thereprocase/peg/publication/mh01-mh04-shaft-holders-v1.md

## MH01-MH04 v1 — magnetic shaft holders from the MS01 result (form review)

User reported the physical MS01 result on 2026-09-17: letters E, I, M, O, and asked
for final holders: a narrow six-seat E bar for jeweler drivers, eight seats each of
I and M, and a four-seat O bar with extra handle spacing, all tiling on the grid.
User chose paired four-seat modules for the eight-seat rows and sealed
pause-and-cap magnets.

`magnetic_shaft_holders.py` in the holder workspace reuses the MS01 seat, 0.8 mm
skin, sealed v2 pocket/plug and canonical fit e586ab4ff6. Only width, seat count
and pitch change. Seat pitch = cells x 25.4 / seats, so spacing continues across
the 2 mm seam. MH01 E 6 seats / 4 cells / 16.93 mm; MH02 I 4 / 7 / 44.45;
MH03 M 4 / 8 / 50.8; MH04 O 4 / 8 / 50.8. MH02 and MH03 print twice. 26 magnets.

CAD single solids, STEP round trips, peg flats on the bed plane, bearing contact,
lift/forward withdrawal with neighbours seated, 0.99-1.04 mm magnet gap and pause
loading path pass. Handle envelopes are nominal. NOT sliced, no supports review,
no pause-layer verification, no physical print. No job sent to a printer.

### Print kit — same day

User approved the forms and asked for the Orca job. Native P1S / 0.4 / Generic PLA /
textured PEI five-plate job with the MS01 v2 process overrides: 26 plugs 12.54 g /
41m48s; MH01 71.72 g / 3h1m29s; MH02 108.04 g / 4h2m19s (print twice); MH03
120.94 g / 4h27m40s (print twice); MH04 120.87 g / 4h23m24s. One native pause per
holder plate before layer 38.2 with 38.0 complete; zero extrusion inside any of the
18 magnet chimneys below 38.0; every chimney first closes at 38.2. Nothing outside
the bed, no mesh repairs, path accounting and startup clearance pass, embedded
settings reslice. Orca's bed-temperature notice retained. Desktop GUI opening,
support removal and the physical print remain untested. No job sent to a printer.
Second release: mh01-mh04-shaft-holders-v1-print-kit (print kit ZIP, PRINT-ME,
EDIT-ME). The first release's 13 assets are unchanged.

Gallery: https://thereprocase.github.io/peg/gallery/shaft-holders/
Release: mh01-mh04-shaft-holders-v1 (12 STEP files and the review CAD kit ZIP).
Receipts: `mh01-mh04-shaft-holders-v1-additions.json`; `tools/check_gallery.py`
verifies their hashes. Staged by `publish_magnetic_shaft_holders.py`.
