thereprocase/peg/docs/gallery/arrays/P01-12/rear.png

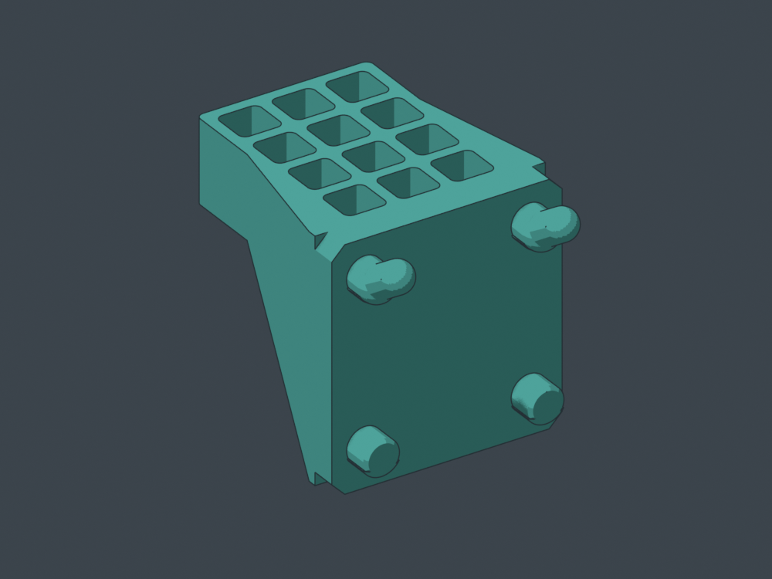
docs/gallery/arrays/P01-12/rear.png
