thereprocase/peg/docs/gallery/arrays/P01-24/front.png

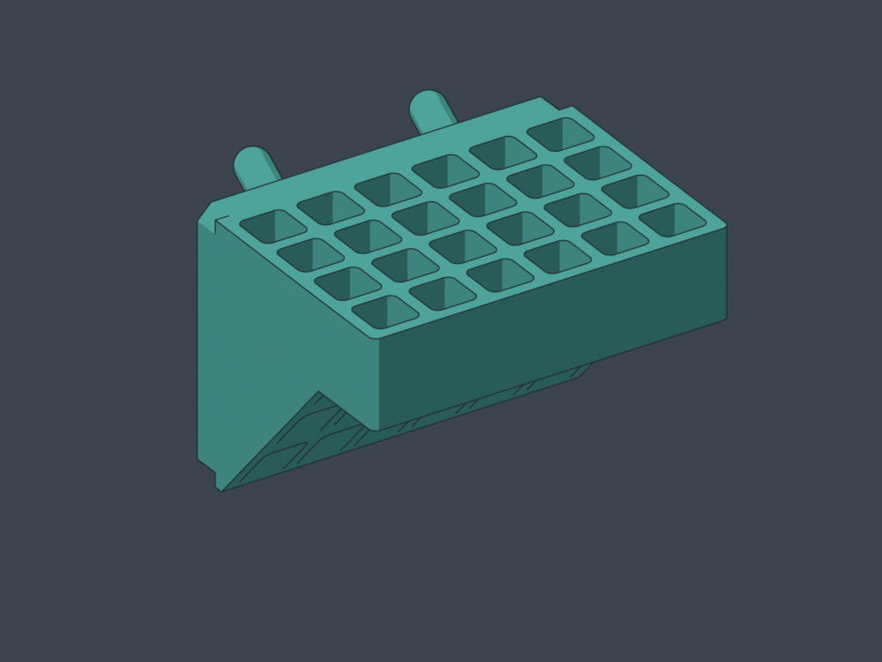
docs/gallery/arrays/P01-24/front.png
