thereprocase/peg/docs/gallery/arrays/P01-32/front.png

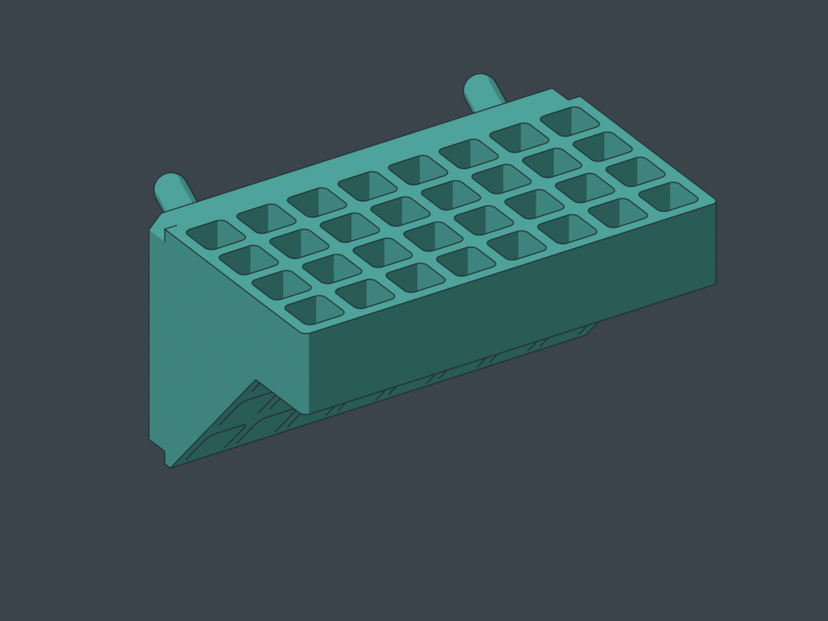
docs/gallery/arrays/P01-32/front.png
