thereprocase/peg/docs/gallery/arrays/P01-32/rear.png

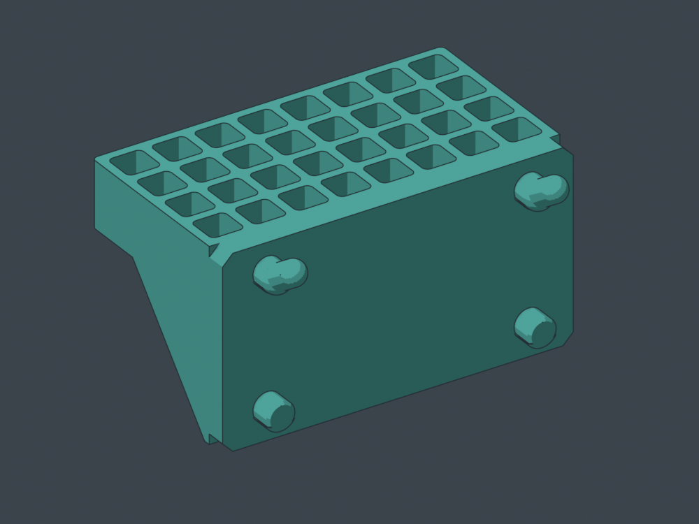
docs/gallery/arrays/P01-32/rear.png
