thereprocase/peg/docs/gallery/arrays/P01-48/rear.png

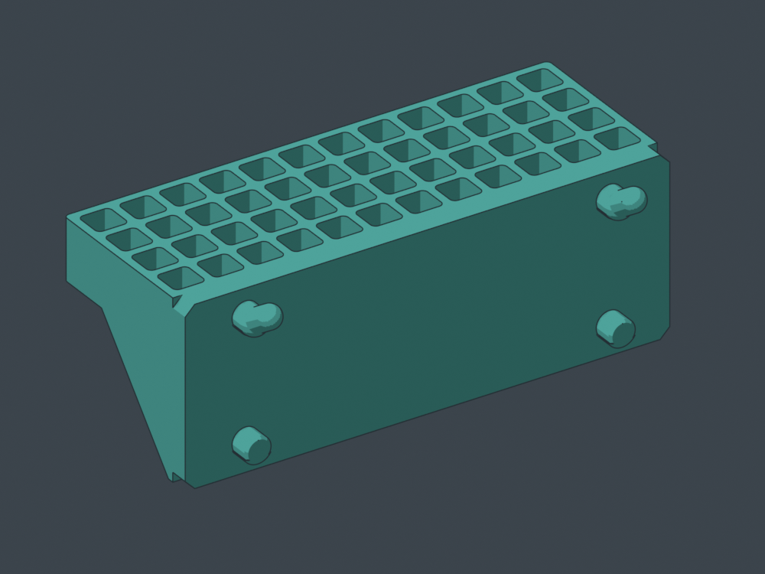
docs/gallery/arrays/P01-48/rear.png
