thereprocase/peg/docs/gallery/arrays/P01-labeled.png

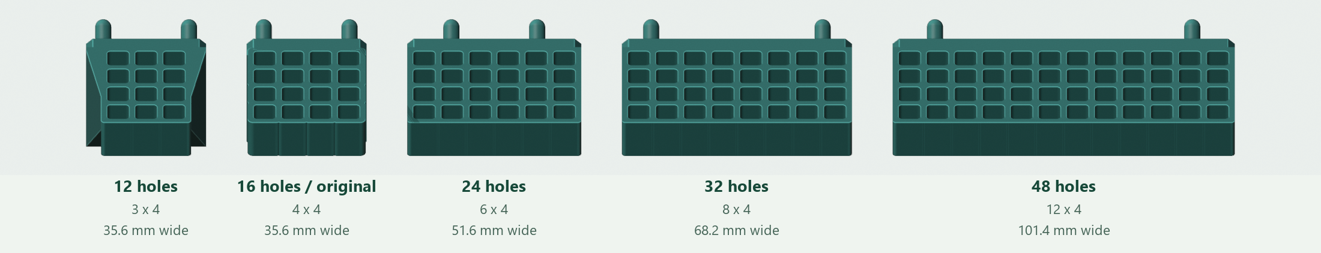
docs/gallery/arrays/P01-labeled.png
