thereprocase/peg/docs/gallery/arrays/P09-16/rear.png

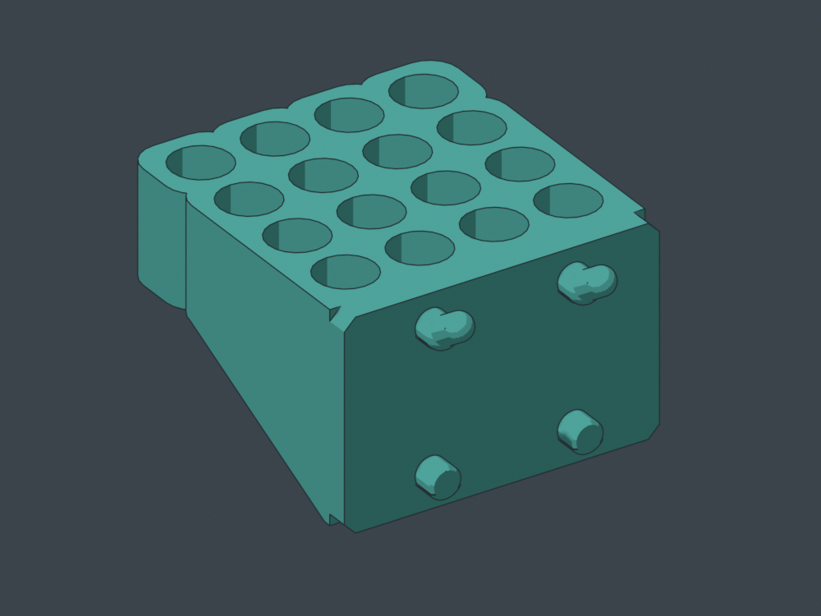
docs/gallery/arrays/P09-16/rear.png
