thereprocase/peg/docs/gallery/arrays/P09-36/front.png

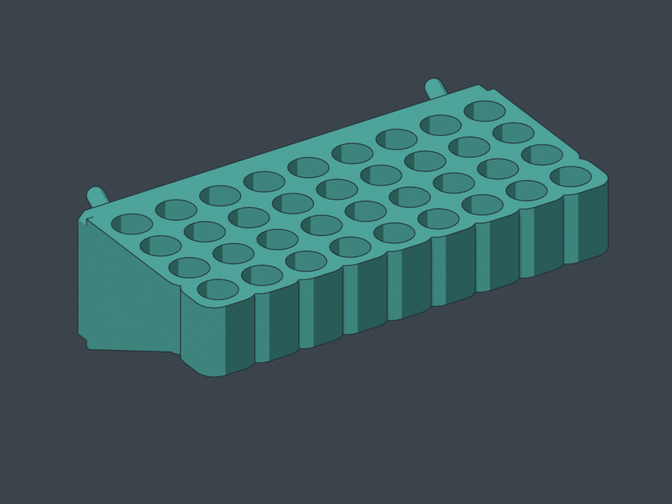
docs/gallery/arrays/P09-36/front.png
