thereprocase/peg/docs/gallery/arrays/P09-48/rear.png

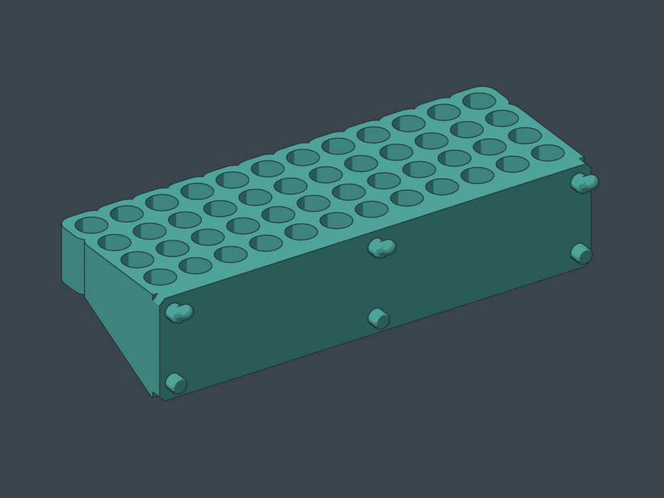
docs/gallery/arrays/P09-48/rear.png
