thereprocase/peg/docs/gallery/arrays/P09-comparison.png

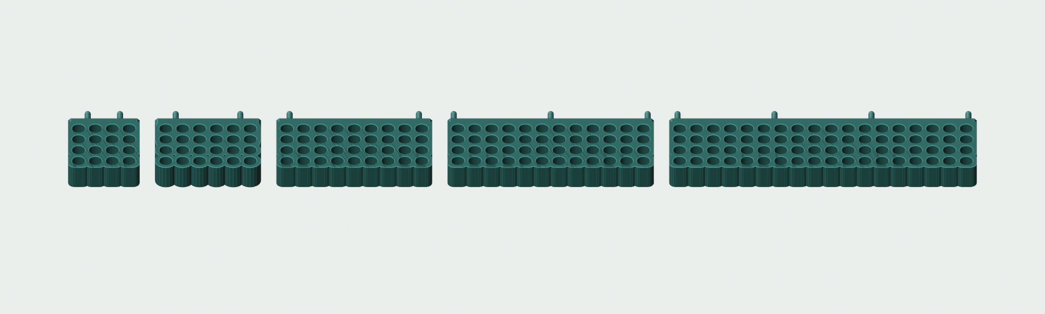
docs/gallery/arrays/P09-comparison.png
