thereprocase/peg/docs/gallery/bin-expansion/PB01/part-pb01__v1__pegstr-bin-4-cells-1-pockets-99.6x40x40mm__fit-e586ab4ff6__rear.png

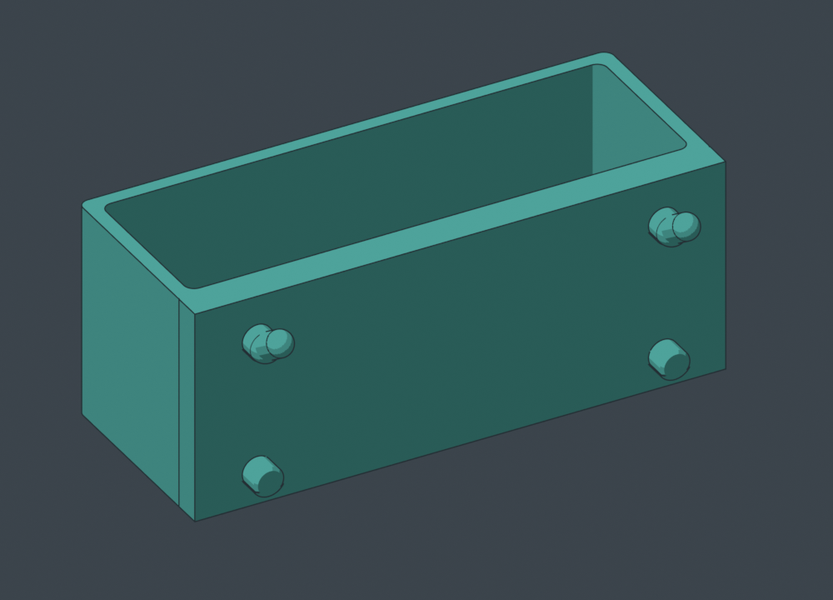
docs/gallery/bin-expansion/PB01/part-pb01__v1__pegstr-bin-4-cells-1-pockets-99.6x40x40mm__fit-e586ab4ff6__rear.png
