thereprocase/peg/docs/gallery/bit-drivers/part-bd01-slope-e__v1__rear-mounts.png

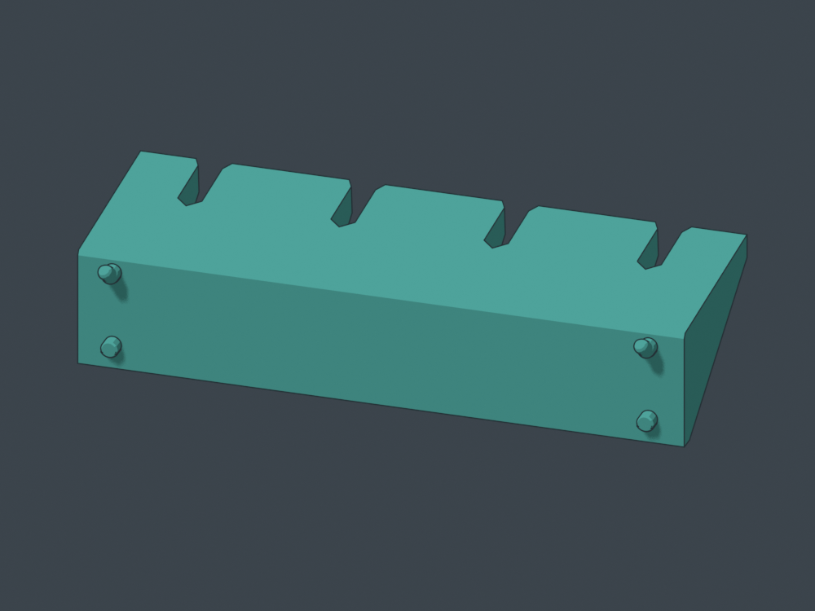
docs/gallery/bit-drivers/part-bd01-slope-e__v1__rear-mounts.png
