thereprocase/peg/docs/gallery/bit-drivers/part-bd01-slope-e__v4__bed-contact-faces.png

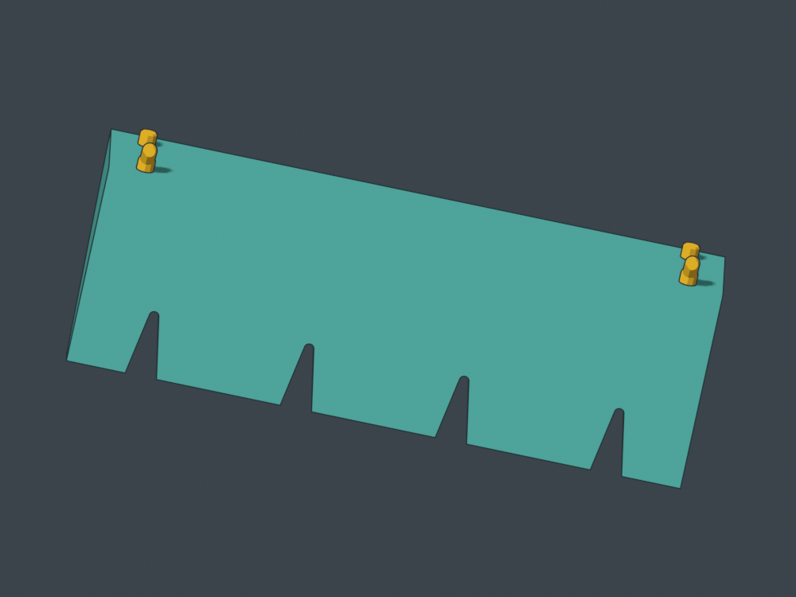
docs/gallery/bit-drivers/part-bd01-slope-e__v4__bed-contact-faces.png
