thereprocase/peg/docs/gallery/bit-drivers/part-bd01-slope-e__v4__loaded-review.png

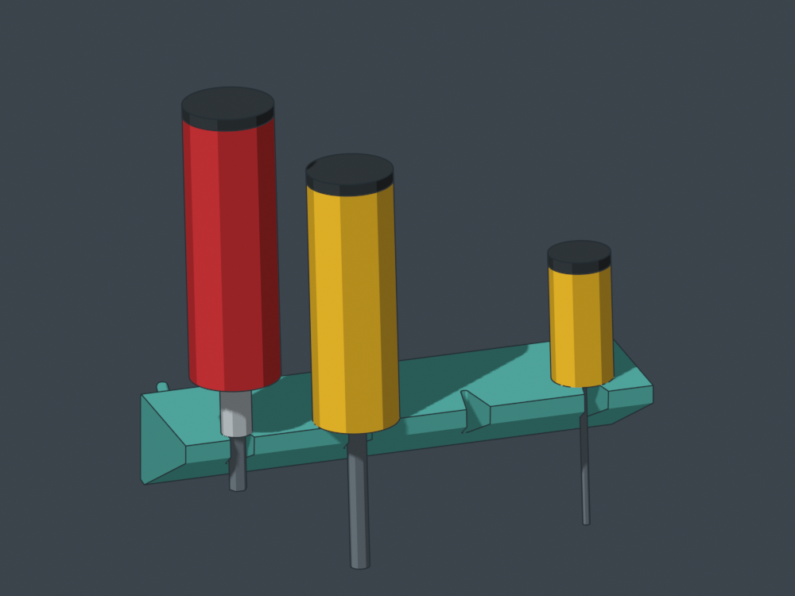
docs/gallery/bit-drivers/part-bd01-slope-e__v4__loaded-review.png
