thereprocase/peg/docs/gallery/current-pegs/part-ms01-i-p__current-mounts-v1__fit-pf02c9-hoop5__preview.png

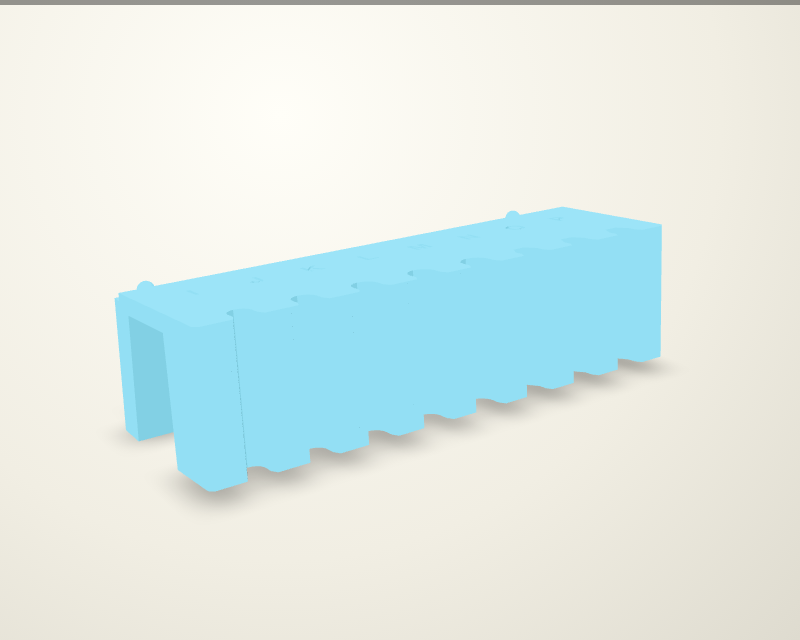
docs/gallery/current-pegs/part-ms01-i-p__current-mounts-v1__fit-pf02c9-hoop5__preview.png
