thereprocase/peg/docs/gallery/current-pegs/part-p09-48__current-mounts-flat-top-v2__fit-pf02c9-hoop5__preview.png

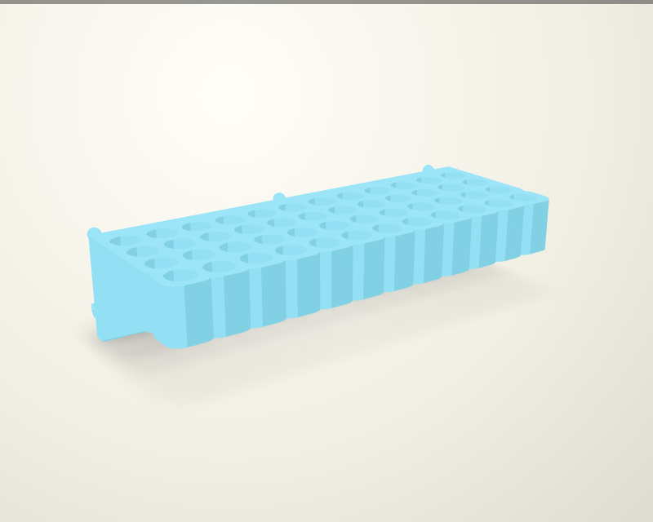
docs/gallery/current-pegs/part-p09-48__current-mounts-flat-top-v2__fit-pf02c9-hoop5__preview.png
