thereprocase/peg/docs/gallery/current-pegs/part-tweezers-v8__current-mounts-v1__fit-pf02c9-hoop5__preview.png

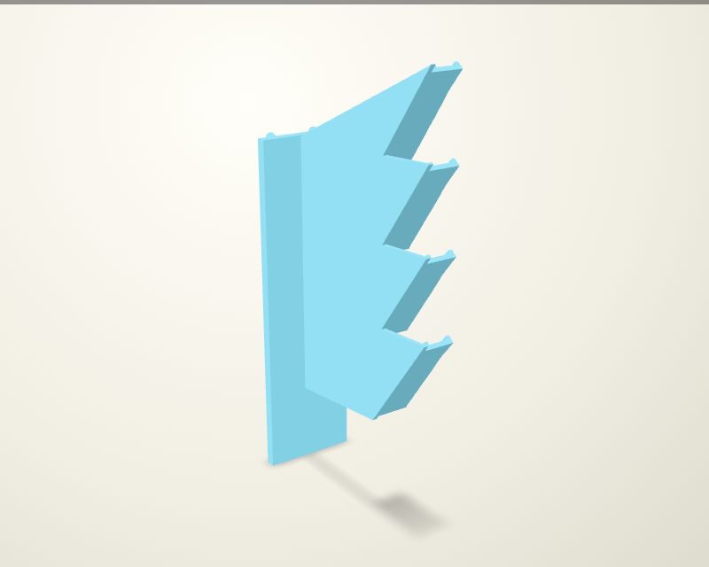
docs/gallery/current-pegs/part-tweezers-v8__current-mounts-v1__fit-pf02c9-hoop5__preview.png
