thereprocase/peg/docs/gallery/downloads/named/part-arrays-p09-48__v-src0e00429f35__pegstr-array-p09-48-round-seats__front-view.png

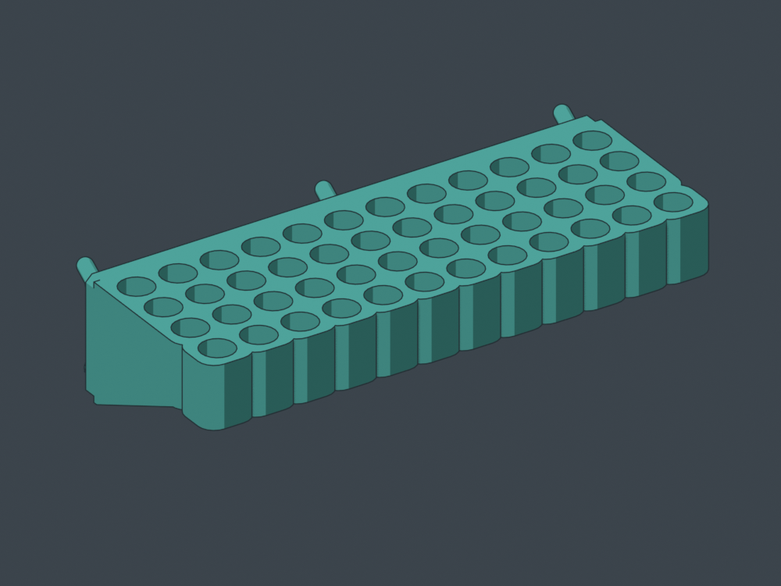
docs/gallery/downloads/named/part-arrays-p09-48__v-src0e00429f35__pegstr-array-p09-48-round-seats__front-view.png
