thereprocase/peg/docs/gallery/downloads/named/part-pegstr-p01__v2__pegstr-p01-16-small-square-seats__front-view.png

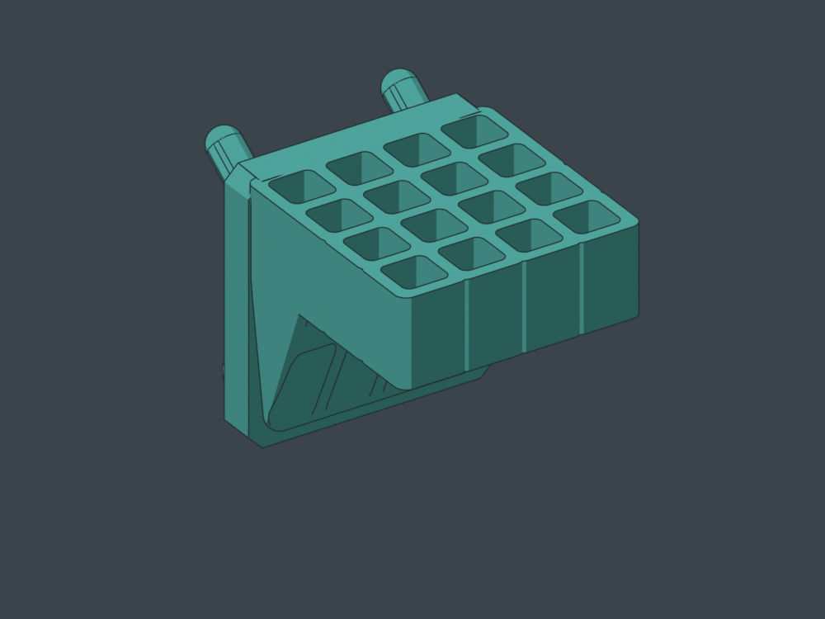
docs/gallery/downloads/named/part-pegstr-p01__v2__pegstr-p01-16-small-square-seats__front-view.png
