thereprocase/peg/docs/gallery/downloads/named/part-pegstr-p09__v2__pegstr-p09-24-round-seats__rear-view.png

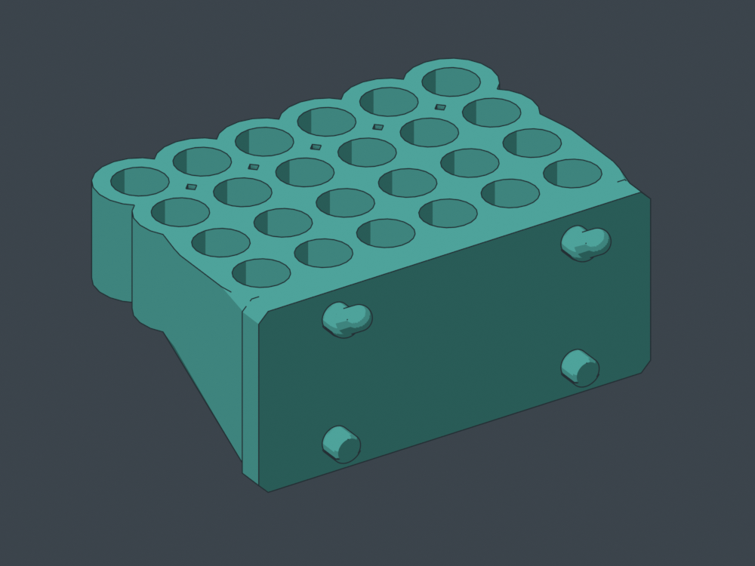
docs/gallery/downloads/named/part-pegstr-p09__v2__pegstr-p09-24-round-seats__rear-view.png
