thereprocase/peg/docs/gallery/downloads/named/part-pegstr-p10__v2__pegstr-p10-low-rectangular-slot__rear-view.png

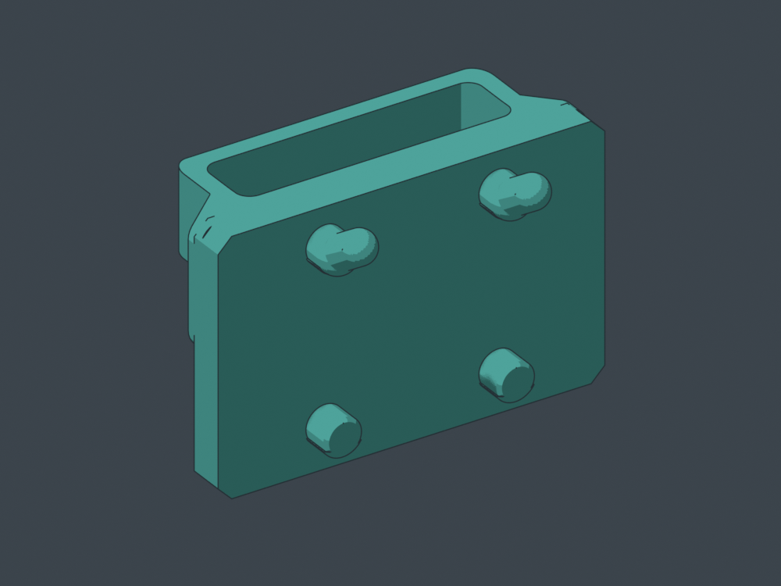
docs/gallery/downloads/named/part-pegstr-p10__v2__pegstr-p10-low-rectangular-slot__rear-view.png
