thereprocase/peg/docs/gallery/downloads/named/part-pegstr-p11__v2__pegstr-p11-caliper-slot__front-view.png

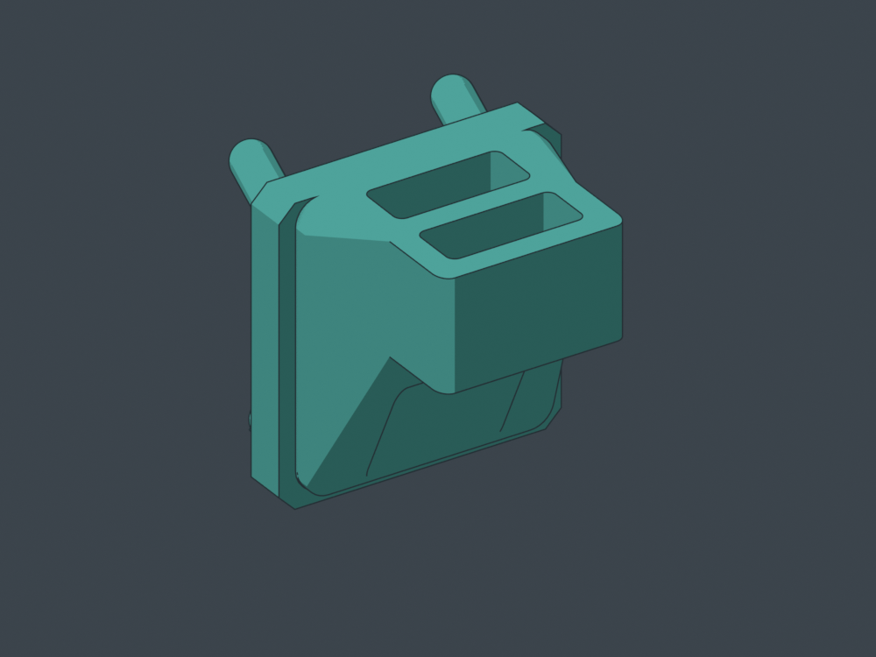
docs/gallery/downloads/named/part-pegstr-p11__v2__pegstr-p11-caliper-slot__front-view.png
