thereprocase/peg/docs/gallery/key-fan/final/HX04/empty.jpg

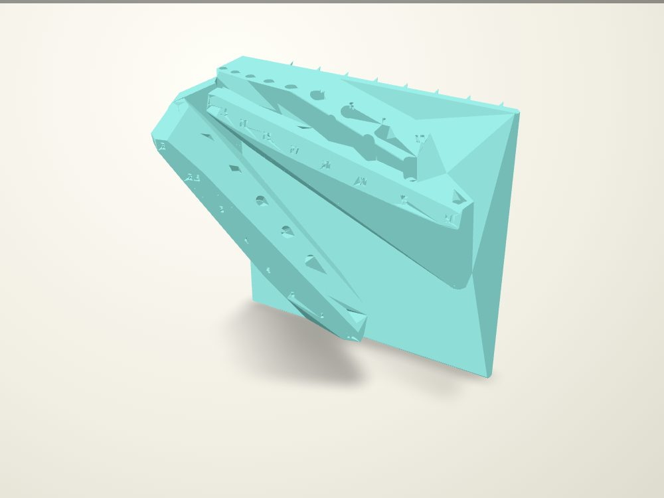
docs/gallery/key-fan/final/HX04/empty.jpg
