thereprocase/peg/docs/gallery/key-fan/final/HX05B/hero.jpg

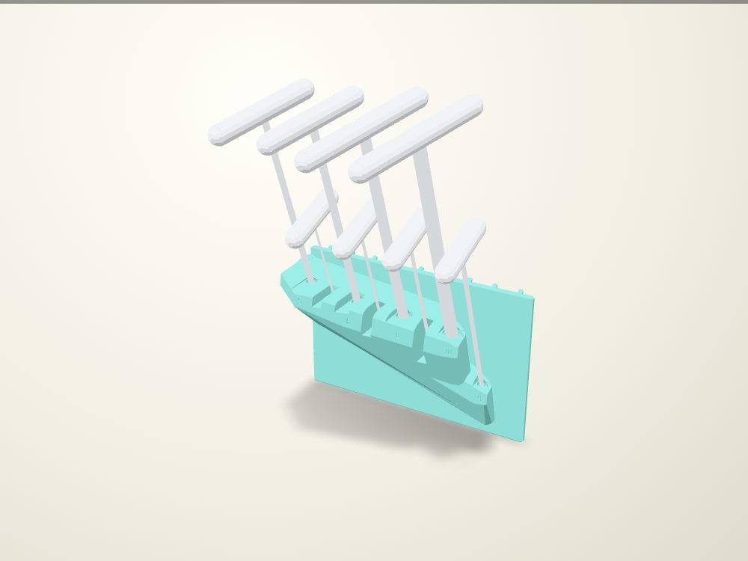
docs/gallery/key-fan/final/HX05B/hero.jpg
