thereprocase/peg/docs/gallery/key-fan/final/HX05C/empty.jpg

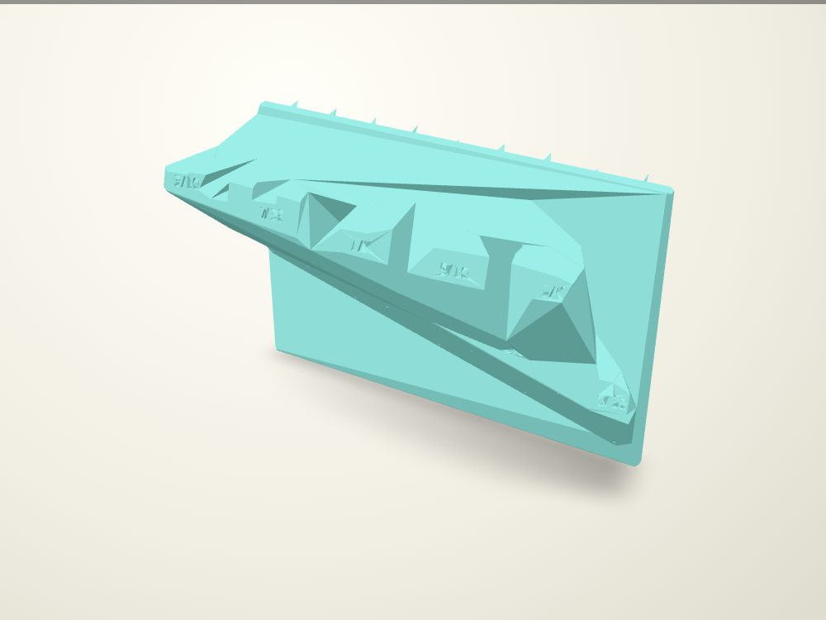
docs/gallery/key-fan/final/HX05C/empty.jpg
