thereprocase/peg/docs/gallery/key-fan/stacked/green/HX05C-front.jpg

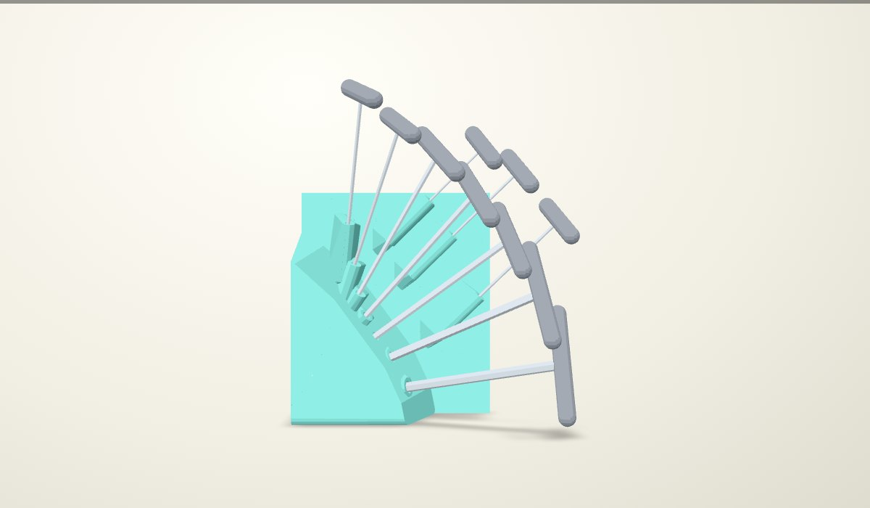
docs/gallery/key-fan/stacked/green/HX05C-front.jpg
