thereprocase/peg/docs/gallery/key-fan/stacked/HX05C-hero.jpg

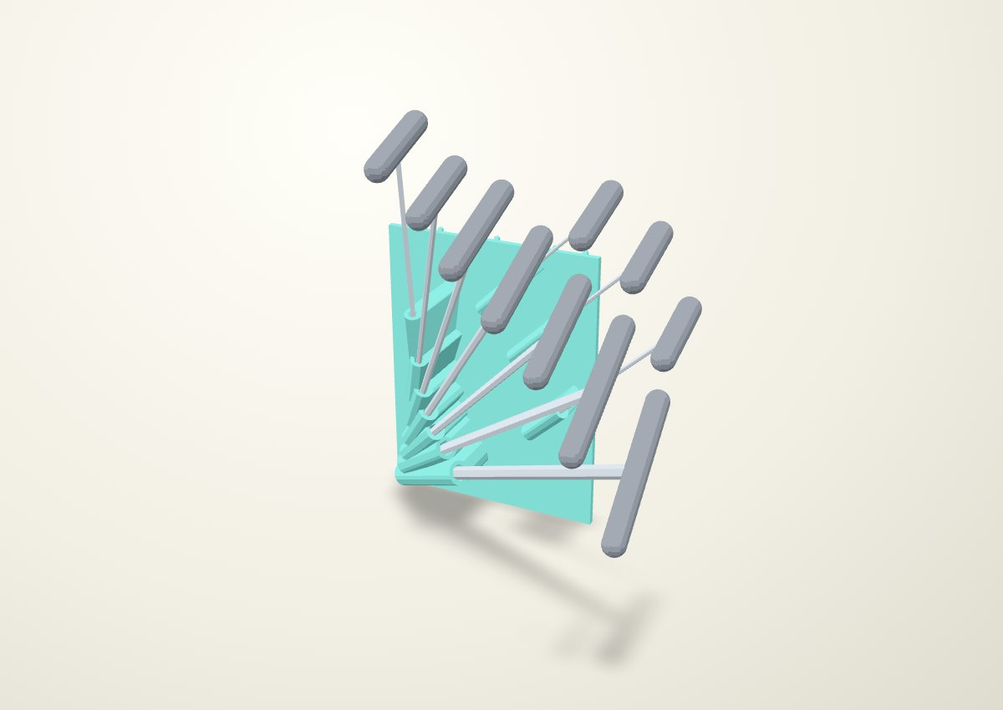
docs/gallery/key-fan/stacked/HX05C-hero.jpg
