thereprocase/peg/docs/gallery/key-fan/stacked/stack-hero.jpg

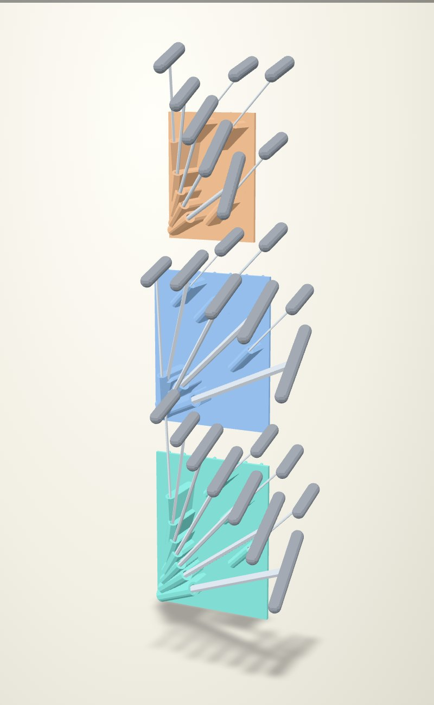
docs/gallery/key-fan/stacked/stack-hero.jpg
