thereprocase/peg/docs/gallery/key-fan/studies/media/flexure-cel-all-pegs-4.jpg

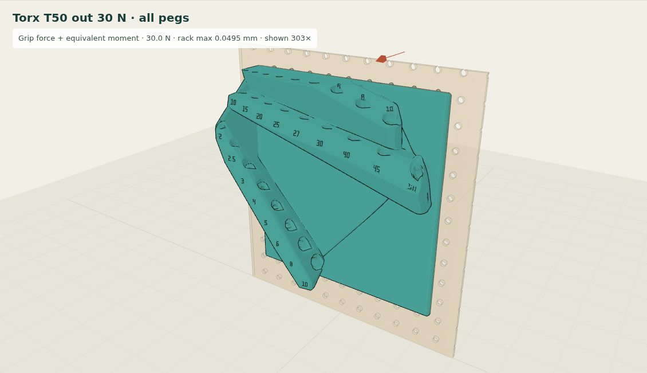
docs/gallery/key-fan/studies/media/flexure-cel-all-pegs-4.jpg
