thereprocase/peg/docs/gallery/key-fan/studies/media/motion-hex-3.jpg

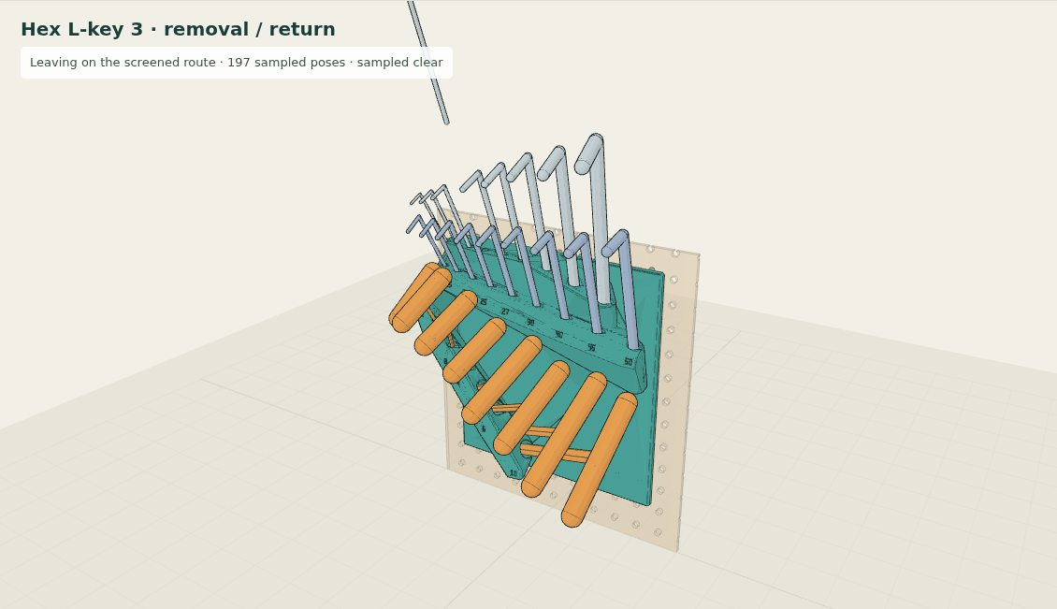
docs/gallery/key-fan/studies/media/motion-hex-3.jpg
