thereprocase/peg/docs/gallery/key-fan/studies/media/motion-hex-5.jpg

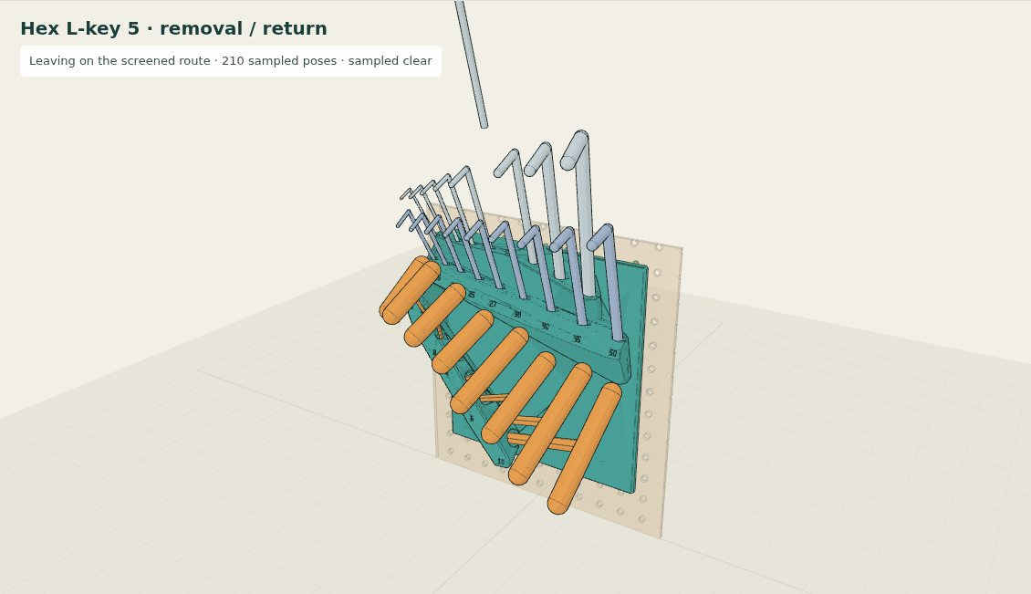
docs/gallery/key-fan/studies/media/motion-hex-5.jpg
