thereprocase/peg/docs/gallery/key-fan/studies/media/stress-all-pegs-grip-wrench-2.jpg

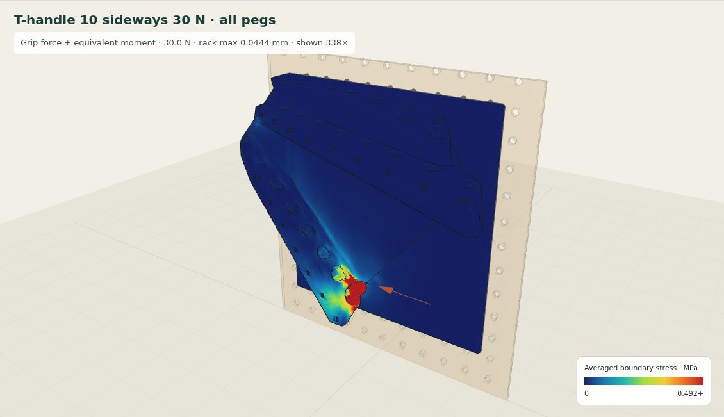
docs/gallery/key-fan/studies/media/stress-all-pegs-grip-wrench-2.jpg
