thereprocase/peg/docs/gallery/key-fan/studies/media/stress-all-pegs-mouth-4.jpg

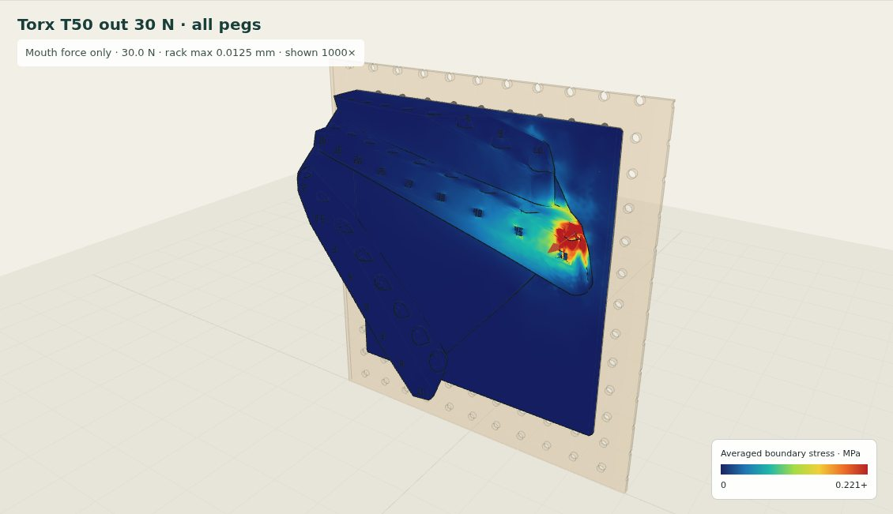
docs/gallery/key-fan/studies/media/stress-all-pegs-mouth-4.jpg
