thereprocase/peg/docs/gallery/key-fan/studies/media/stress-hooks-only-grip-wrench-3.jpg

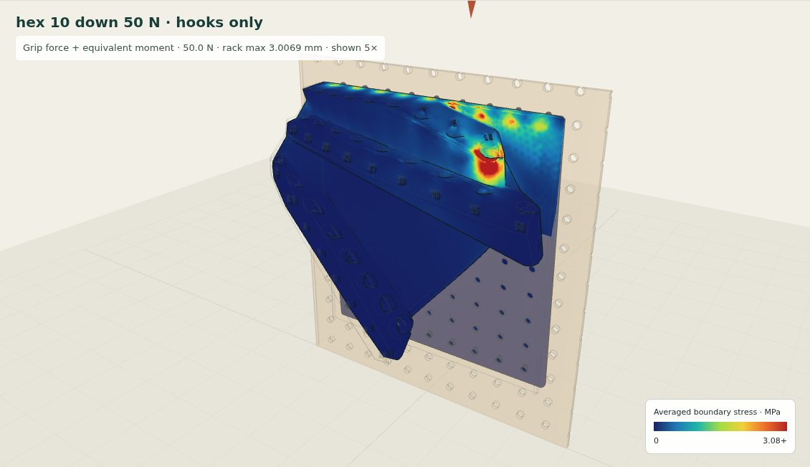
docs/gallery/key-fan/studies/media/stress-hooks-only-grip-wrench-3.jpg
