thereprocase/peg/docs/gallery/magnetic-bar/part-mb01-magnetic-shaft-bar-f__v1__magnet-cutaway.png

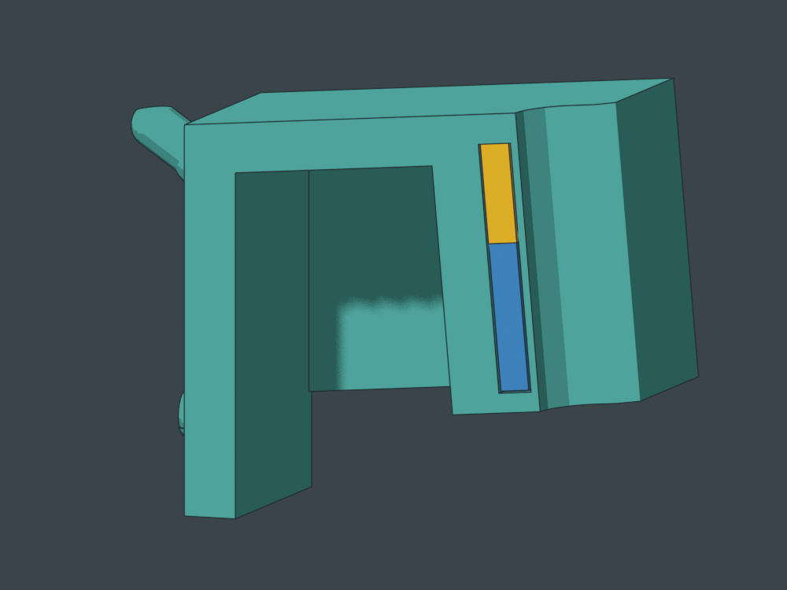
docs/gallery/magnetic-bar/part-mb01-magnetic-shaft-bar-f__v1__magnet-cutaway.png
