thereprocase/peg/docs/gallery/magnetic-bar/part-mb01-magnetic-shaft-bar-f__v1__rear-mounts.png

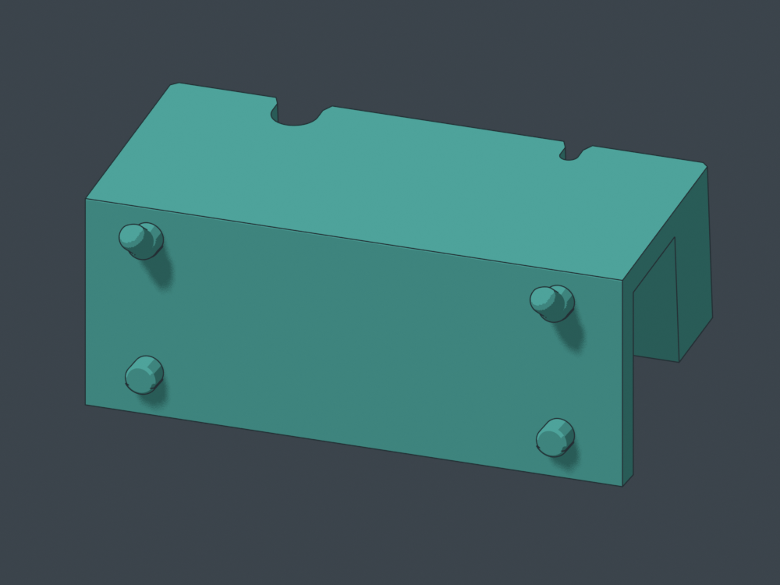
docs/gallery/magnetic-bar/part-mb01-magnetic-shaft-bar-f__v1__rear-mounts.png
