thereprocase/peg/docs/gallery/pegstr/P04/rear.png

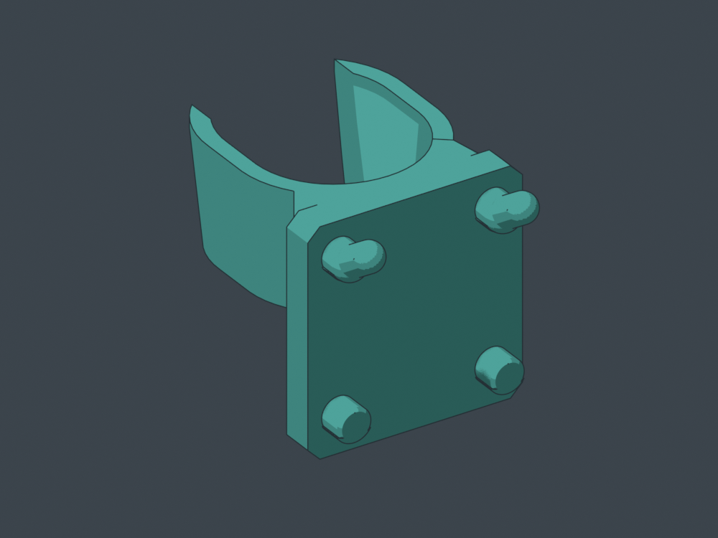
docs/gallery/pegstr/P04/rear.png
