thereprocase/peg/docs/gallery/screwdrivers-b/SD02/part-sd02__v3__flat-b-toolpaths.png

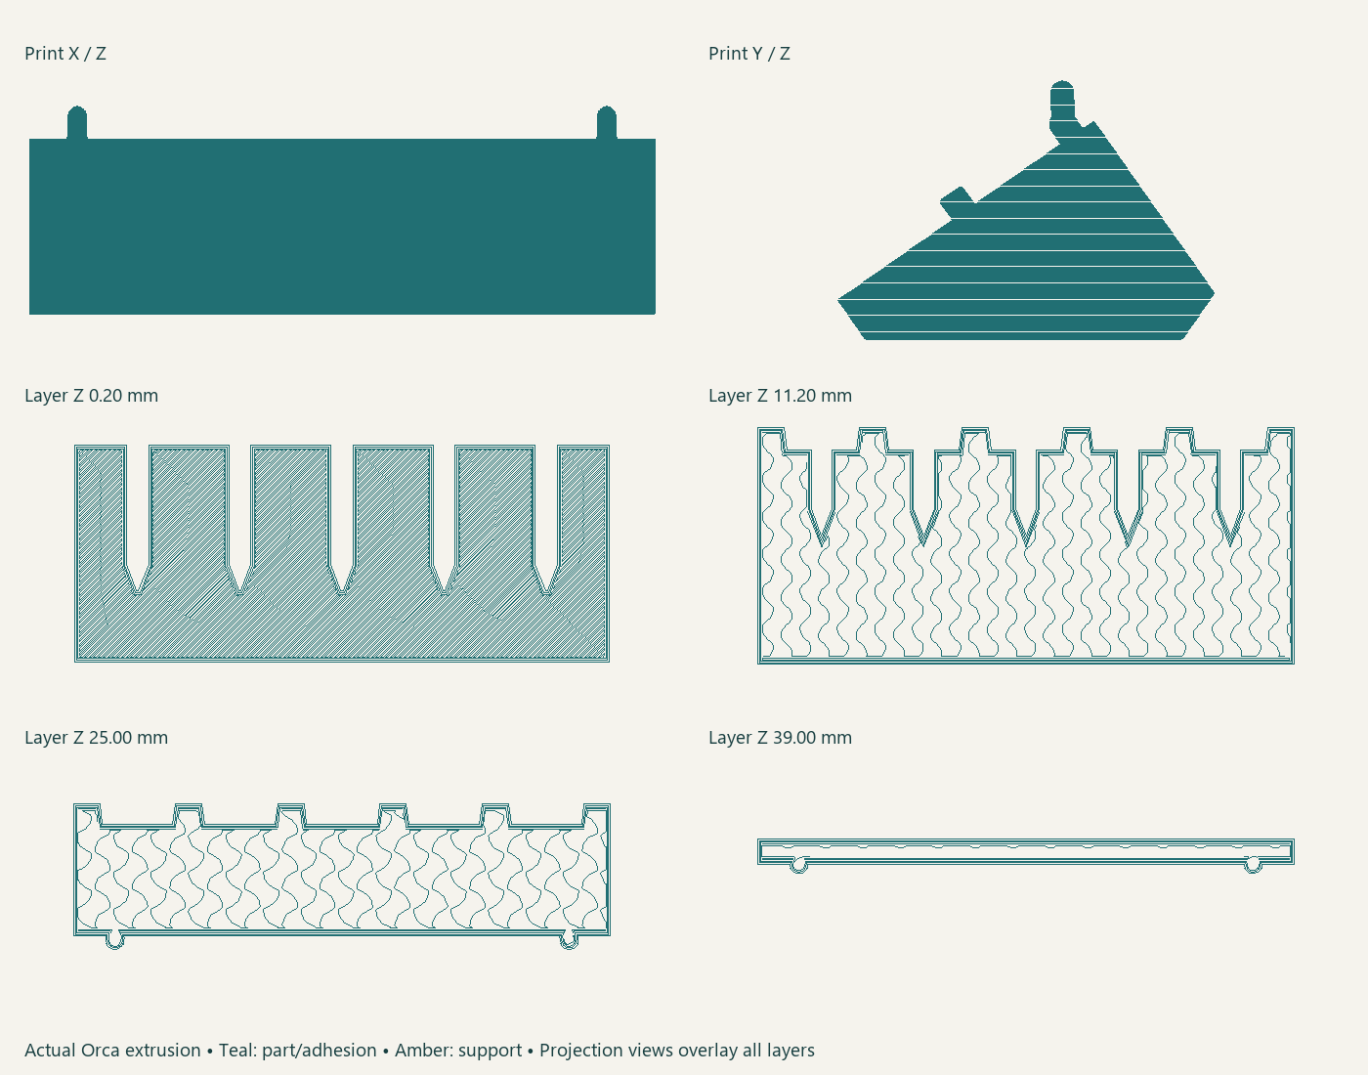
docs/gallery/screwdrivers-b/SD02/part-sd02__v3__flat-b-toolpaths.png
