thereprocase/peg/docs/gallery/screwdrivers-b/SD03/part-sd03__v3__flat-b-toolpaths.png

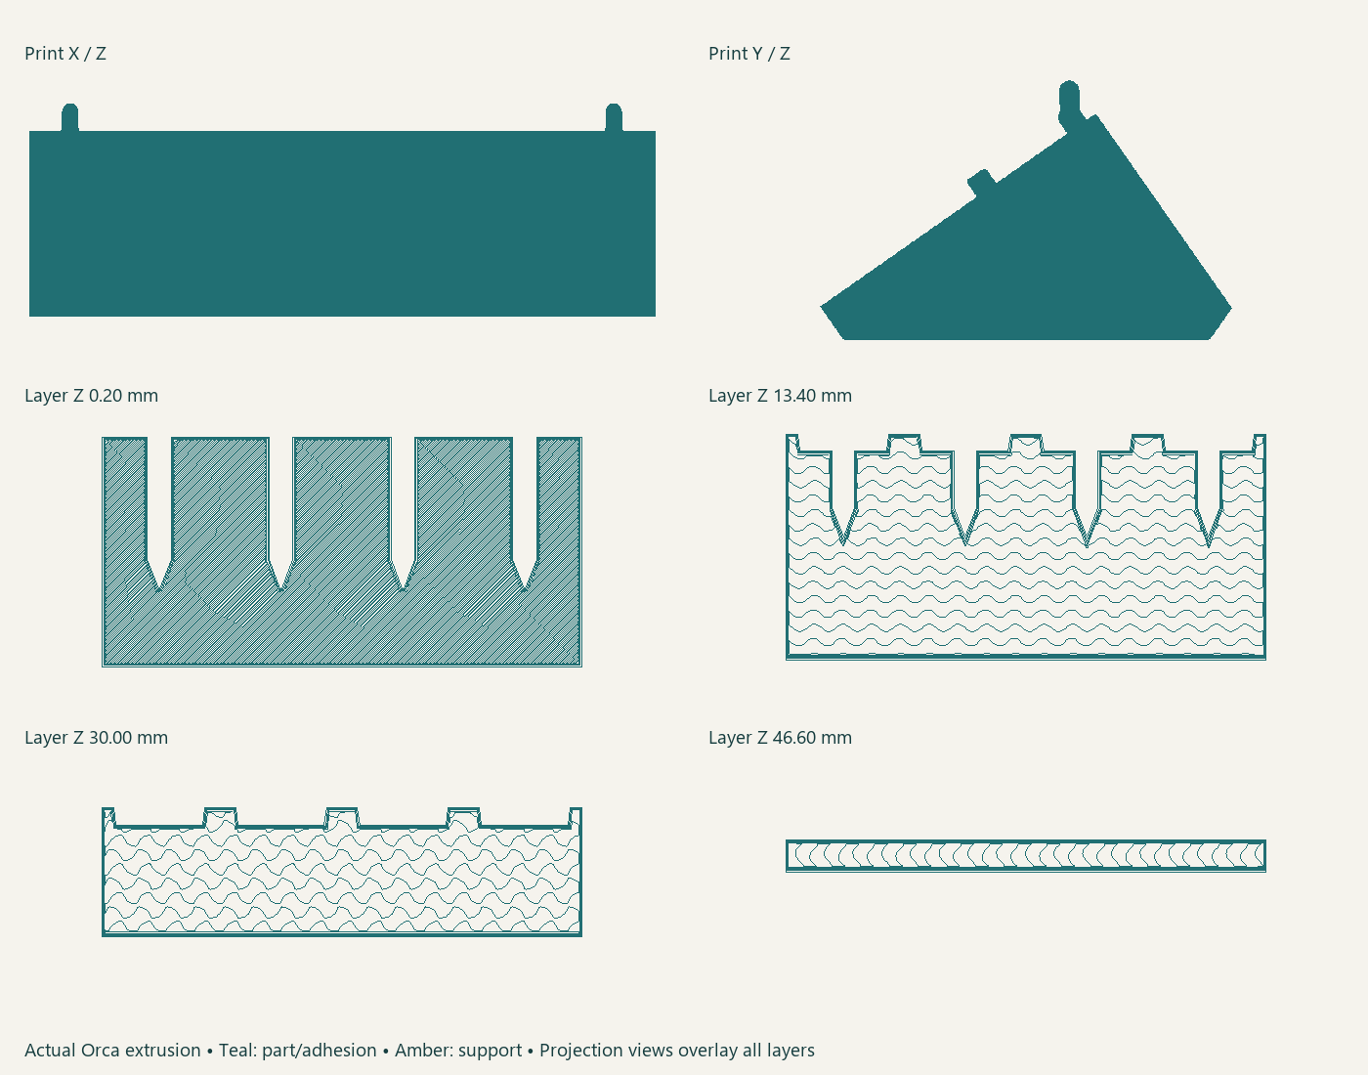
docs/gallery/screwdrivers-b/SD03/part-sd03__v3__flat-b-toolpaths.png
