thereprocase/peg/docs/gallery/screwdrivers-b/SD04/part-sd04__v3__flat-b-toolpaths.png

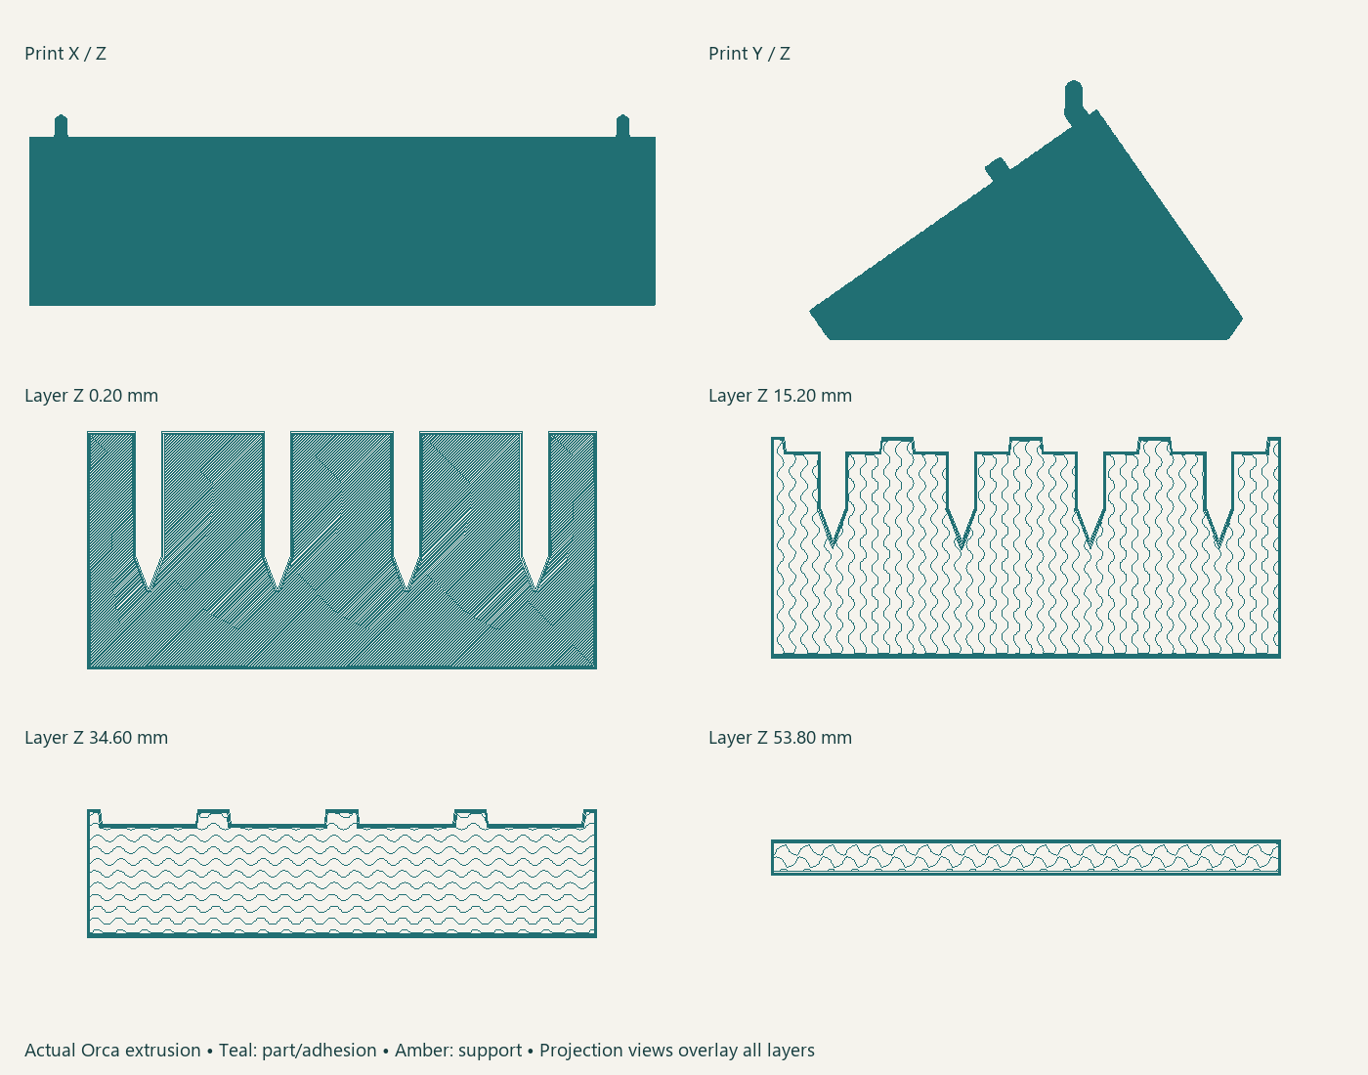
docs/gallery/screwdrivers-b/SD04/part-sd04__v3__flat-b-toolpaths.png
