thereprocase/peg/docs/gallery/screwdrivers-c/part-sd03-magnetic-c__v1__sealed-section.png

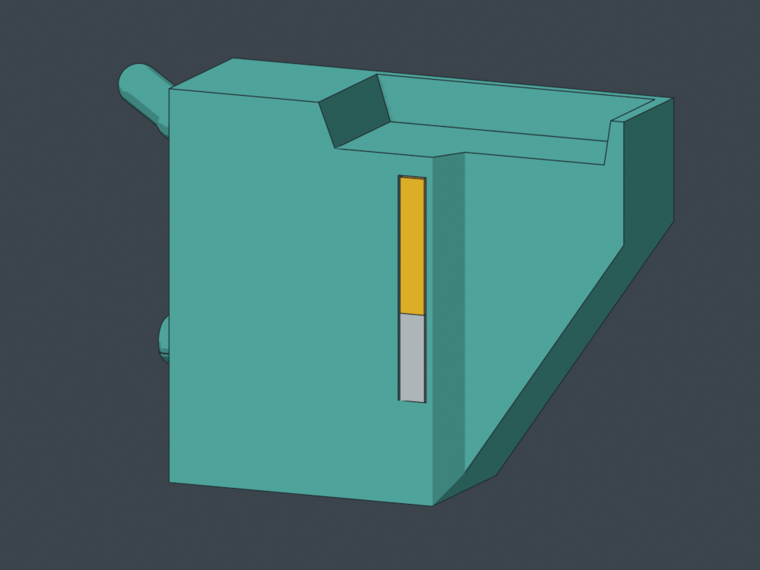
docs/gallery/screwdrivers-c/part-sd03-magnetic-c__v1__sealed-section.png
