thereprocase/peg/docs/gallery/screwdrivers/part-screwdriver-family__v2__loaded-lineup.png

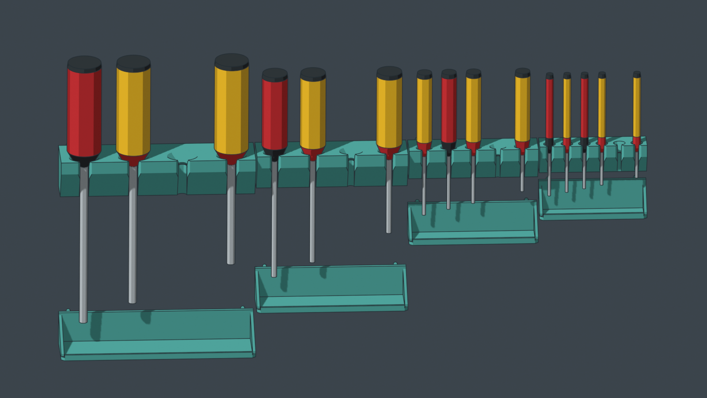
docs/gallery/screwdrivers/part-screwdriver-family__v2__loaded-lineup.png
