thereprocase/peg/docs/gallery/shaft-holders/part-mh01-magnetic-shaft-holder-jeweler-4mm-round__v1__loaded.png

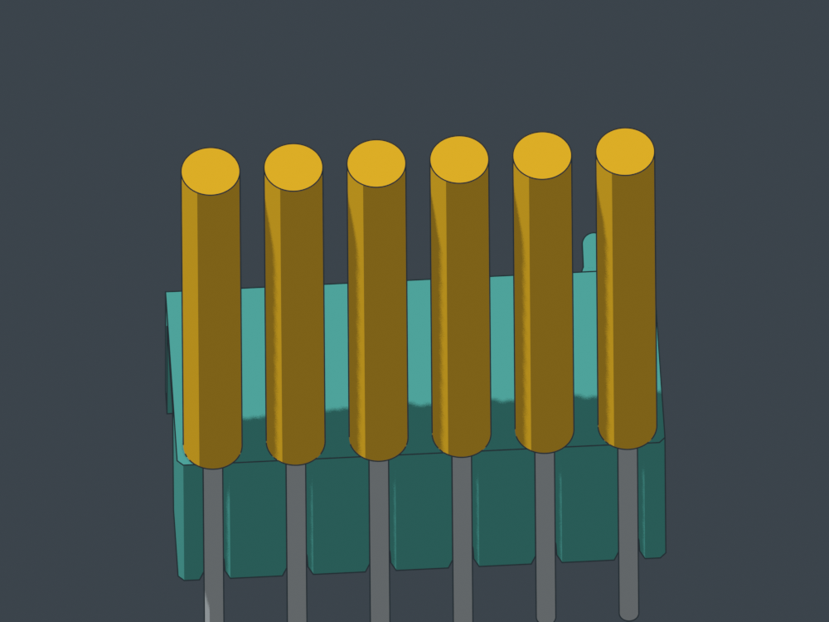
docs/gallery/shaft-holders/part-mh01-magnetic-shaft-holder-jeweler-4mm-round__v1__loaded.png
