thereprocase/peg/docs/gallery/shaft-holders/part-mh01-magnetic-shaft-holder-jeweler-4mm-round__v1__magnets-behind-shafts.png

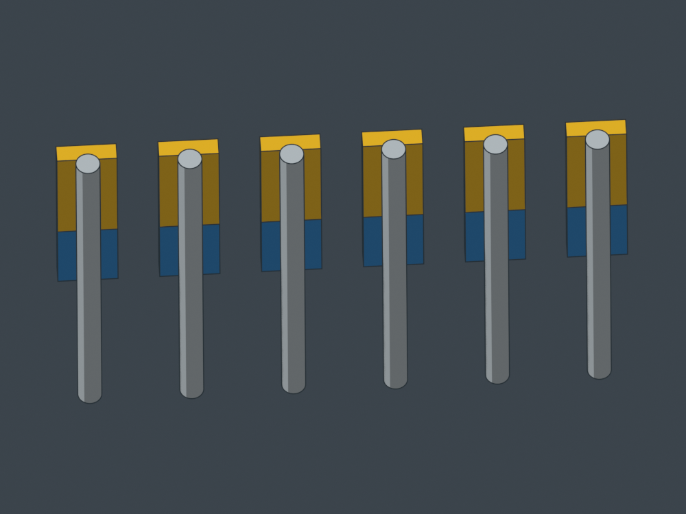
docs/gallery/shaft-holders/part-mh01-magnetic-shaft-holder-jeweler-4mm-round__v1__magnets-behind-shafts.png
