thereprocase/peg/docs/gallery/shaft-holders/part-mh02-magnetic-shaft-holder-6mm-round__v1__empty-seats.png

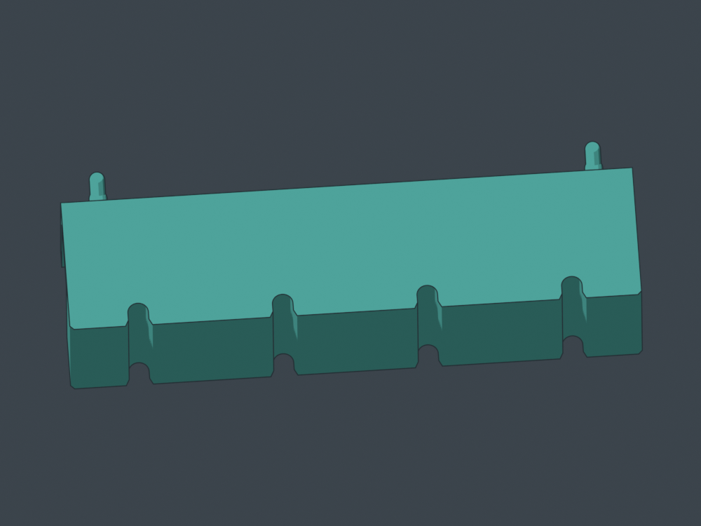
docs/gallery/shaft-holders/part-mh02-magnetic-shaft-holder-6mm-round__v1__empty-seats.png
