thereprocase/peg/docs/gallery/shaft-holders/part-mh03-magnetic-shaft-holder-8mm-round__v1__rear-pegs.png

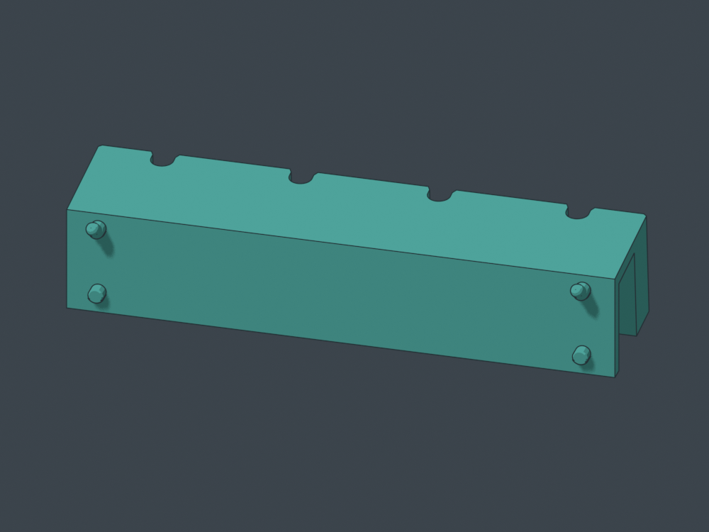
docs/gallery/shaft-holders/part-mh03-magnetic-shaft-holder-8mm-round__v1__rear-pegs.png
