thereprocase/peg/docs/gallery/shaft-holders/part-mh04-magnetic-shaft-holder-quarter-inch-hex__v1__loaded.png

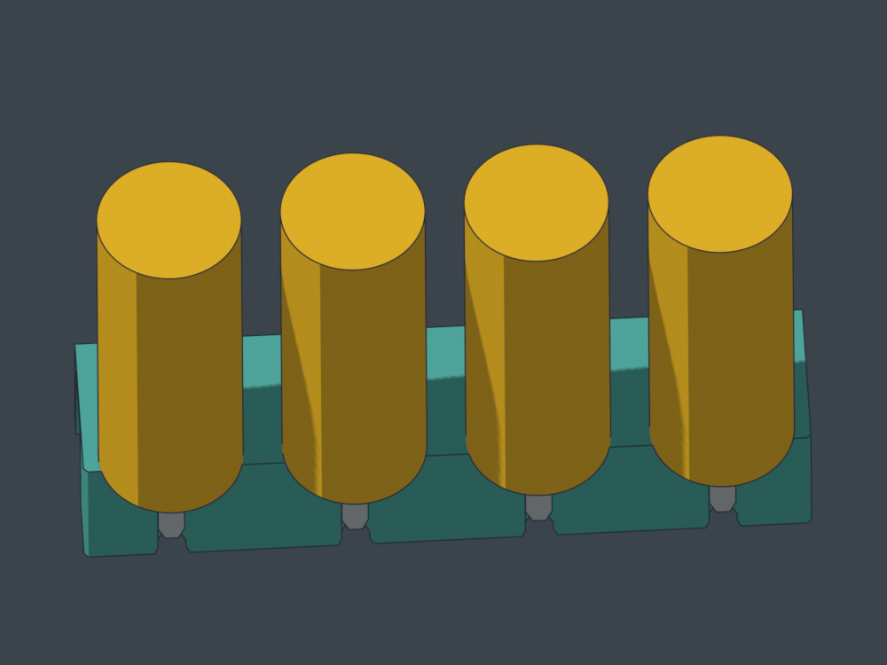
docs/gallery/shaft-holders/part-mh04-magnetic-shaft-holder-quarter-inch-hex__v1__loaded.png
