thereprocase/peg/docs/gallery/arrays/P09-48/original.stl

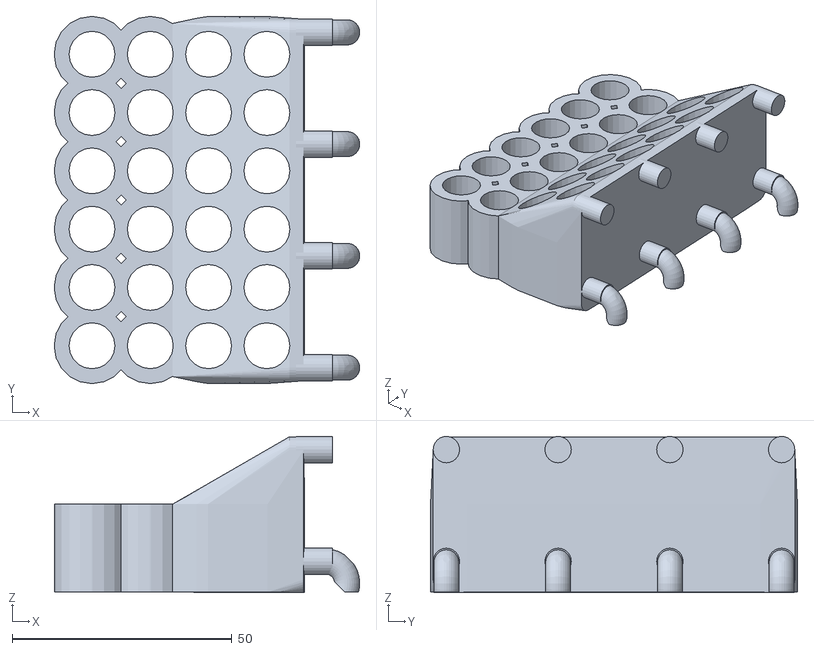
[picture p103: CAD file, 2026-09-16]
docs/gallery/arrays/P09-48/original.stl
69.4 x 83.4 x 35.5
