thereprocase/peg/docs/gallery/arrays/P09-72/print-pose.stl

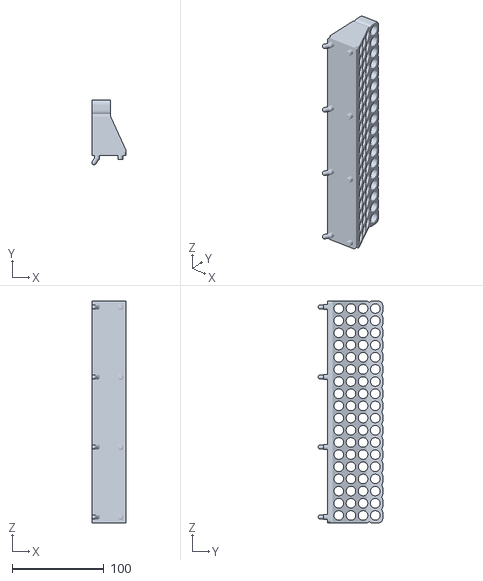
[picture p104: CAD file, 2026-09-16]
docs/gallery/arrays/P09-72/print-pose.stl
37.4 x 70.5 x 241.8
