thereprocase/peg/docs/gallery/bespoke-tools/CL01/part-cl01__v1__right-cheek__fit-pf02c9-hoop5__installed.stl

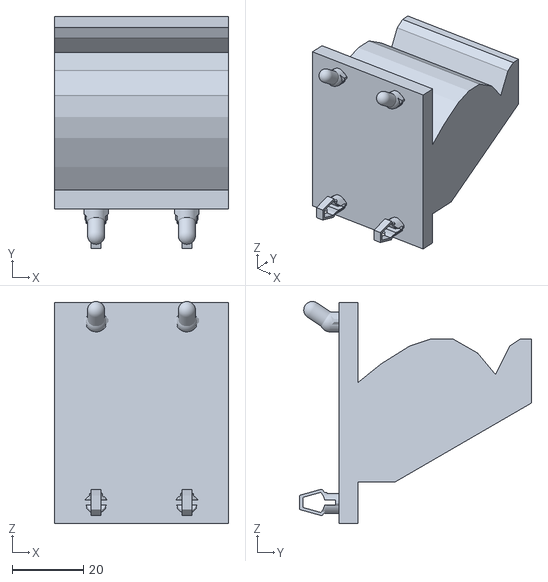
[picture p105: CAD file, 2026-10-06]
docs/gallery/bespoke-tools/CL01/part-cl01__v1__right-cheek__fit-pf02c9-hoop5__installed.stl
48.8 x 64.8 x 62.1
