thereprocase/peg/docs/gallery/bespoke-tools/HX01/part-hx01__v1__upright__fit-pf02c9-hoop5__print.stl

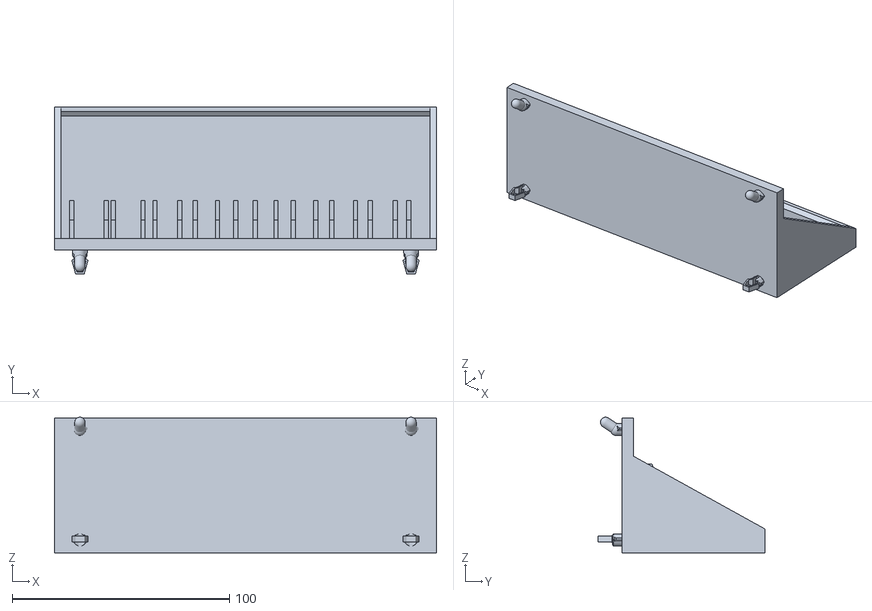
[picture p106: CAD file, 2026-10-06]
docs/gallery/bespoke-tools/HX01/part-hx01__v1__upright__fit-pf02c9-hoop5__print.stl
175.8 x 76.8 x 62.4
