thereprocase/peg/docs/gallery/bespoke-tools/TM01/part-tm01__v1__upright__fit-pf02c9-hoop5__installed.stl

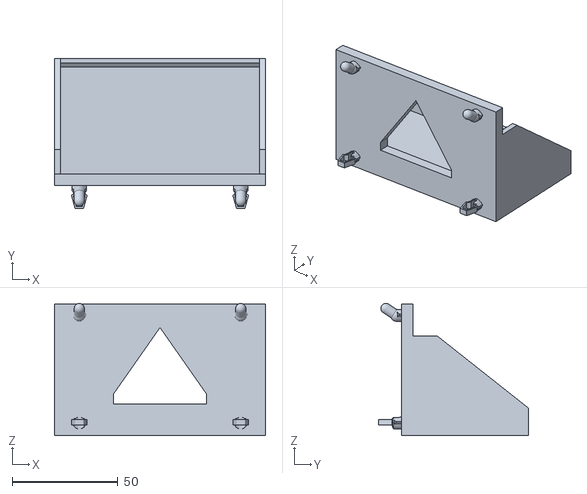
[picture p107: CAD file, 2026-10-06]
docs/gallery/bespoke-tools/TM01/part-tm01__v1__upright__fit-pf02c9-hoop5__installed.stl
99.6 x 70.8 x 62.4
