thereprocase/peg/docs/gallery/bin-expansion/PB01/part-pb01__v1__pegstr-bin-4-cells-1-pockets-99.6x40x40mm__fit-e586ab4ff6__print-flat-base.stl

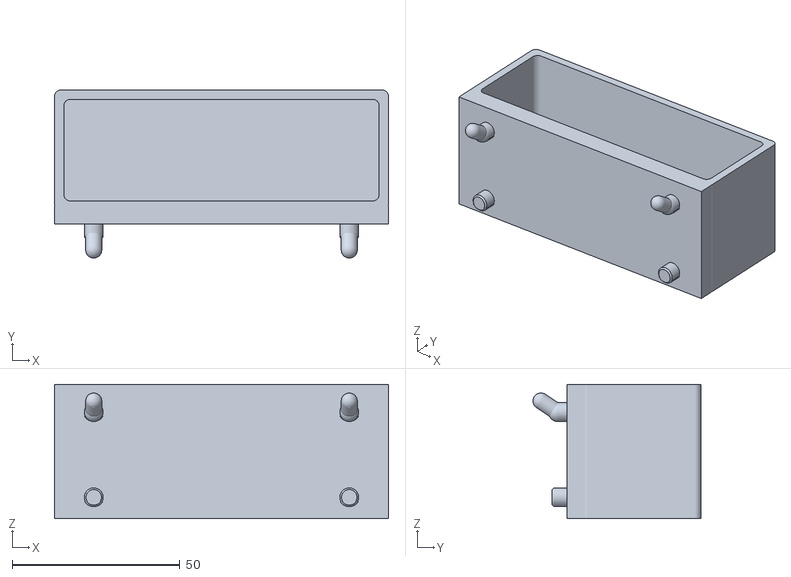
[picture p108: CAD file, 2026-09-16]
docs/gallery/bin-expansion/PB01/part-pb01__v1__pegstr-bin-4-cells-1-pockets-99.6x40x40mm__fit-e586ab4ff6__print-flat-base.stl
99.6 x 50.1 x 40.0
