thereprocase/peg/docs/gallery/bin-expansion/PB02/part-pb02__v1__pegstr-bin-6-cells-1-pockets-150.4x60x50mm__fit-e586ab4ff6__print-flat-base.stl

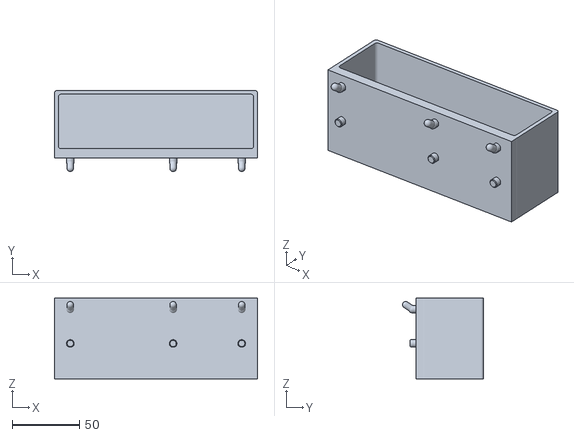
[picture p109: CAD file, 2026-09-16]
docs/gallery/bin-expansion/PB02/part-pb02__v1__pegstr-bin-6-cells-1-pockets-150.4x60x50mm__fit-e586ab4ff6__print-flat-base.stl
150.4 x 60.1 x 60.0
