thereprocase/peg/docs/gallery/bin-expansion/PB03/part-pb03__v1__pegstr-bin-8-cells-1-pockets-201.2x80x50mm__fit-e586ab4ff6__print-flat-base.stl

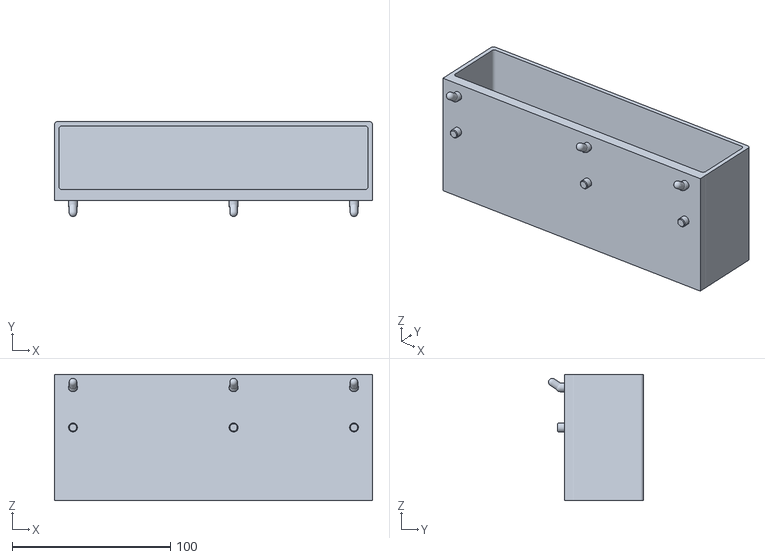
[picture p110: CAD file, 2026-09-16]
docs/gallery/bin-expansion/PB03/part-pb03__v1__pegstr-bin-8-cells-1-pockets-201.2x80x50mm__fit-e586ab4ff6__print-flat-base.stl
201.2 x 60.1 x 80.0
