thereprocase/peg/docs/gallery/bin-expansion/PB04/part-pb04__v1__pegstr-bin-6-cells-3-pockets-150.4x40x45mm__fit-e586ab4ff6__print-flat-base.stl

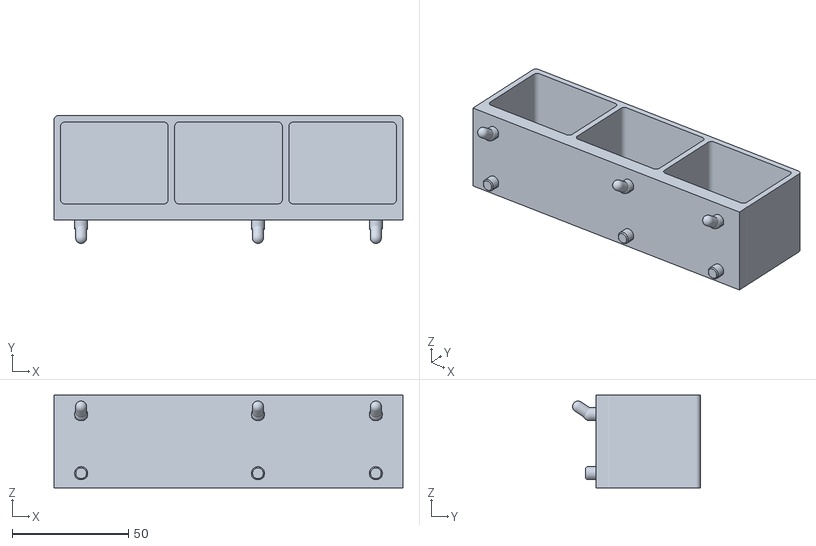
[picture p111: CAD file, 2026-09-16]
docs/gallery/bin-expansion/PB04/part-pb04__v1__pegstr-bin-6-cells-3-pockets-150.4x40x45mm__fit-e586ab4ff6__print-flat-base.stl
150.4 x 55.1 x 40.0
