thereprocase/peg/docs/gallery/canted-hex-keys/part-hx02__v2__right-cheek__fit-pf02c9-hoop5__print.stl

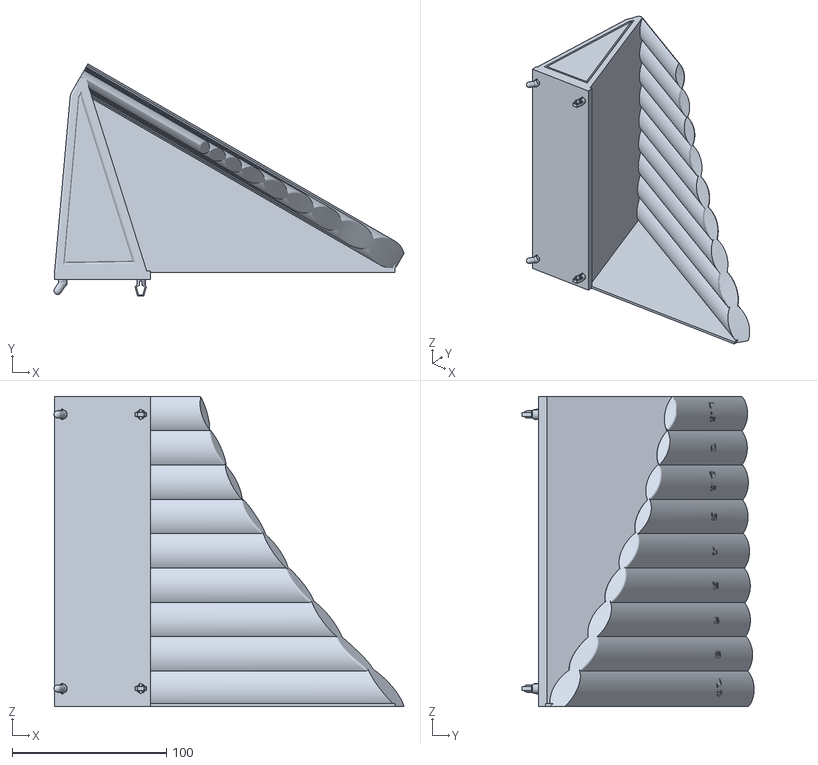
[picture p112: CAD file, 2026-10-07]
docs/gallery/canted-hex-keys/part-hx02__v2__right-cheek__fit-pf02c9-hoop5__print.stl
227.0 x 150.7 x 201.2
