thereprocase/peg/docs/gallery/cascade-funnels/part-cf01__v3__upright__fit-pf02c9-hoop5__print.stl

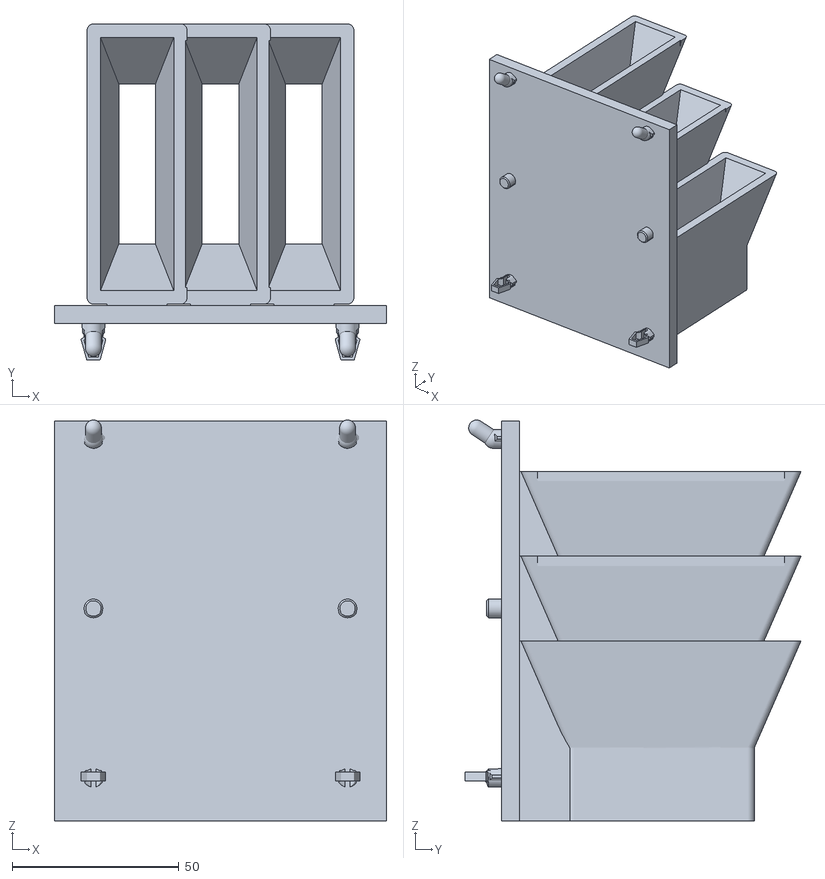
[picture p113: CAD file, 2026-10-06]
docs/gallery/cascade-funnels/part-cf01__v3__upright__fit-pf02c9-hoop5__print.stl
99.6 x 100.8 x 120.2
