thereprocase/peg/docs/gallery/current-pegs/part-hx04__v2__left-cheek__fit-pf02c9-hoop5__installed.stl

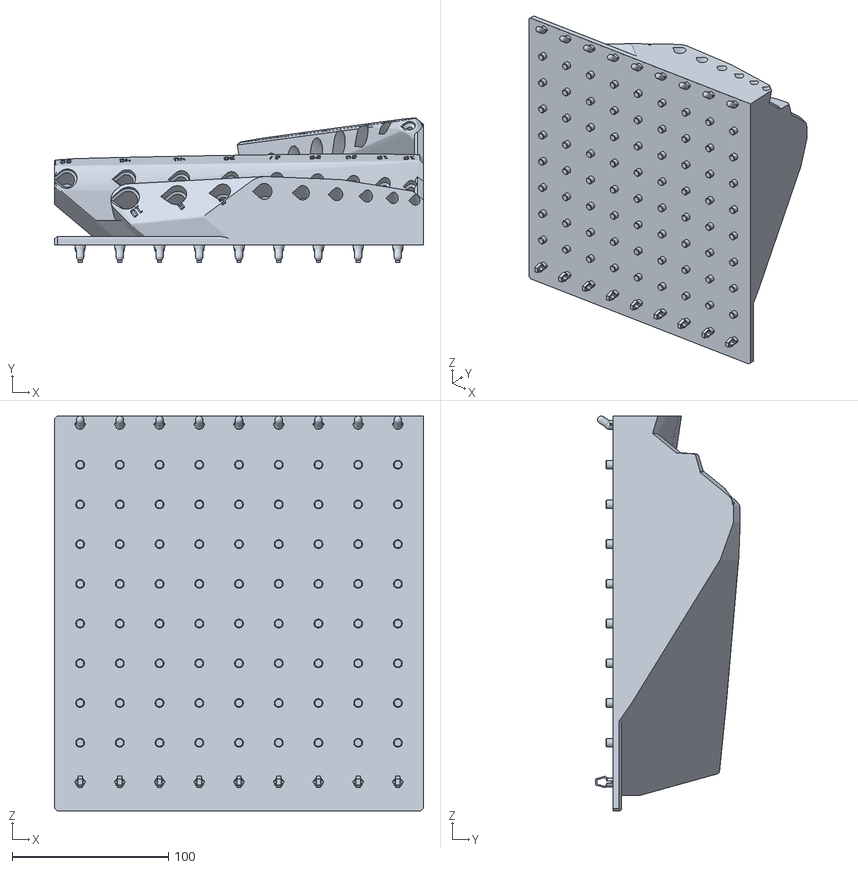
[picture p114: CAD file, 2026-10-08]
docs/gallery/current-pegs/part-hx04__v2__left-cheek__fit-pf02c9-hoop5__installed.stl
236.0 x 92.4 x 252.6
