thereprocase/peg/docs/gallery/downloads/named/part-arrays-p09-16__v-src1cc7daf292__pegstr-array-p09-16-round-seats__print-right-cheek__fit-9c7be3cc78.stl

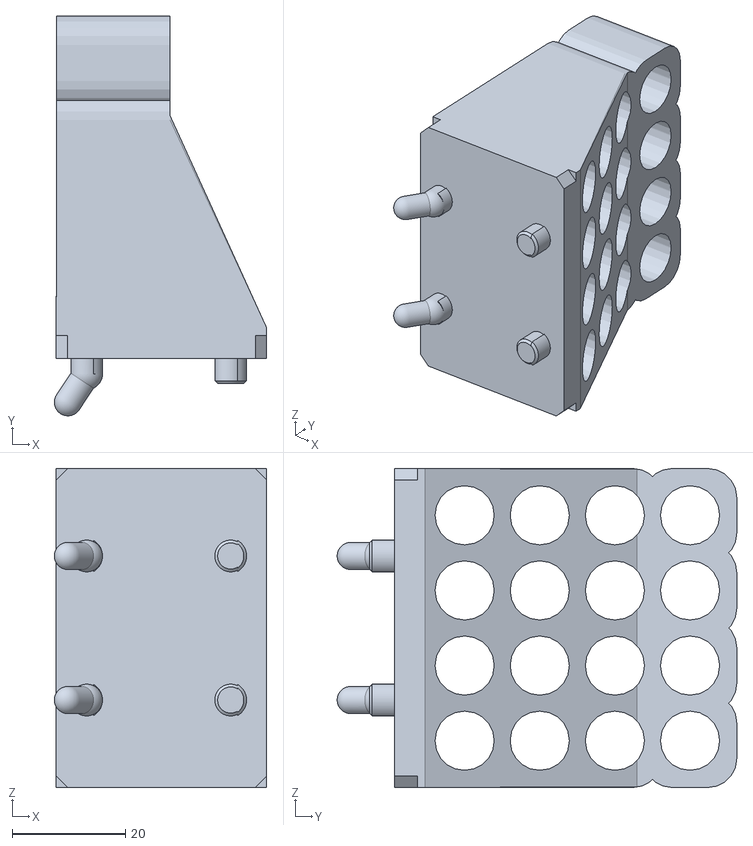
[picture p115: CAD file, 2026-09-16]
docs/gallery/downloads/named/part-arrays-p09-16__v-src1cc7daf292__pegstr-array-p09-16-round-seats__print-right-cheek__fit-9c7be3cc78.stl
37.4 x 70.5 x 56.2
