thereprocase/peg/docs/gallery/key-fan/part-hx04__v2__left-cheek__fit-pf02c9-hoop5__coupon_print.stl

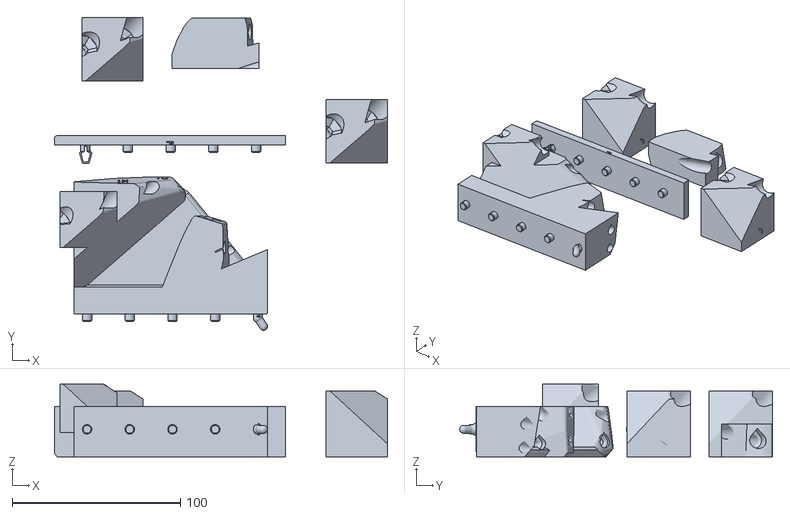
[picture p116: CAD file, 2026-10-08]
docs/gallery/key-fan/part-hx04__v2__left-cheek__fit-pf02c9-hoop5__coupon_print.stl
198.0 x 185.9 x 43.3
