thereprocase/peg/docs/gallery/magnetic-bar/part-mb01-magnetic-shaft-bar-f__v1__2-seats-4-cells__holder-installed__fit-e586ab4ff6.stl

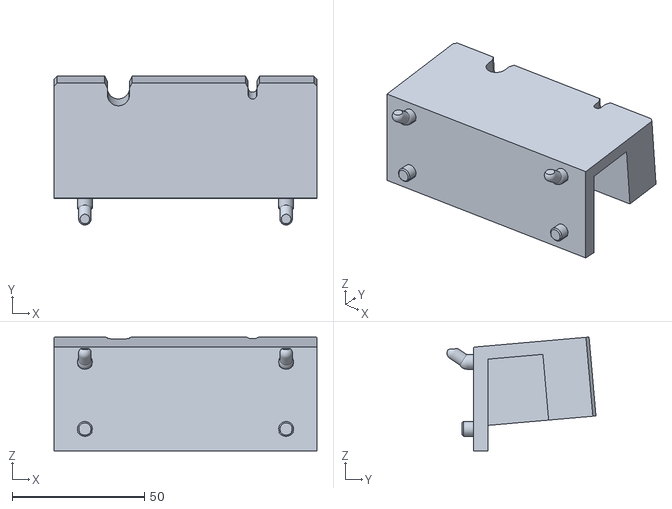
[picture p117: CAD file, 2026-09-16]
docs/gallery/magnetic-bar/part-mb01-magnetic-shaft-bar-f__v1__2-seats-4-cells__holder-installed__fit-e586ab4ff6.stl
99.6 x 56.4 x 43.1
