thereprocase/peg/docs/gallery/pegstr/P02/receiver-host.stl

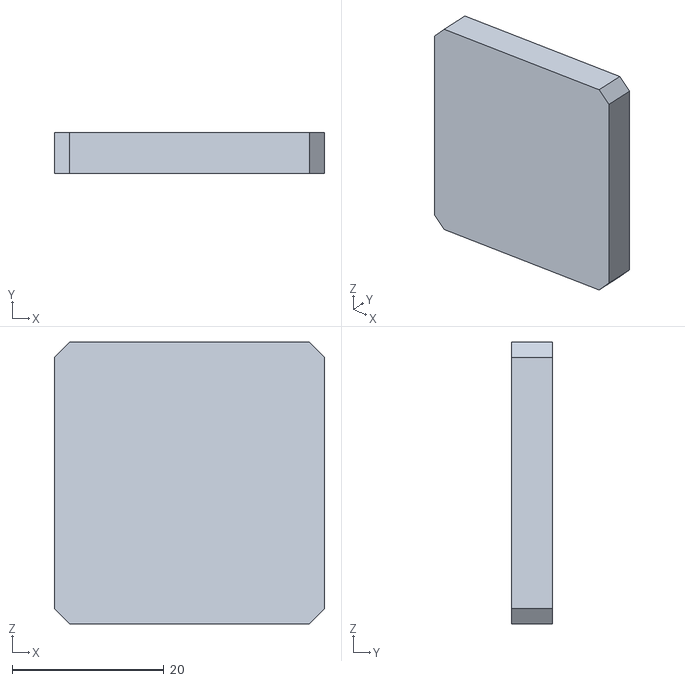
[picture p118: CAD file, 2026-09-16]
docs/gallery/pegstr/P02/receiver-host.stl
35.6 x 5.40 x 37.1
