thereprocase/peg/docs/gallery/pegstr/P05/original.stl

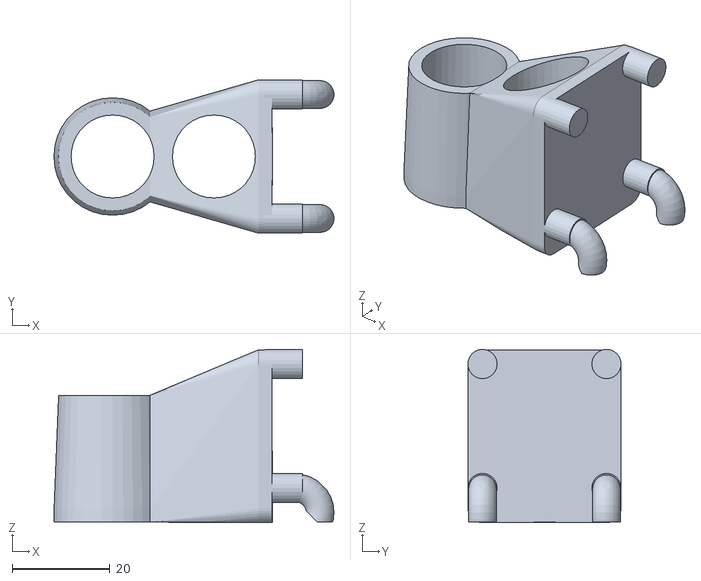
[picture p119: CAD file, 2026-09-16]
docs/gallery/pegstr/P05/original.stl
57.4 x 31.4 x 35.5
