thereprocase/peg/docs/gallery/pegstr/P06/raw-union.stl

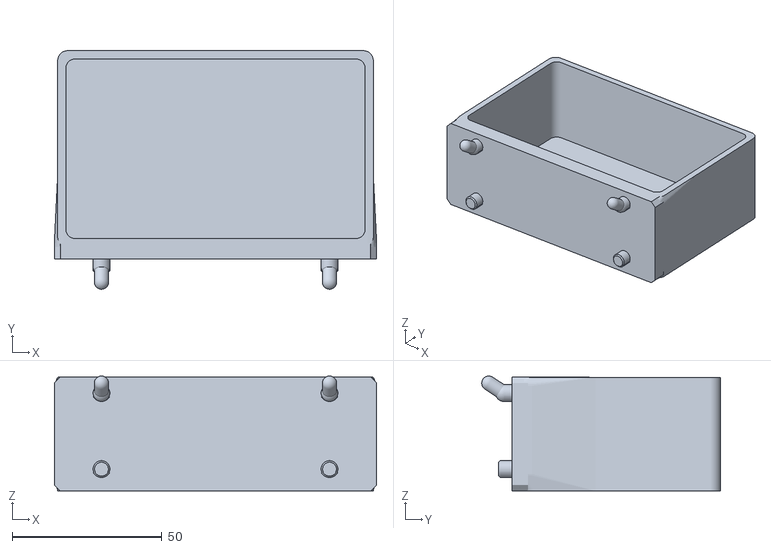
[picture p120: CAD file, 2026-09-16]
docs/gallery/pegstr/P06/raw-union.stl
107.6 x 79.7 x 38.4
