thereprocase/peg/docs/gallery/pegstr/P10/raw-union.stl

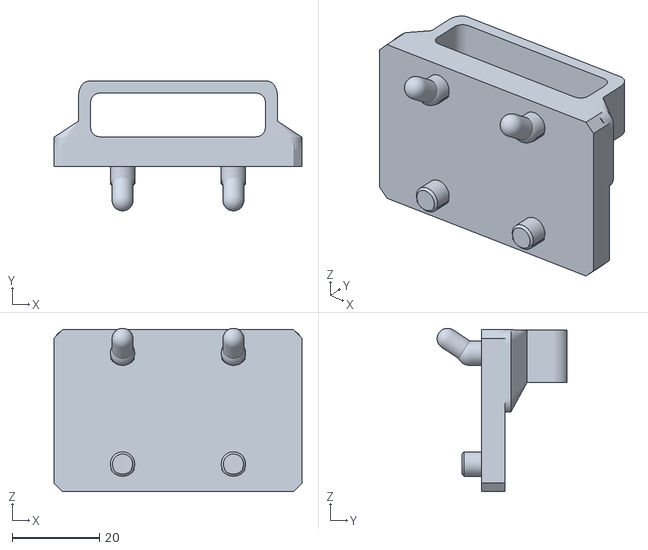
[picture p121: CAD file, 2026-09-16]
docs/gallery/pegstr/P10/raw-union.stl
56.8 x 29.7 x 37.4
