thereprocase/peg/docs/gallery/pegstr/P11/original.stl

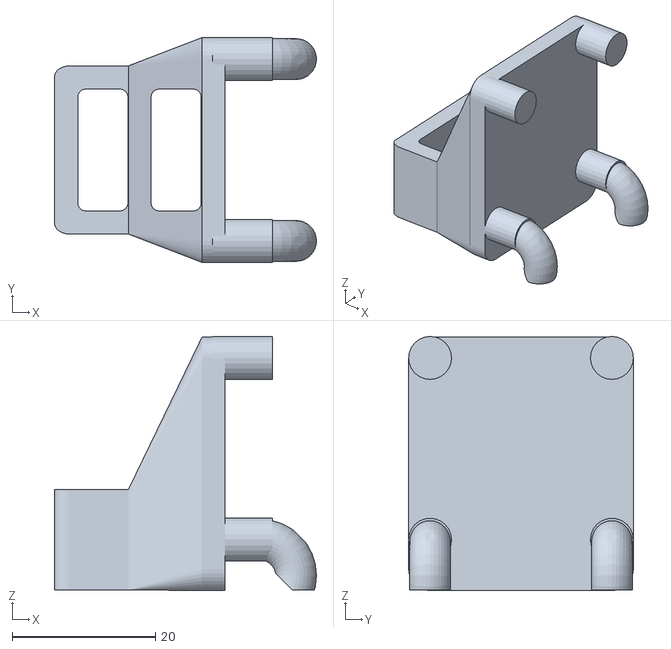
[picture p122: CAD file, 2026-09-16]
docs/gallery/pegstr/P11/original.stl
36.6 x 31.4 x 35.5
