thereprocase/peg/docs/gallery/shaft-holders/part-mh01-magnetic-shaft-holder-jeweler-4mm-round__v1__6-seats-4-cells__plug-print-broad-face-quantity-6__fit-e586ab4ff6.stl

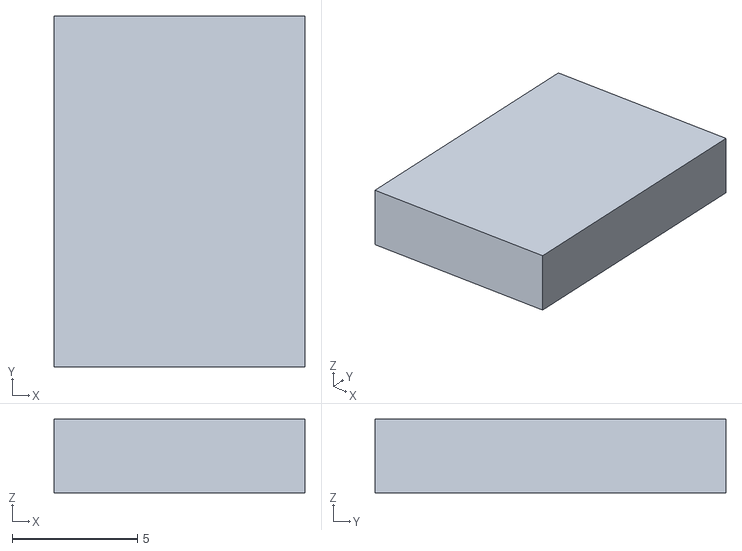
[picture p123: CAD file, 2026-09-17]
docs/gallery/shaft-holders/part-mh01-magnetic-shaft-holder-jeweler-4mm-round__v1__6-seats-4-cells__plug-print-broad-face-quantity-6__fit-e586ab4ff6.stl
10.0 x 14.0 x 2.95
