thereprocase/peg/docs/gallery/shaft-sampler/recoverable/combs/part-ms01-retaining-comb__v1__A-H__installed.stl

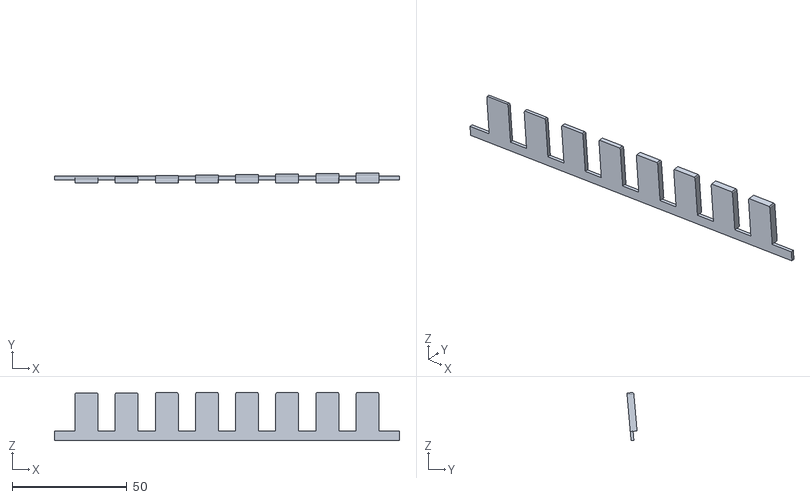
[picture p124: CAD file, 2026-09-16]
docs/gallery/shaft-sampler/recoverable/combs/part-ms01-retaining-comb__v1__A-H__installed.stl
150.4 x 4.46 x 21.0
