thereprocase/peg/docs/gallery/shaft-sampler/recoverable/part-ms01-shaft-fit-sampler-20x10x3-recoverable__v3__I-P__installed__fit-e586ab4ff6.stl

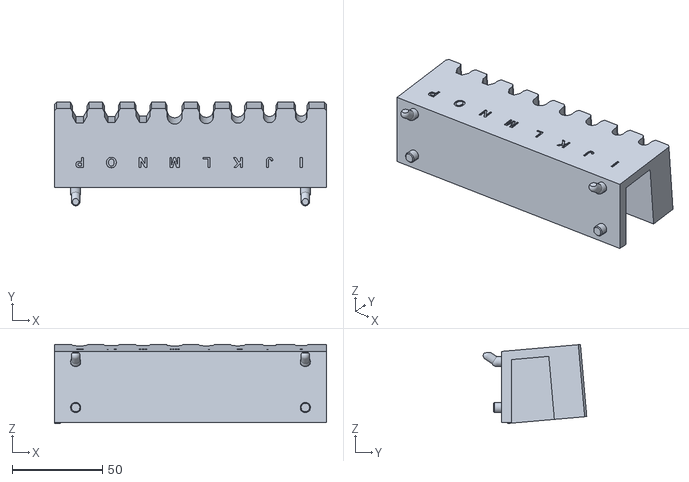
[picture p125: CAD file, 2026-09-16]
docs/gallery/shaft-sampler/recoverable/part-ms01-shaft-fit-sampler-20x10x3-recoverable__v3__I-P__installed__fit-e586ab4ff6.stl
150.4 x 57.3 x 43.7
