thereprocase/peg/docs/gallery/solder-modules/barrels/print-pose.stl

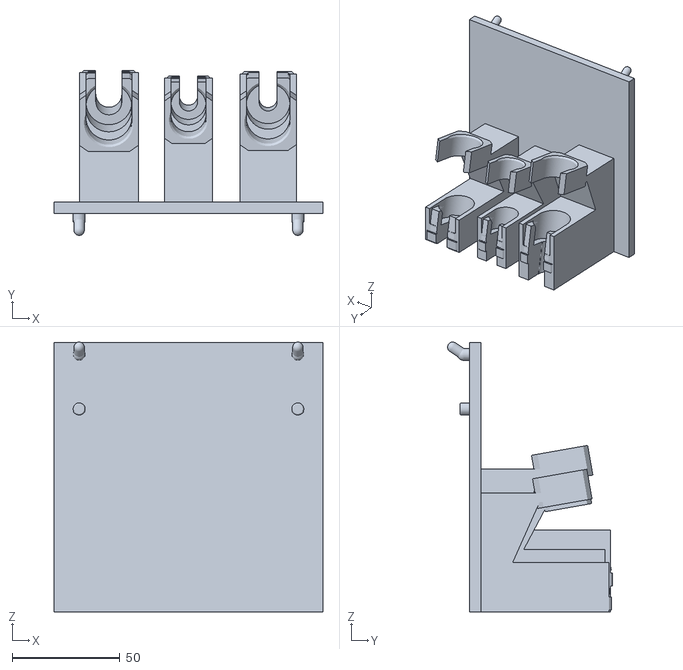
[picture p126: CAD file, 2026-09-16]
docs/gallery/solder-modules/barrels/print-pose.stl
125.0 x 76.6 x 125.4
