thereprocase/peg/docs/gallery/solder-modules/braid/print-pose.stl

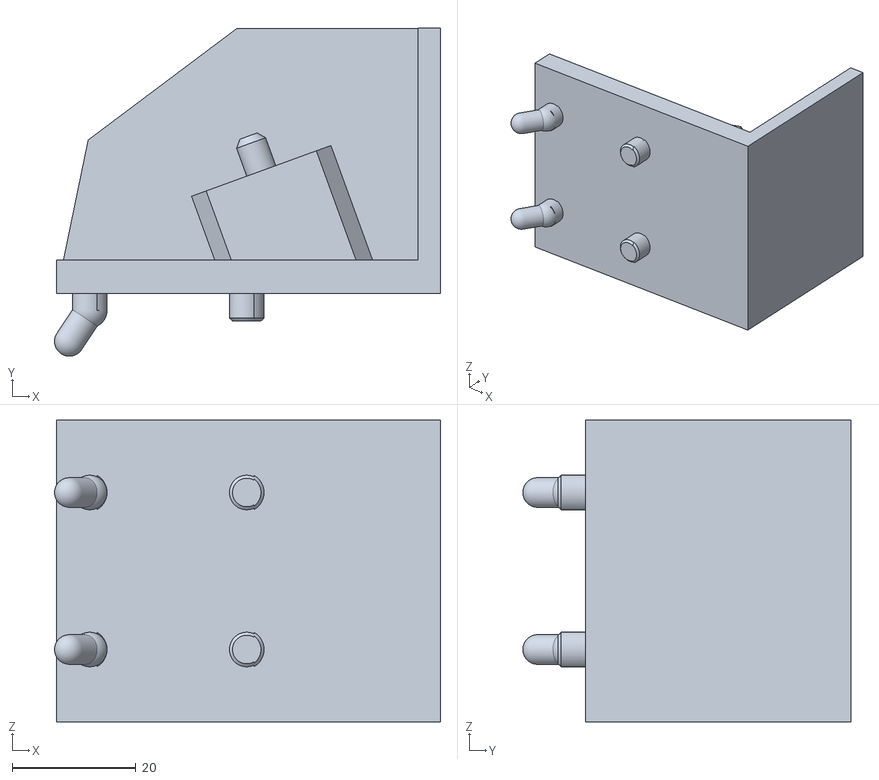
[picture p127: CAD file, 2026-09-16]
docs/gallery/solder-modules/braid/print-pose.stl
62.4 x 53.1 x 48.8
