thereprocase/peg/docs/gallery/solder-modules/drip-tray/holder.stl

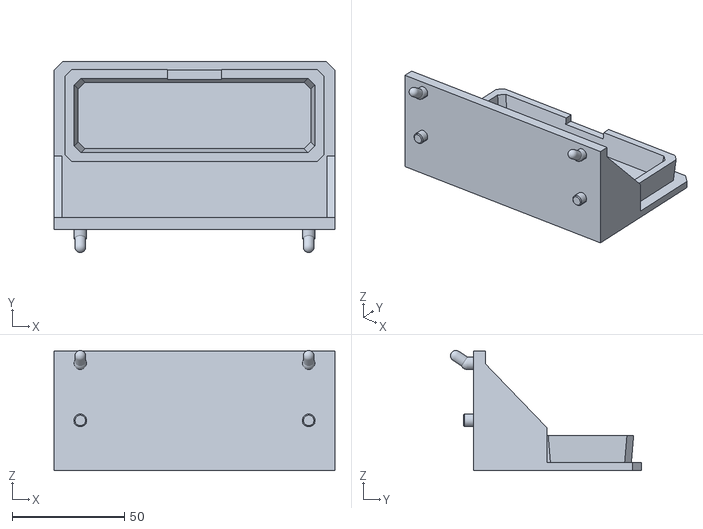
[picture p128: CAD file, 2026-09-16]
docs/gallery/solder-modules/drip-tray/holder.stl
125.0 x 85.0 x 53.4
