thereprocase/peg/docs/gallery/solder-modules/reel-thick/print-pose.stl

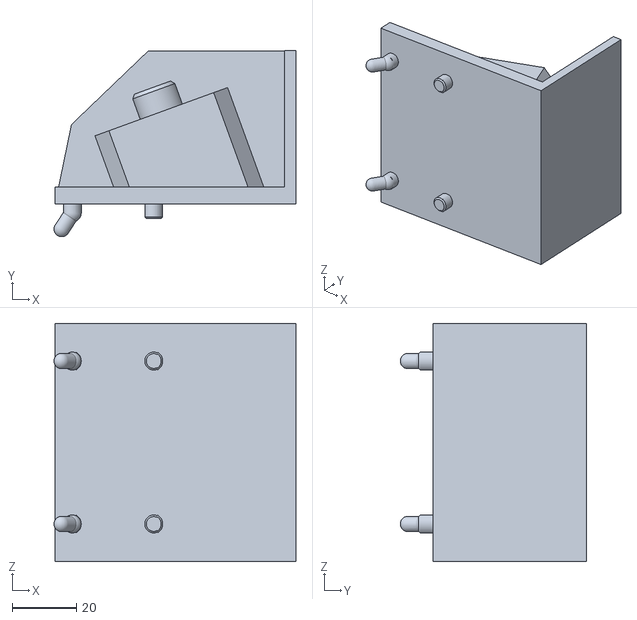
[picture p129: CAD file, 2026-09-16]
docs/gallery/solder-modules/reel-thick/print-pose.stl
75.4 x 58.1 x 74.2
