thereprocase/peg/docs/gallery/solder-modules/snips-pliers/right-cheek-print-pose.stl

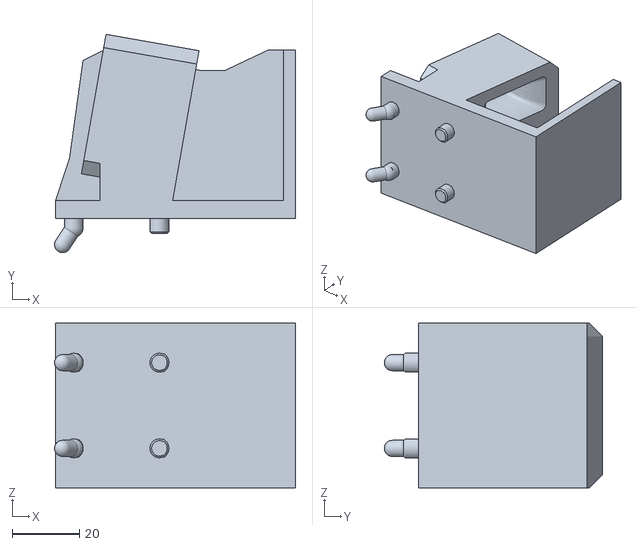
[picture p130: CAD file, 2026-09-16]
docs/gallery/solder-modules/snips-pliers/right-cheek-print-pose.stl
71.4 x 64.7 x 48.8
