thereprocase/peg/docs/gallery/solder-modules/tweezers/print-pose.stl

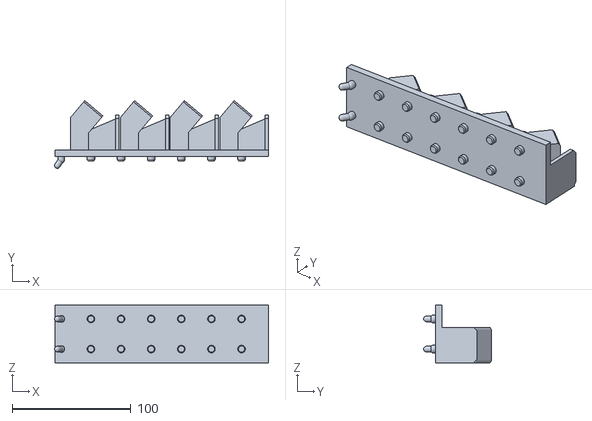
[picture p131: CAD file, 2026-09-16]
docs/gallery/solder-modules/tweezers/print-pose.stl
180.4 x 57.2 x 48.8
