thereprocase/peg/docs/gallery/tweezers/part-solder-modules-tweezers__v10__compact-right-cheek__fit-9328ccc5d4__print-right-cheek.stl

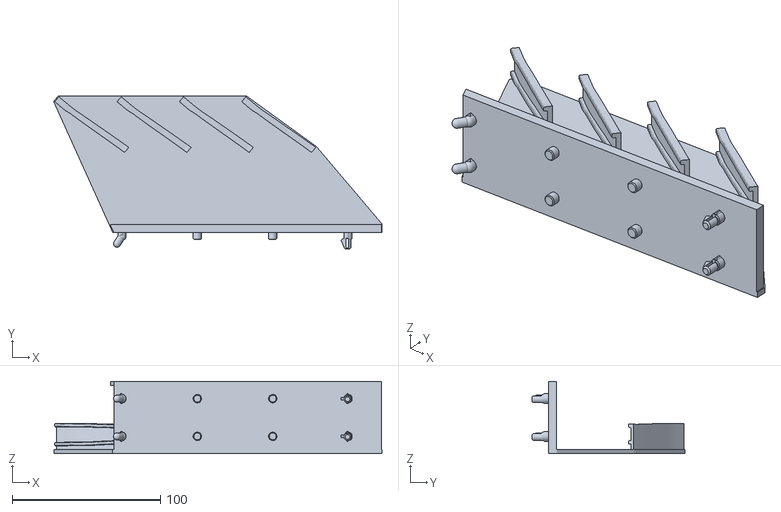
[picture p132: CAD file, 2026-10-01]
docs/gallery/tweezers/part-solder-modules-tweezers__v10__compact-right-cheek__fit-9328ccc5d4__print-right-cheek.stl
221.0 x 103.0 x 48.8
