thereprocase/peg/Round_Print_Options.3mf

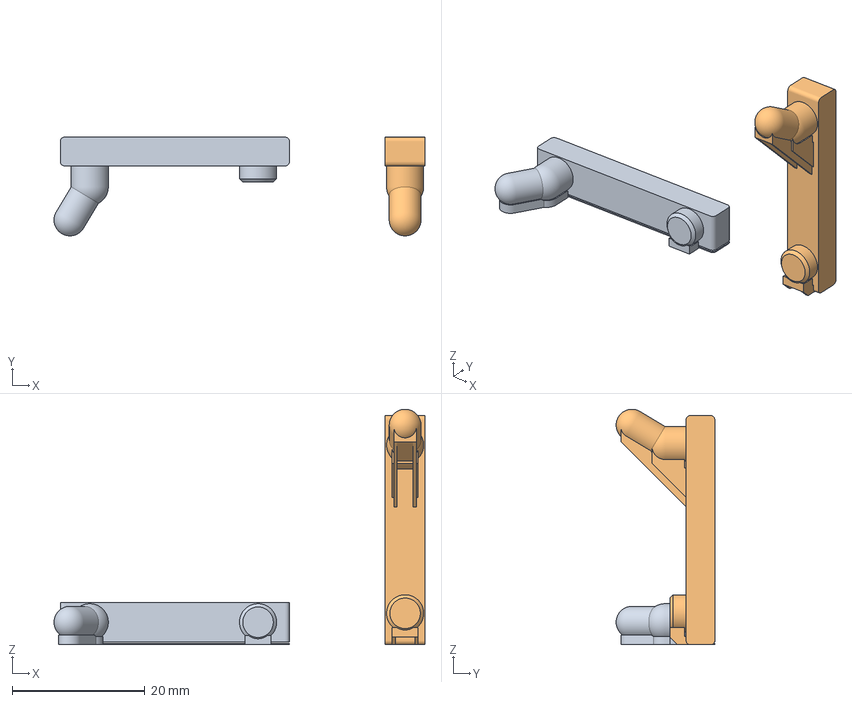
[picture p133: CAD file, 2026-09-08]
Round_Print_Options.3mf
56.0 x 14.9 x 35.5 mm
SIDE_remove_cradles
UPRIGHT_cut_webs_remove_cradles
