thereprocase/peg/bench/reviews/tee-fit-v2-flats-c10/T5_F_C10__installed.step

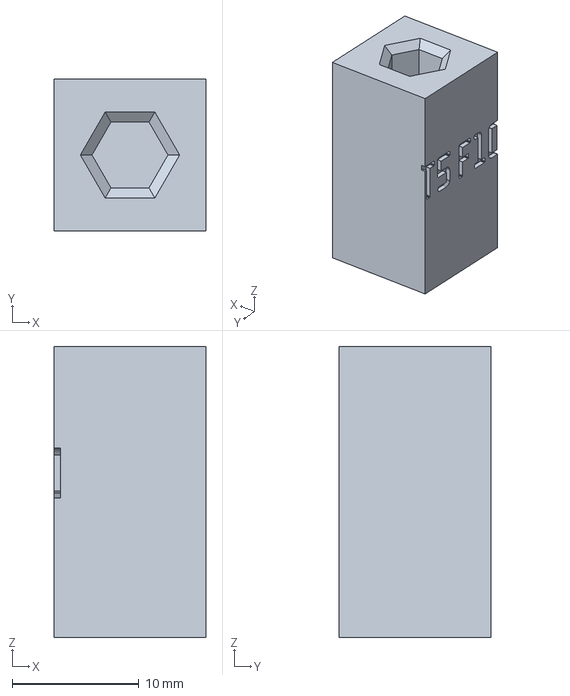
[picture p134: CAD file, 2026-10-09]
bench/reviews/tee-fit-v2-flats-c10/T5_F_C10__installed.step
12.0 x 12.0 x 23.0 mm
