thereprocase/peg/bench/reviews/tee-fit-v4-guide40/HX05-fit-v4__left-end__print.step

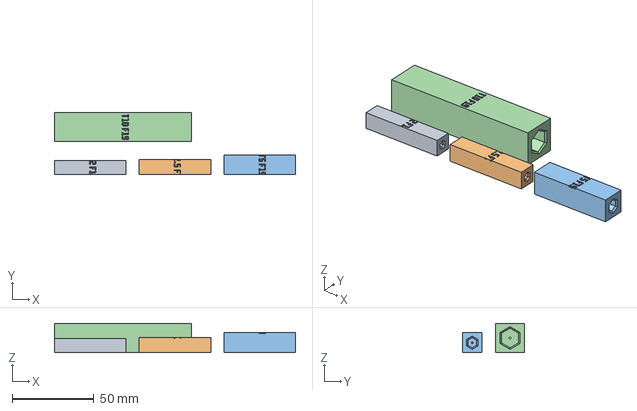
[picture p135: CAD file, 2026-10-09]
bench/reviews/tee-fit-v4-guide40/HX05-fit-v4__left-end__print.step
147.4 x 38.2 x 18.0 mm
