thereprocase/peg/bench/reviews/tee-fit-v5-spectra/HX05-fit-v5-3mm__rack-angle__print.step

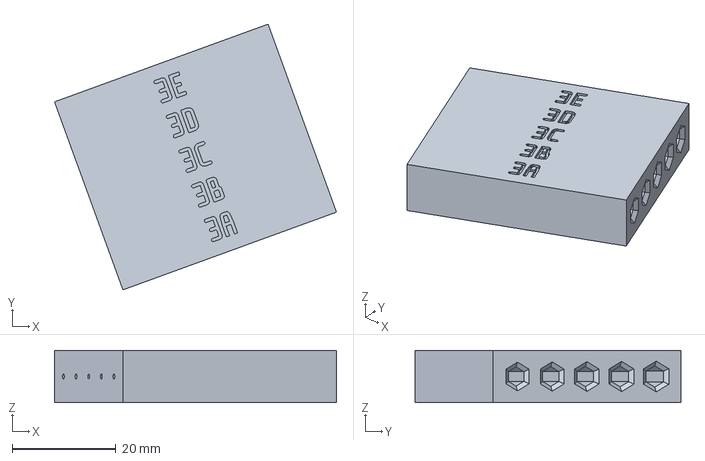
[picture p136: CAD file, 2026-10-10]
bench/reviews/tee-fit-v5-spectra/HX05-fit-v5-3mm__rack-angle__print.step
54.3 x 51.2 x 10.1 mm
