thereprocase/peg/bench/reviews/tee-fit-v6-fan/HX05-fit-v6-3mm__fan-angle__print.step

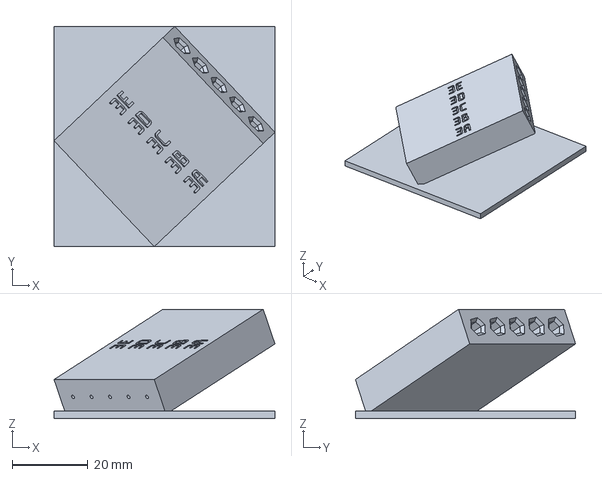
[picture p137: CAD file, 2026-10-10]
bench/reviews/tee-fit-v6-fan/HX05-fit-v6-3mm__fan-angle__print.step
58.4 x 58.2 x 28.9 mm
