thereprocase/peg/cad/round_stock_4p19_design_reference.stl

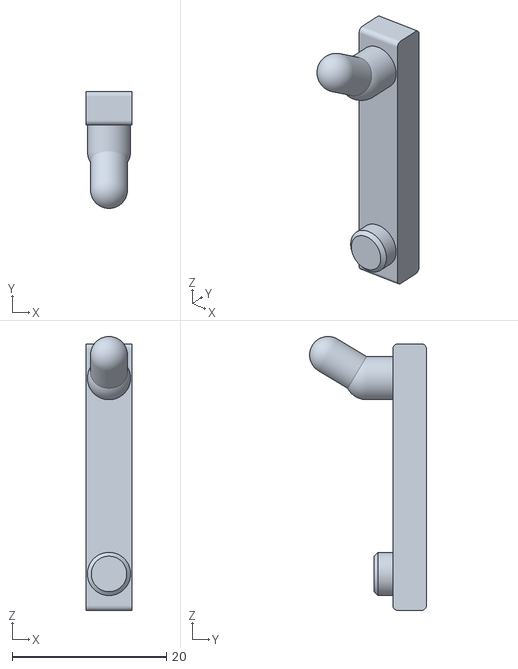
[picture p138: CAD file, 2026-09-08]
cad/round_stock_4p19_design_reference.stl
6.00 x 15.2 x 35.5
