thereprocase/peg/docs/gallery/arrays/P01-24/receiver.stl

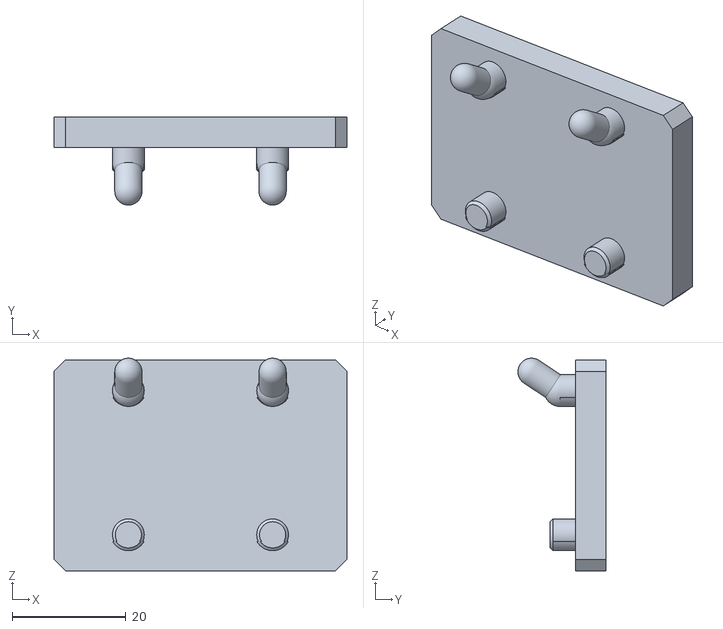
[picture p139: CAD file, 2026-09-16]
docs/gallery/arrays/P01-24/receiver.stl
51.6 x 15.5 x 37.4
