thereprocase/peg/docs/gallery/arrays/P01-48/print-overhangs.stl

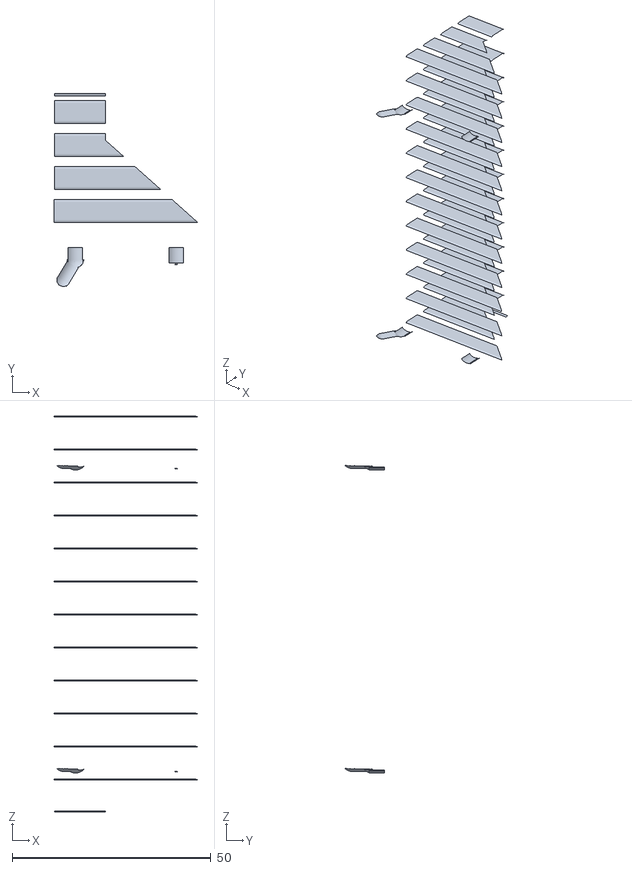
[picture p140: CAD file, 2026-09-16]
docs/gallery/arrays/P01-48/print-overhangs.stl
36.1 x 48.6 x 99.6
