thereprocase/peg/docs/gallery/arrays/P09-16/receiver.stl

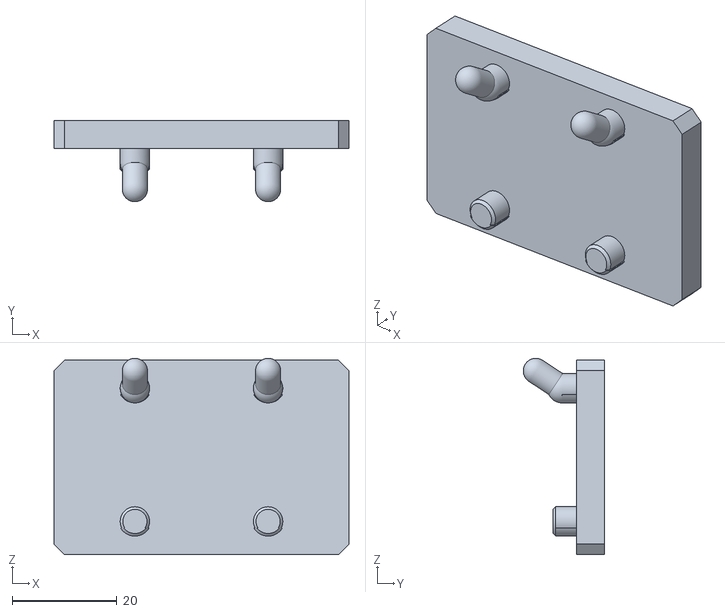
[picture p141: CAD file, 2026-09-16]
docs/gallery/arrays/P09-16/receiver.stl
56.2 x 15.5 x 37.4
