thereprocase/peg/docs/gallery/arrays/P09-48/model.stl

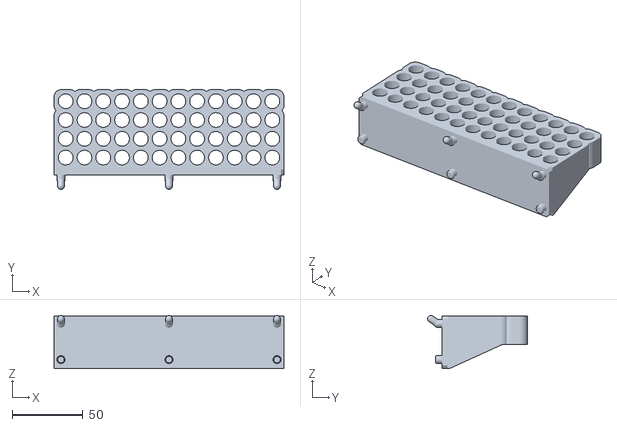
[picture p142: CAD file, 2026-09-16]
docs/gallery/arrays/P09-48/model.stl
162.2 x 70.5 x 37.4
