thereprocase/peg/docs/gallery/arrays/P09-72/receiver.stl

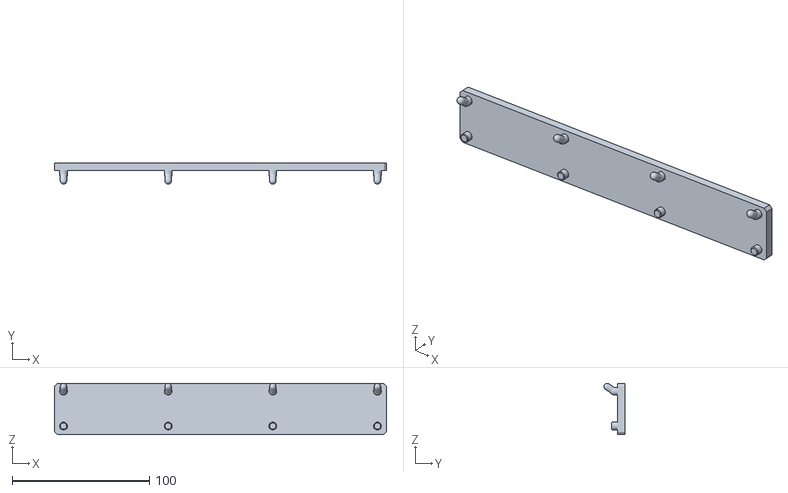
[picture p143: CAD file, 2026-09-16]
docs/gallery/arrays/P09-72/receiver.stl
241.8 x 15.5 x 37.4
