thereprocase/peg/docs/gallery/downloads/named/part-pegstr-p08__v2__pegstr-p08-flashlight-ring__reference-original.stl

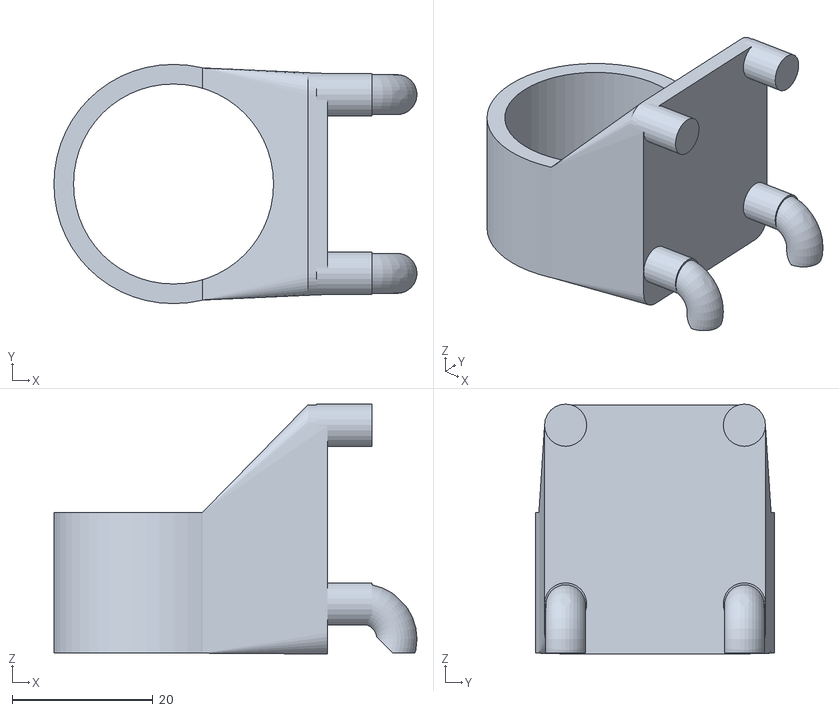
[picture p144: CAD file, 2026-09-16]
docs/gallery/downloads/named/part-pegstr-p08__v2__pegstr-p08-flashlight-ring__reference-original.stl
51.6 x 34.0 x 35.5
