thereprocase/peg/docs/gallery/key-fan/fit-v6/HX05-fit-v6-7mm__fan-angle__print.stl

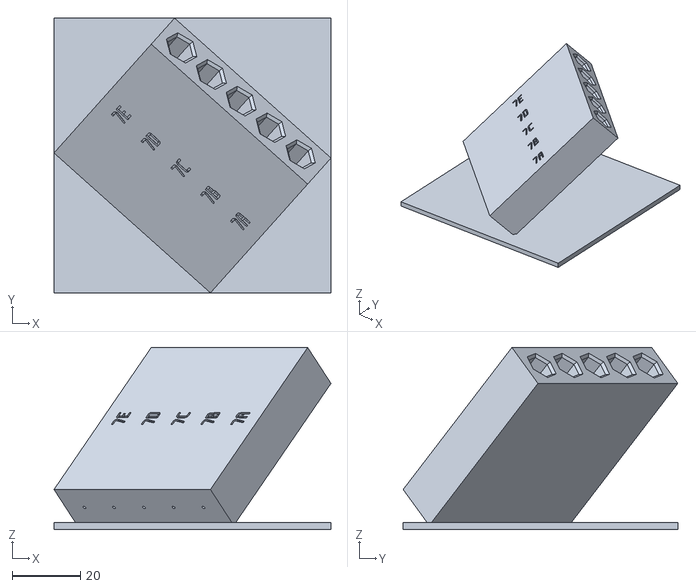
[picture p145: CAD file, 2026-10-10]
docs/gallery/key-fan/fit-v6/HX05-fit-v6-7mm__fan-angle__print.stl
81.4 x 80.7 x 53.5
