thereprocase/peg/docs/gallery/magnetic-bar/part-mb01-magnetic-shaft-bar-f__v1__2-seats-4-cells__plug-print-broad-face-quantity-2__fit-e586ab4ff6.stl

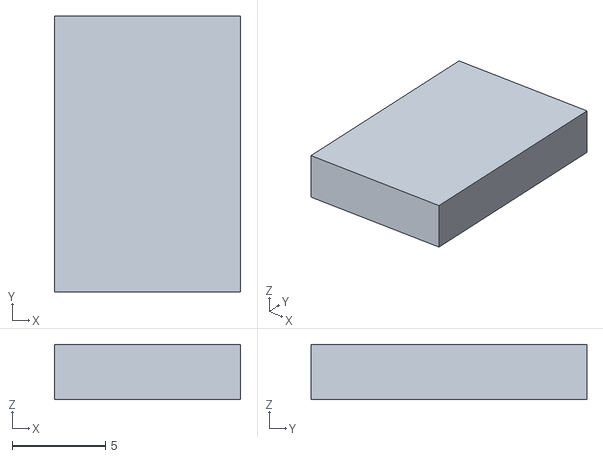
[picture p146: CAD file, 2026-09-16]
docs/gallery/magnetic-bar/part-mb01-magnetic-shaft-bar-f__v1__2-seats-4-cells__plug-print-broad-face-quantity-2__fit-e586ab4ff6.stl
10.0 x 14.8 x 2.95
