thereprocase/peg/docs/gallery/pegstr/P02/original.stl

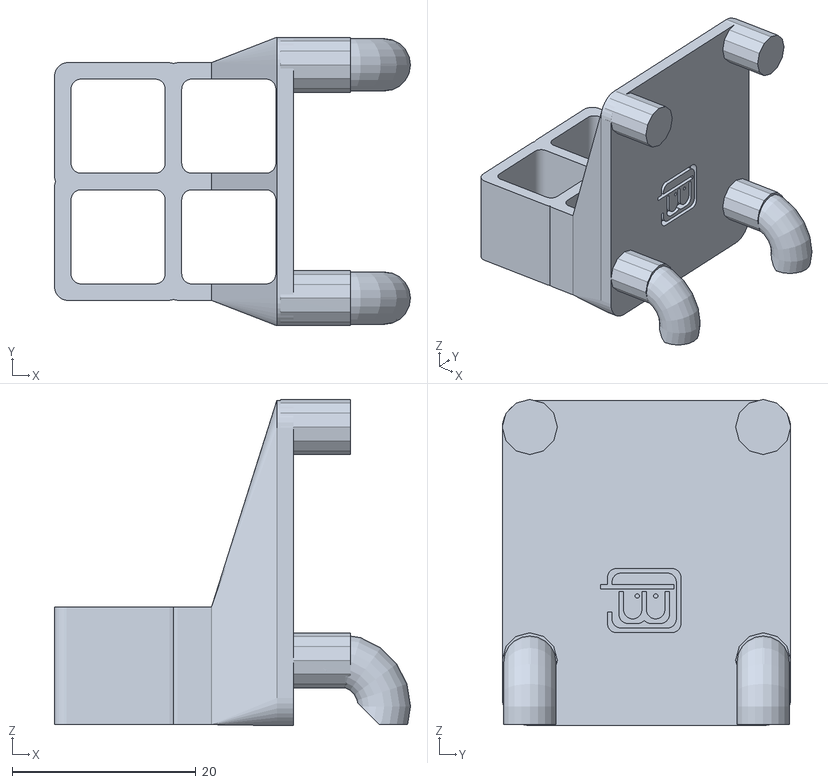
[picture p147: CAD file, 2026-09-16]
docs/gallery/pegstr/P02/original.stl
38.8 x 31.4 x 35.5
