thereprocase/peg/docs/gallery/pegstr/P06/receiver.stl

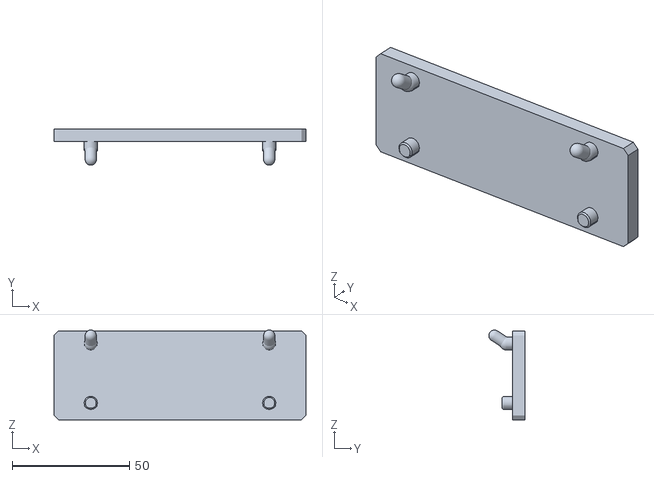
[picture p148: CAD file, 2026-09-16]
docs/gallery/pegstr/P06/receiver.stl
107.6 x 15.5 x 38.4
