thereprocase/peg/docs/gallery/pegstr/P07/raw-union.stl

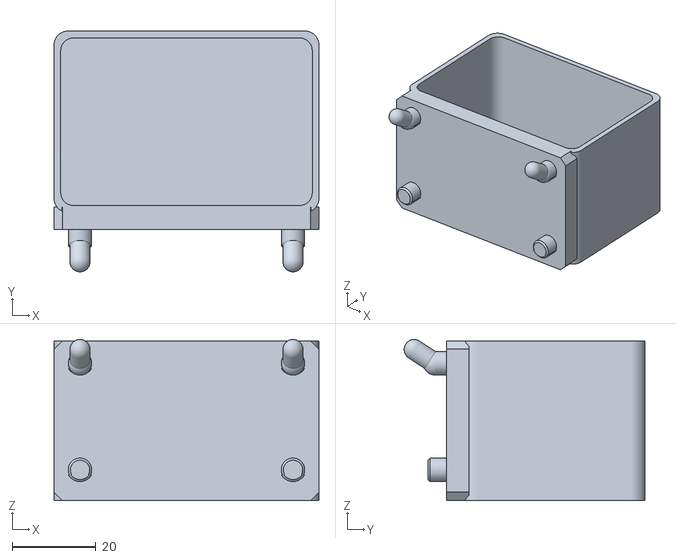
[picture p149: CAD file, 2026-09-16]
docs/gallery/pegstr/P07/raw-union.stl
63.2 x 57.4 x 38.4
