thereprocase/peg/docs/gallery/pegstr/P09/raw-union.stl

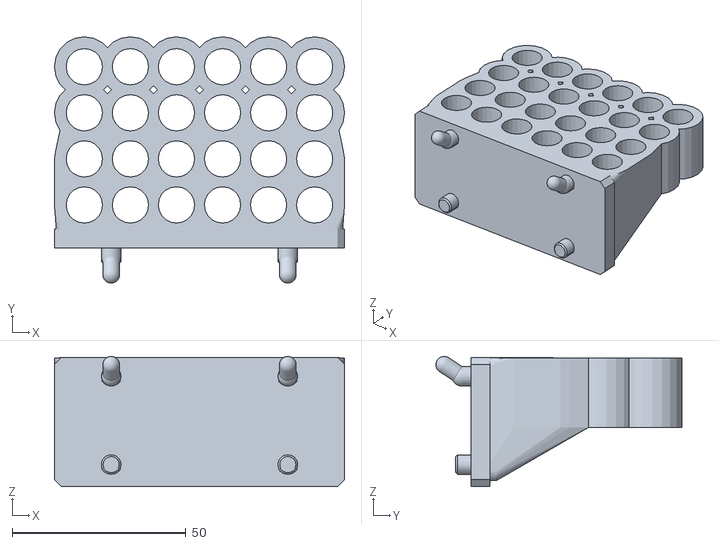
[picture p150: CAD file, 2026-09-16]
docs/gallery/pegstr/P09/raw-union.stl
83.4 x 70.8 x 37.4
