thereprocase/peg/docs/gallery/pegstr/P11/receiver.stl

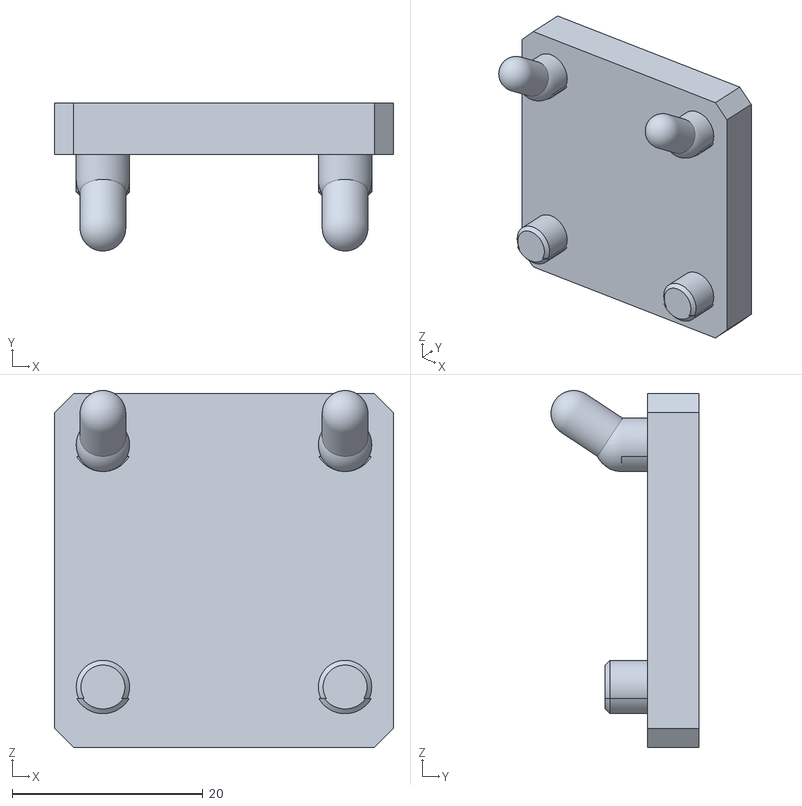
[picture p151: CAD file, 2026-09-16]
docs/gallery/pegstr/P11/receiver.stl
35.6 x 15.5 x 37.4
