thereprocase/peg/docs/gallery/shaft-holders/part-mh02-magnetic-shaft-holder-6mm-round__v1__4-seats-7-cells__installed__fit-e586ab4ff6.stl

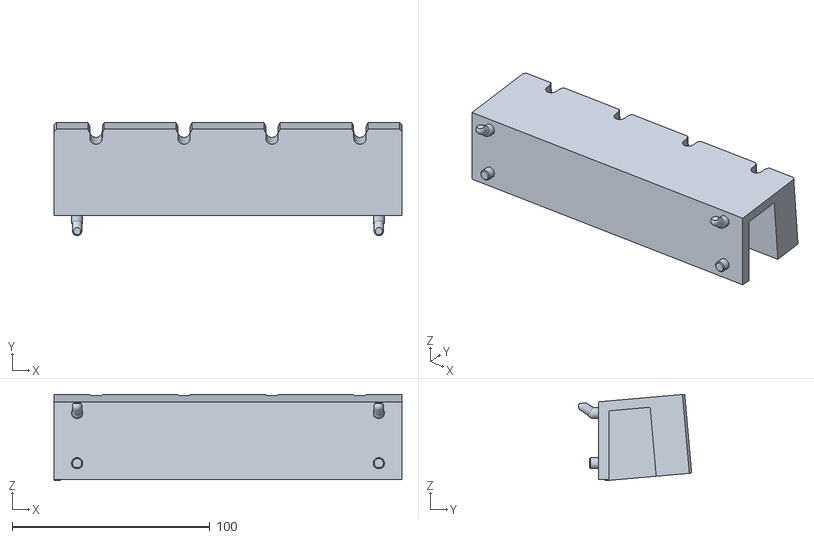
[picture p152: CAD file, 2026-09-17]
docs/gallery/shaft-holders/part-mh02-magnetic-shaft-holder-6mm-round__v1__4-seats-7-cells__installed__fit-e586ab4ff6.stl
175.8 x 57.3 x 43.7
