thereprocase/peg/docs/gallery/shaft-sampler/part-ms01-shaft-fit-sampler-20x10x3__v2__I-P__print-flat-top__fit-e586ab4ff6.stl

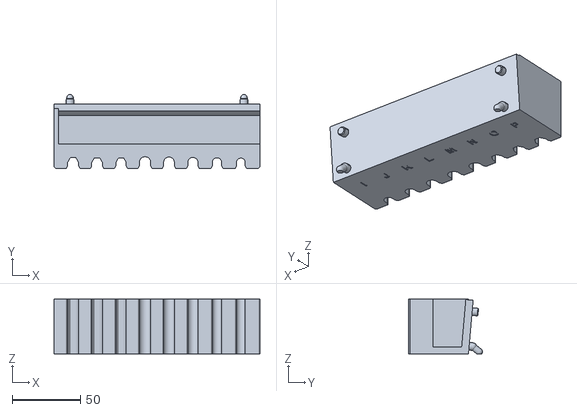
[picture p153: CAD file, 2026-09-16]
docs/gallery/shaft-sampler/part-ms01-shaft-fit-sampler-20x10x3__v2__I-P__print-flat-top__fit-e586ab4ff6.stl
150.4 x 54.1 x 40.0
