thereprocase/peg/docs/gallery/shaft-sampler/recoverable/combs/part-ms01-retaining-comb__v1__I-P__installed.stl

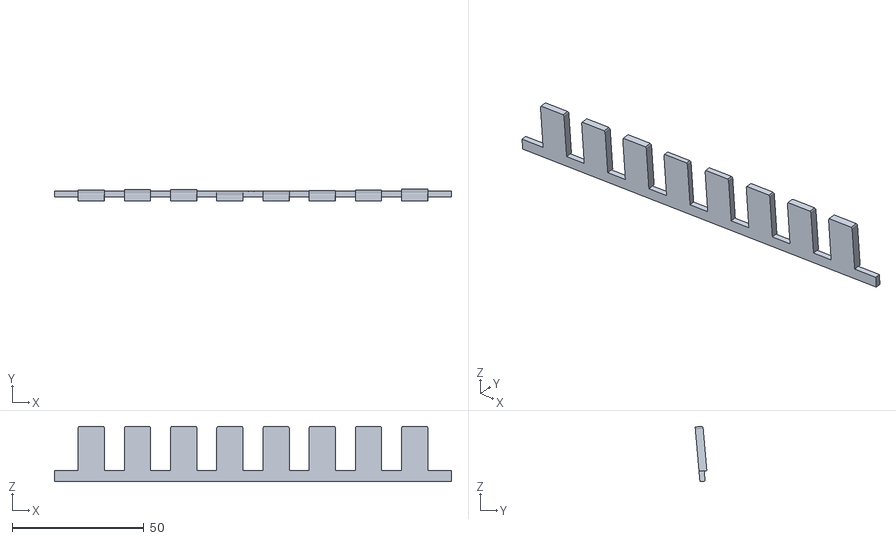
[picture p154: CAD file, 2026-09-16]
docs/gallery/shaft-sampler/recoverable/combs/part-ms01-retaining-comb__v1__I-P__installed.stl
150.4 x 4.46 x 21.0
