thereprocase/peg/docs/gallery/shaft-sampler/recoverable/part-ms01-shaft-fit-sampler-20x10x3-recoverable__v3__loose-spacer-print-broad-face-quantity-16__fit-e586ab4ff6.stl

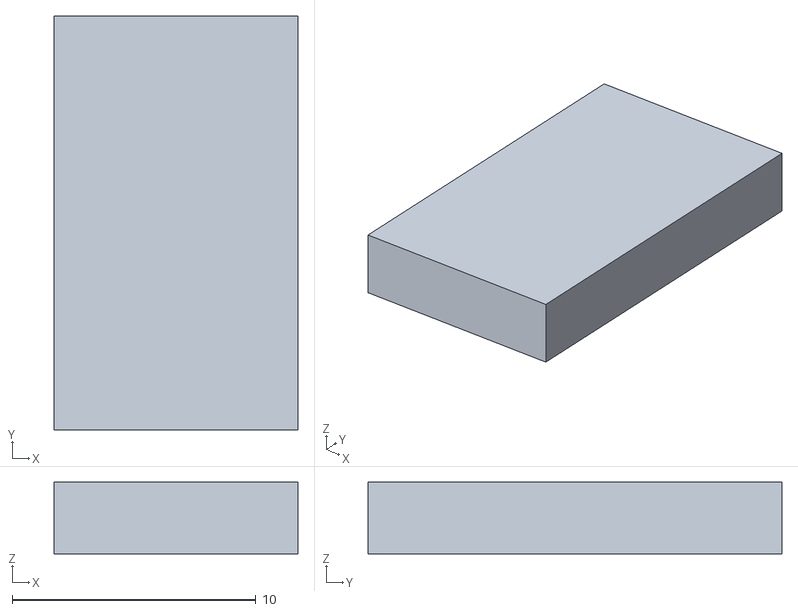
[picture p155: CAD file, 2026-09-16]
docs/gallery/shaft-sampler/recoverable/part-ms01-shaft-fit-sampler-20x10x3-recoverable__v3__loose-spacer-print-broad-face-quantity-16__fit-e586ab4ff6.stl
10.0 x 17.0 x 2.95
