thereprocase/peg/docs/gallery/solder-modules/drip-tray/liner-vase-source.stl

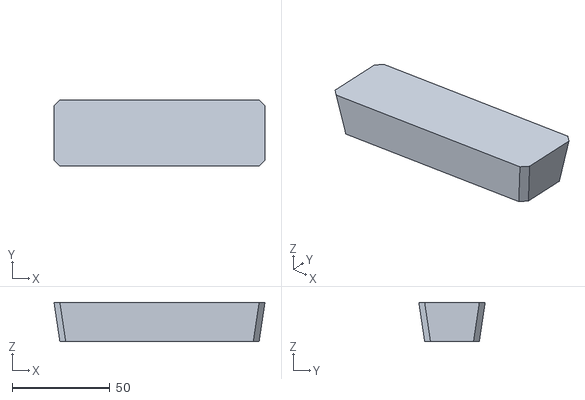
[picture p156: CAD file, 2026-09-16]
docs/gallery/solder-modules/drip-tray/liner-vase-source.stl
108.0 x 34.0 x 20.0
