thereprocase/peg/docs/gallery/tweezers/part-solder-modules-tweezers__v10__single-throat__print-right-cheek.stl

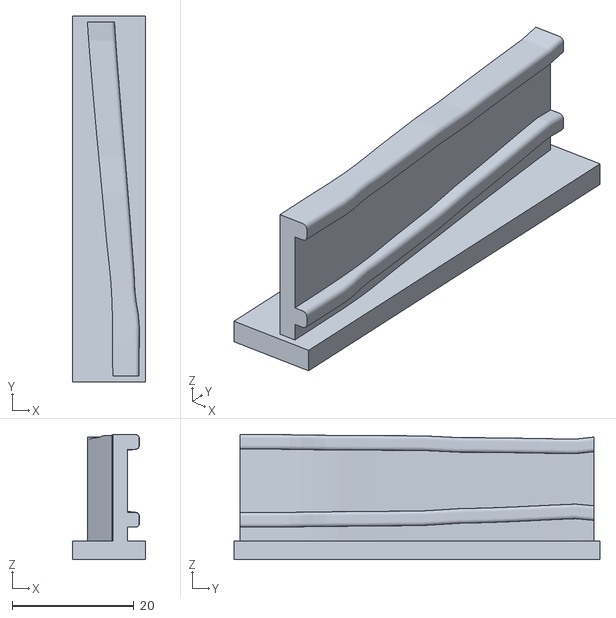
[picture p157: CAD file, 2026-10-01]
docs/gallery/tweezers/part-solder-modules-tweezers__v10__single-throat__print-right-cheek.stl
12.0 x 60.0 x 20.5
