thereprocase/peg/Pegboard_Print_Options.3mf

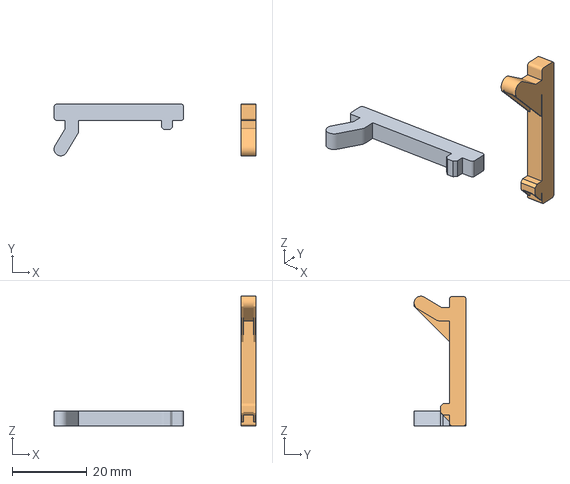
[picture p158: CAD file, 2026-09-08]
Pegboard_Print_Options.3mf
54.0 x 13.8 x 34.7 mm
FLAT_support_free
UPRIGHT_cut_four_webs
