thereprocase/peg/bench/reviews/tee-fit-v2-flats-c10/HX05-fit-v2.FCStd

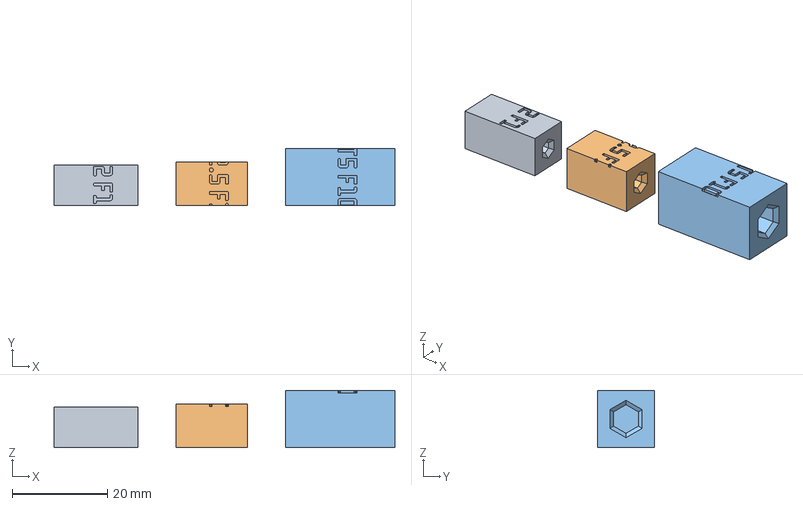
[picture p159: CAD file, 2026-10-09]
bench/reviews/tee-fit-v2-flats-c10/HX05-fit-v2.FCStd
71.6 x 12.0 x 12.0 mm
L2 F10
T2.5 F10
T5 F10
