thereprocase/peg/bench/reviews/tee-fit-v4-guide40/T10_F_C19__installed.step

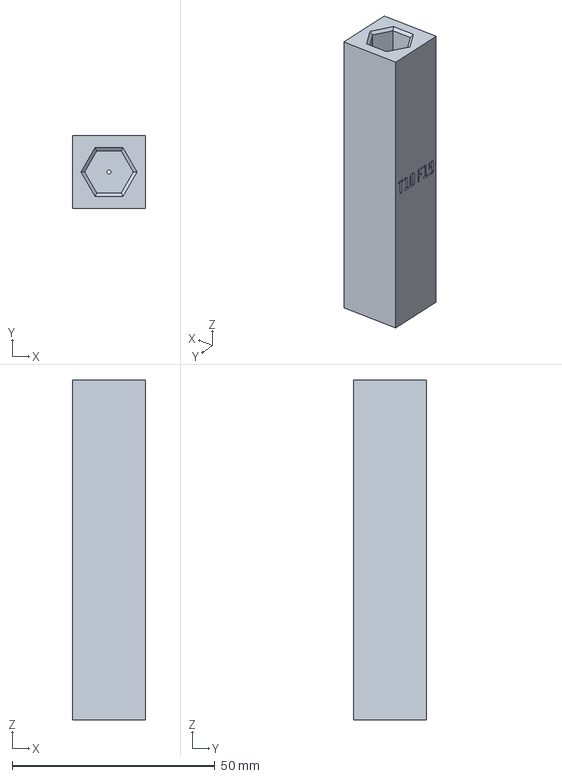
[picture p160: CAD file, 2026-10-09]
bench/reviews/tee-fit-v4-guide40/T10_F_C19__installed.step
18.0 x 18.0 x 83.8 mm
