thereprocase/peg/bench/reviews/tee-fit-v5-spectra/HX05-fit-v5-5mm__rack-angle__print.step

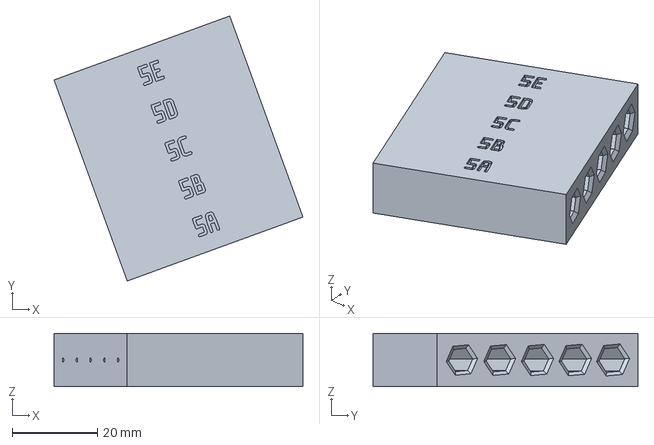
[picture p161: CAD file, 2026-10-10]
bench/reviews/tee-fit-v5-spectra/HX05-fit-v5-5mm__rack-angle__print.step
58.3 x 62.1 x 12.4 mm
