thereprocase/peg/bench/reviews/tee-fit-v6-fan/HX05-fit-v6.FCStd

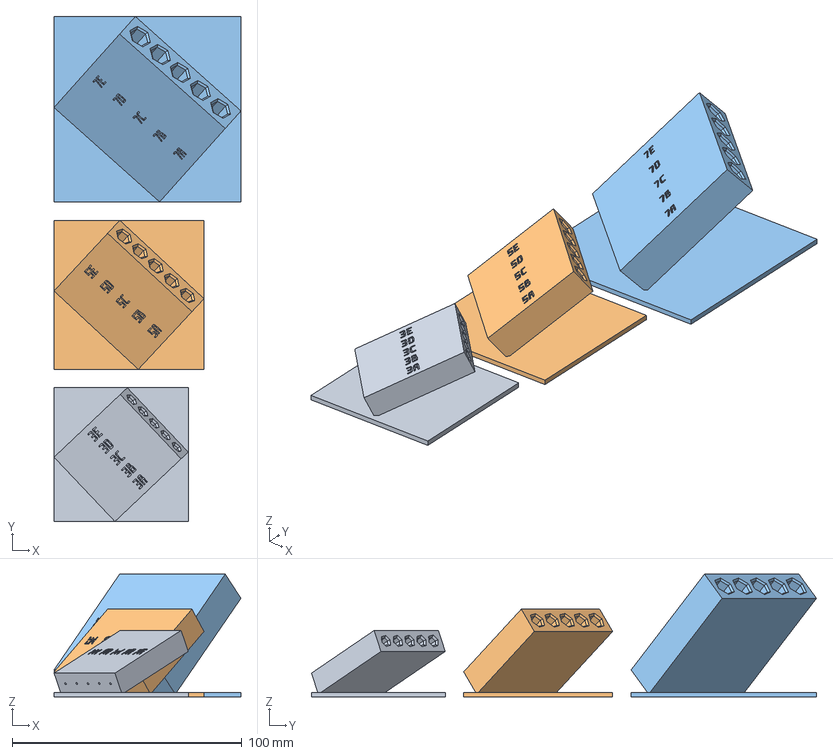
[picture p162: CAD file, 2026-10-10]
bench/reviews/tee-fit-v6-fan/HX05-fit-v6.FCStd
81.4 x 219.8 x 53.5 mm
3 mm spectrum A-E
5 mm spectrum A-E
7 mm spectrum A-E
