thereprocase/peg/docs/gallery/arrays/P01-24/print-pose.stl

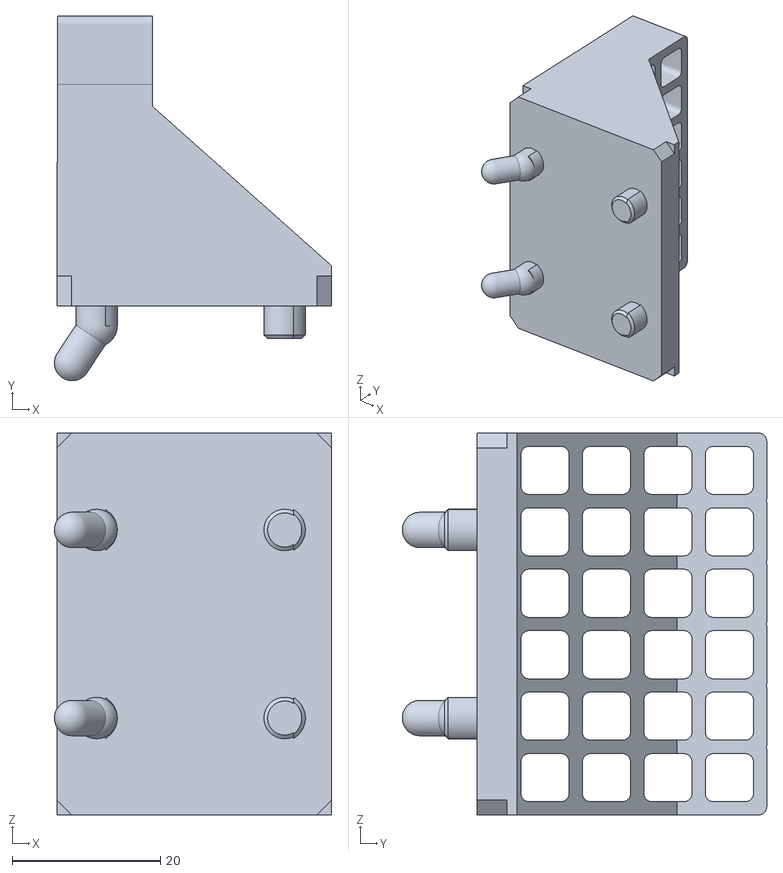
[picture p163: CAD file, 2026-09-16]
docs/gallery/arrays/P01-24/print-pose.stl
37.4 x 49.2 x 51.6
