thereprocase/peg/docs/gallery/arrays/P01-32/original.stl

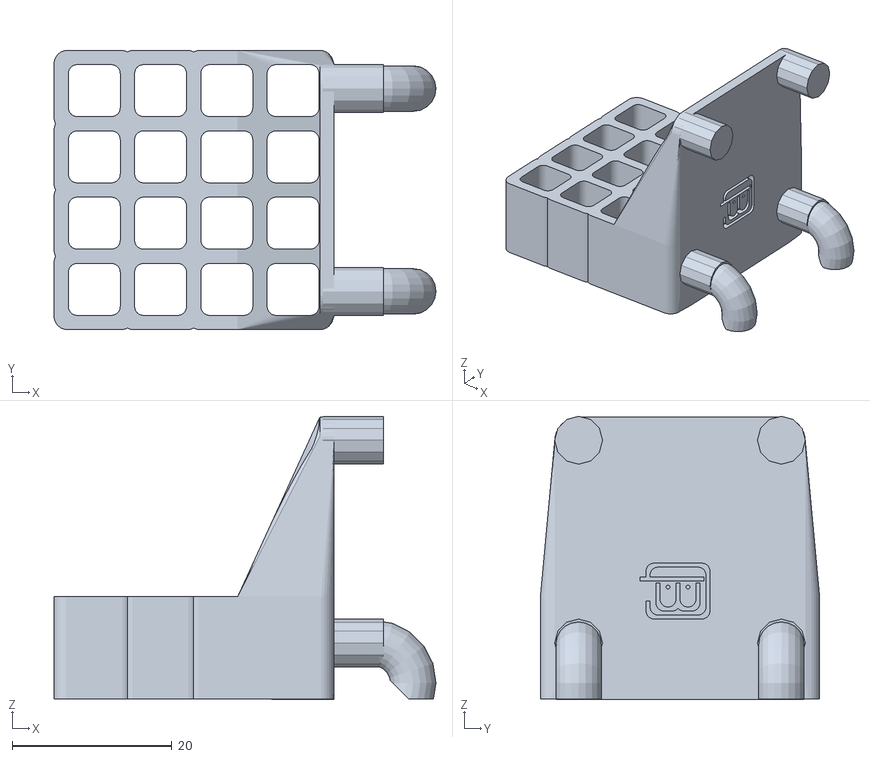
[picture p164: CAD file, 2026-09-16]
docs/gallery/arrays/P01-32/original.stl
47.9 x 35.0 x 35.5
