thereprocase/peg/docs/gallery/arrays/P09-36/print-overhangs.stl

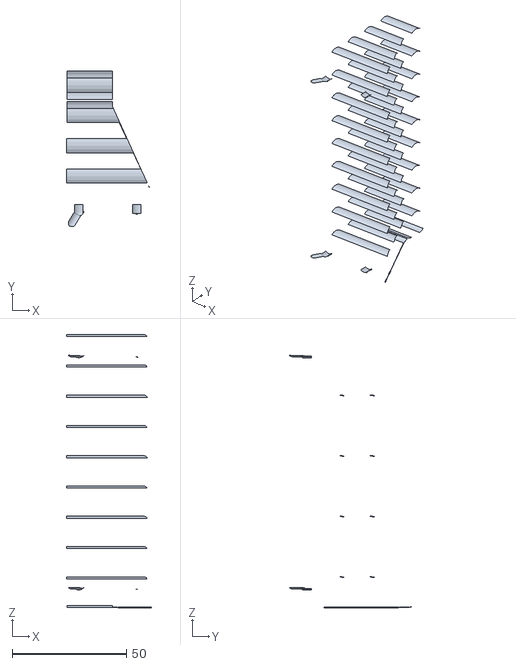
[picture p165: CAD file, 2026-09-16]
docs/gallery/arrays/P09-36/print-overhangs.stl
37.1 x 68.1 x 119.4
