thereprocase/peg/docs/gallery/arrays/P09-48/receiver.stl

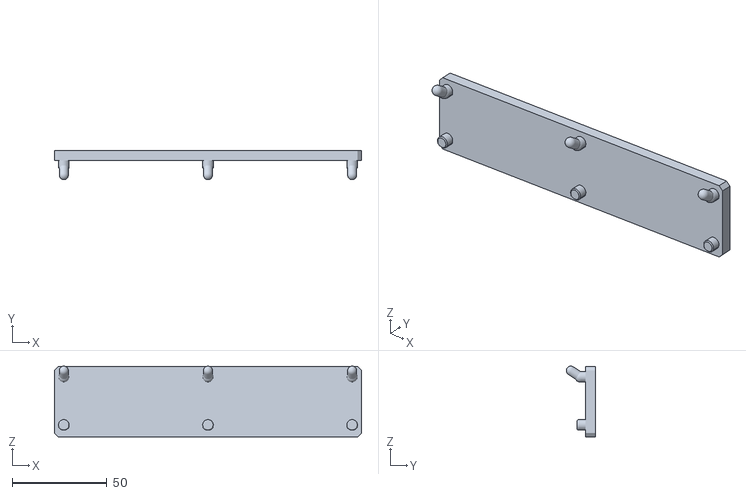
[picture p166: CAD file, 2026-09-16]
docs/gallery/arrays/P09-48/receiver.stl
162.2 x 15.5 x 37.4
