thereprocase/peg/docs/gallery/arrays/P09-72/print-overhangs.stl

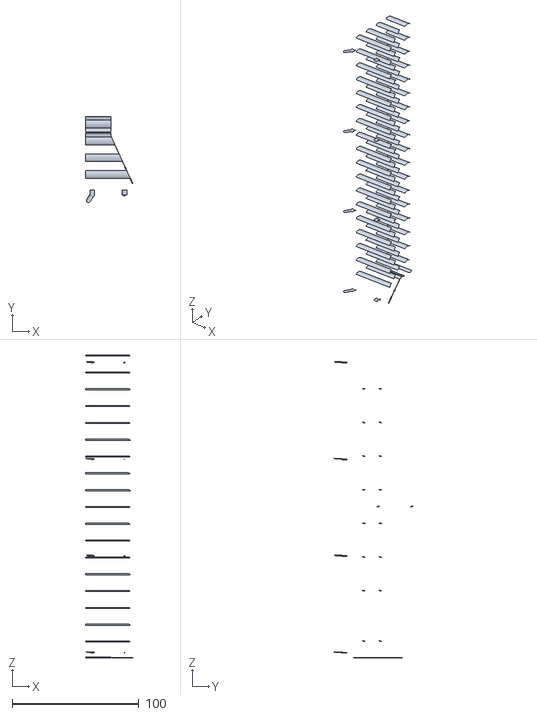
[picture p167: CAD file, 2026-09-16]
docs/gallery/arrays/P09-72/print-overhangs.stl
37.1 x 68.1 x 238.7
