thereprocase/peg/docs/gallery/bit-drivers/part-bd01-slope-e__v4__4-bit-drivers-8-cells__rack-installed__slope5-pegflat0p80__fit-e586ab4ff6.stl

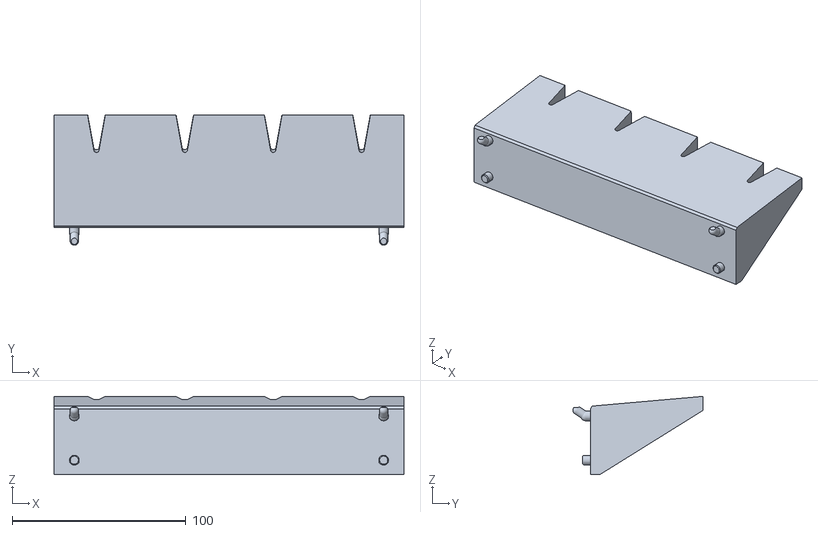
[picture p168: CAD file, 2026-09-16]
docs/gallery/bit-drivers/part-bd01-slope-e__v4__4-bit-drivers-8-cells__rack-installed__slope5-pegflat0p80__fit-e586ab4ff6.stl
201.2 x 75.0 x 45.0
