thereprocase/peg/docs/gallery/magnetic-bar/part-mb01-magnetic-shaft-bar-f__v1__2-seats-4-cells__holder-print-flat-top__fit-e586ab4ff6.stl

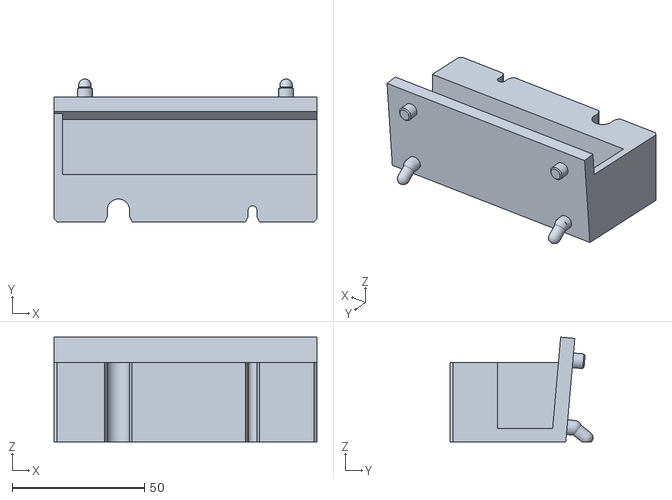
[picture p169: CAD file, 2026-09-16]
docs/gallery/magnetic-bar/part-mb01-magnetic-shaft-bar-f__v1__2-seats-4-cells__holder-print-flat-top__fit-e586ab4ff6.stl
99.6 x 54.1 x 39.6
