thereprocase/peg/docs/gallery/pegstr/P02/model.stl

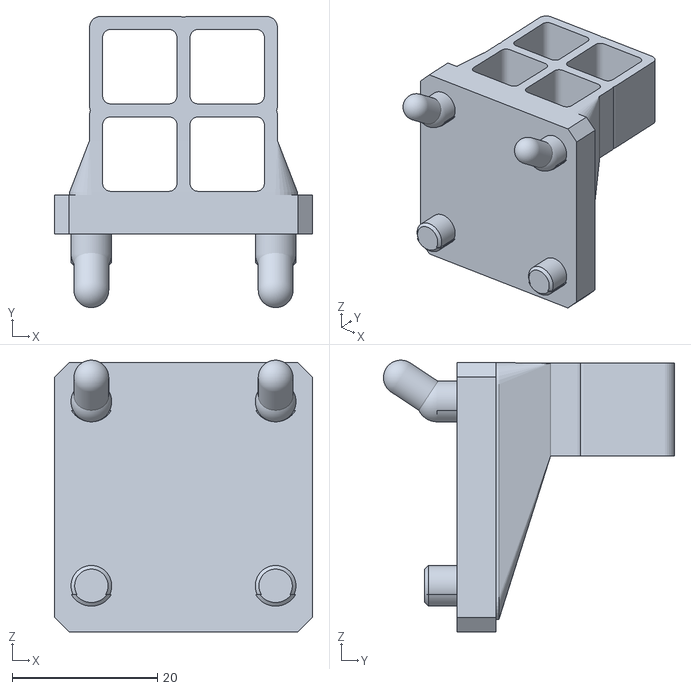
[picture p170: CAD file, 2026-09-16]
docs/gallery/pegstr/P02/model.stl
35.6 x 40.1 x 37.4
