thereprocase/peg/docs/gallery/pegstr/P03/raw-union.stl

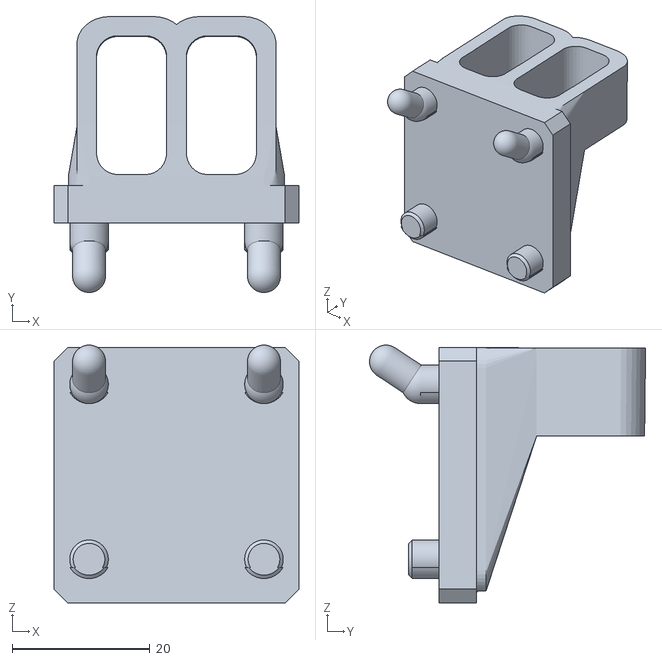
[picture p171: CAD file, 2026-09-16]
docs/gallery/pegstr/P03/raw-union.stl
35.6 x 40.1 x 37.4
