thereprocase/peg/docs/gallery/pegstr/P04/original.stl

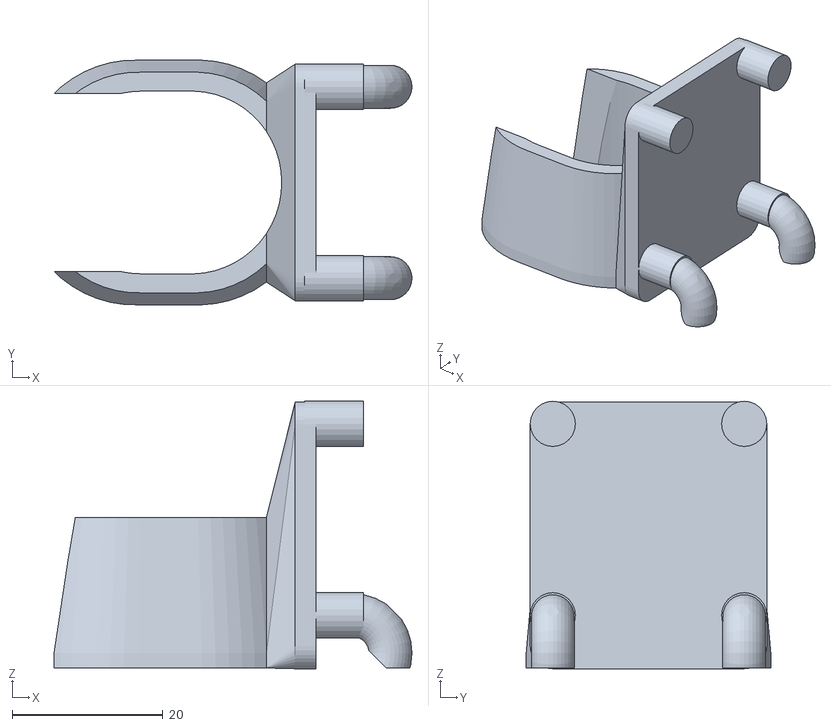
[picture p172: CAD file, 2026-09-16]
docs/gallery/pegstr/P04/original.stl
47.5 x 32.5 x 35.5
