thereprocase/peg/docs/gallery/pegstr/P06/receiver-host.stl

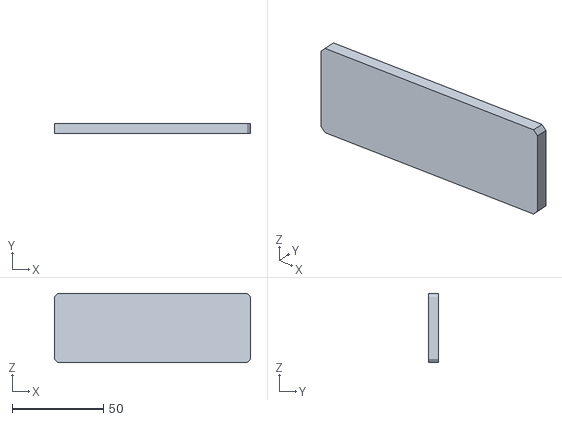
[picture p173: CAD file, 2026-09-16]
docs/gallery/pegstr/P06/receiver-host.stl
107.6 x 5.40 x 38.1
