thereprocase/peg/docs/gallery/pegstr/P07/receiver-host.stl

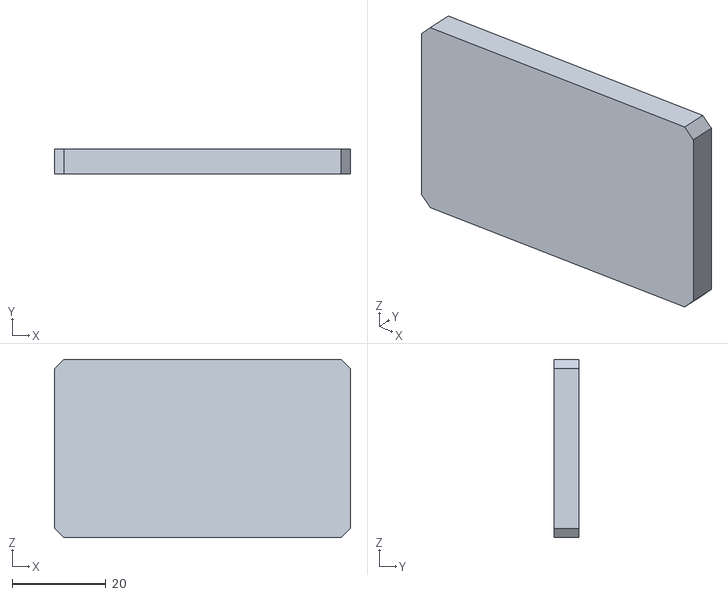
[picture p174: CAD file, 2026-09-16]
docs/gallery/pegstr/P07/receiver-host.stl
63.2 x 5.40 x 38.1
