thereprocase/peg/docs/gallery/pegstr/P10/receiver-host.stl

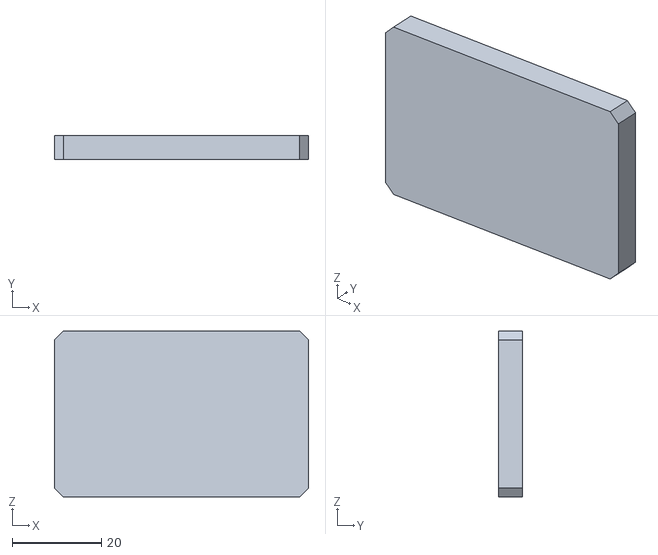
[picture p175: CAD file, 2026-09-16]
docs/gallery/pegstr/P10/receiver-host.stl
56.8 x 5.40 x 37.1
