thereprocase/peg/docs/gallery/shaft-holders/part-mh03-magnetic-shaft-holder-8mm-round__v1__4-seats-8-cells__installed__fit-e586ab4ff6.stl

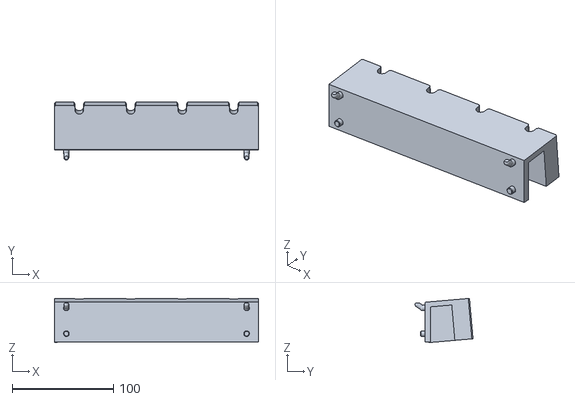
[picture p176: CAD file, 2026-09-17]
docs/gallery/shaft-holders/part-mh03-magnetic-shaft-holder-8mm-round__v1__4-seats-8-cells__installed__fit-e586ab4ff6.stl
201.2 x 57.3 x 43.7
