thereprocase/peg/docs/gallery/shaft-sampler/recoverable/combs/part-ms01-retaining-comb__v1__A-H__print-flat.stl

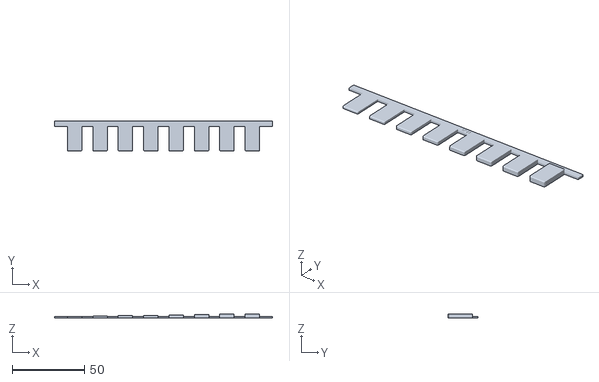
[picture p177: CAD file, 2026-09-16]
docs/gallery/shaft-sampler/recoverable/combs/part-ms01-retaining-comb__v1__A-H__print-flat.stl
150.4 x 20.8 x 3.00
