thereprocase/peg/docs/gallery/tweezers/part-solder-modules-tweezers__v9__cheek-cradle__fit-pf02c9-latch__print-right-cheek.stl

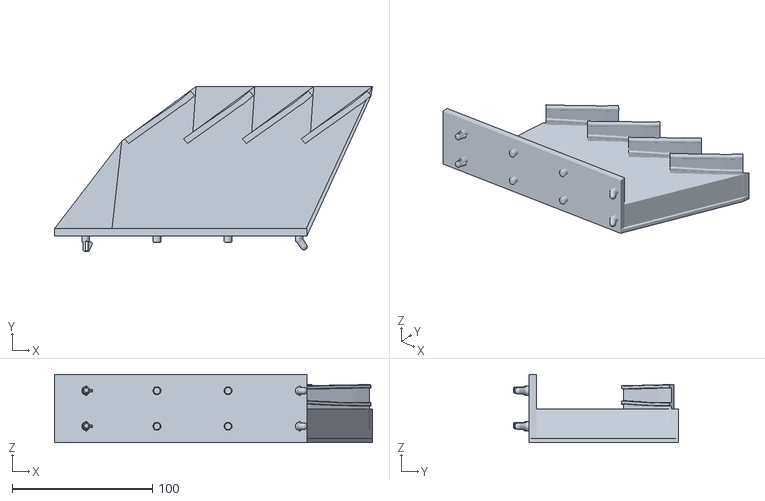
[picture p178: CAD file, 2026-10-01]
docs/gallery/tweezers/part-solder-modules-tweezers__v9__cheek-cradle__fit-pf02c9-latch__print-right-cheek.stl
227.0 x 117.8 x 48.8
