thereprocase/peg/bench/reviews/tee-fit-v2-flats-c10/L2_F_C10__installed.step

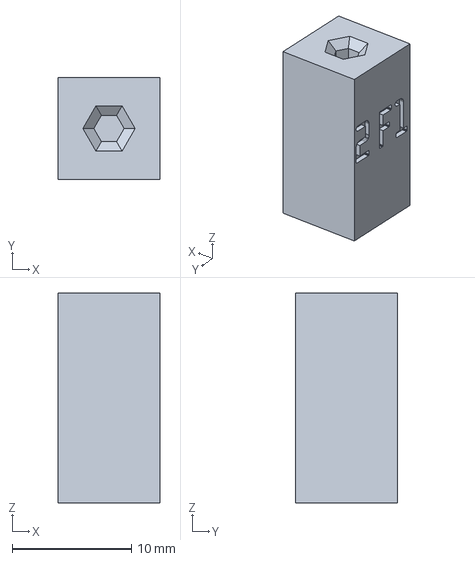
[picture p179: CAD file, 2026-10-09]
bench/reviews/tee-fit-v2-flats-c10/L2_F_C10__installed.step
8.54 x 8.54 x 17.6 mm
