thereprocase/peg/cad/round_nominal_3_16_design_reference.stl

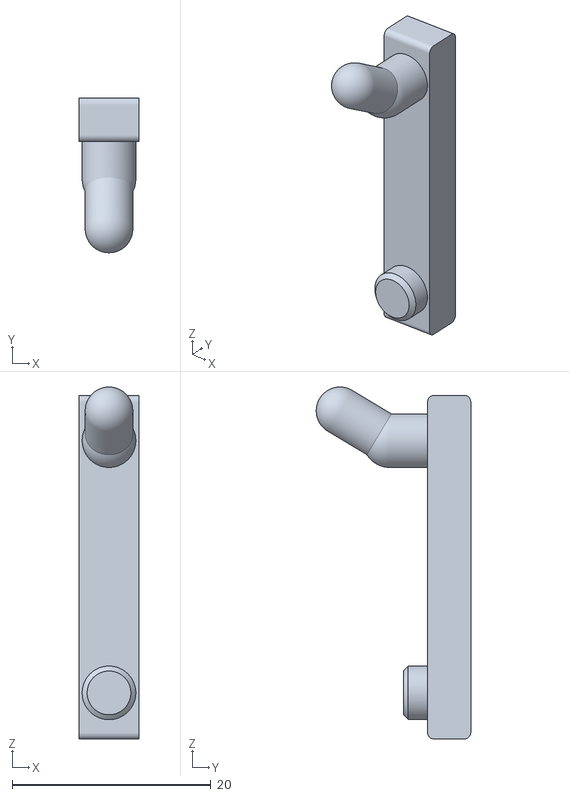
[picture p180: CAD file, 2026-09-08]
cad/round_nominal_3_16_design_reference.stl
6.00 x 15.6 x 35.4
