thereprocase/peg/docs/gallery/arrays/P01-12/print-overhangs.stl

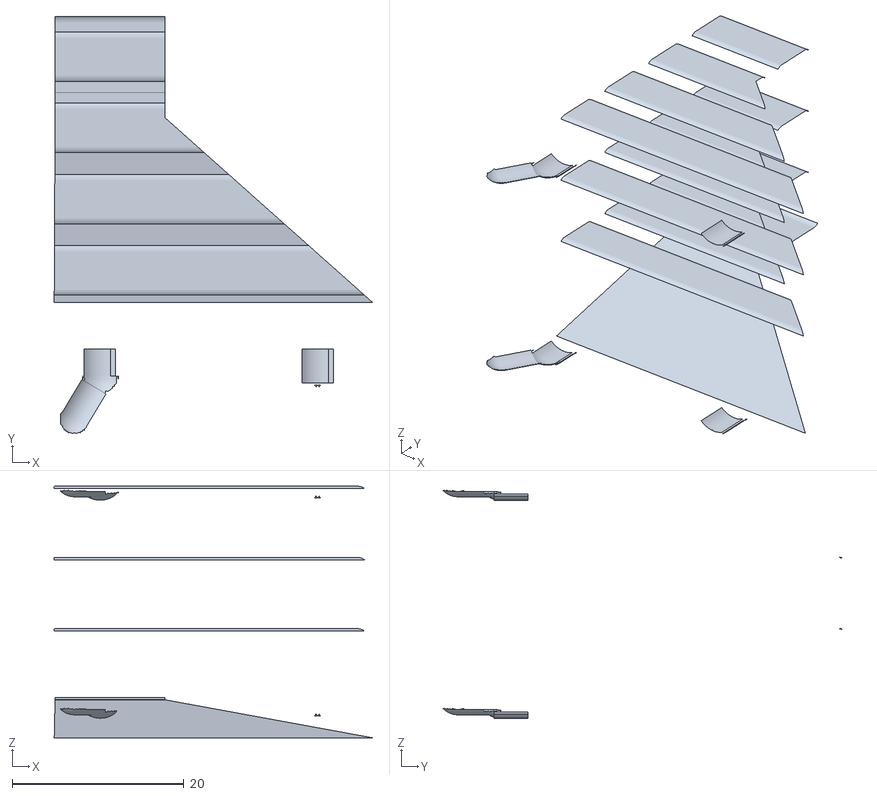
[picture p181: CAD file, 2026-09-16]
docs/gallery/arrays/P01-12/print-overhangs.stl
37.1 x 48.6 x 29.3
