thereprocase/peg/docs/gallery/arrays/P01-32/raw-union.stl

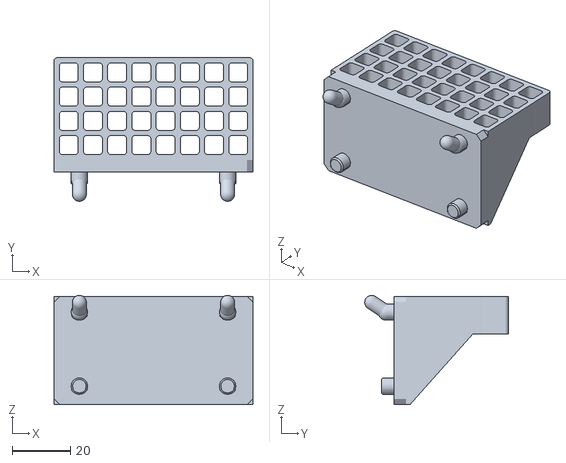
[picture p182: CAD file, 2026-09-16]
docs/gallery/arrays/P01-32/raw-union.stl
68.2 x 49.2 x 37.4
