thereprocase/peg/docs/gallery/arrays/P01-12/print-review.png

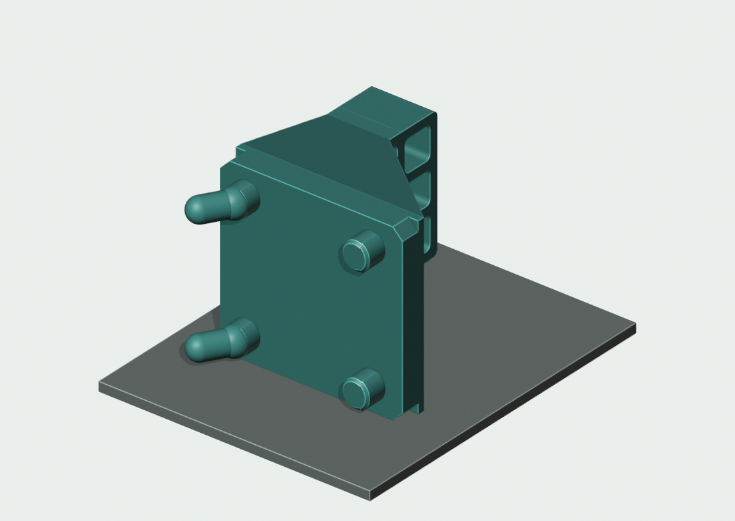
docs/gallery/arrays/P01-12/print-review.png
