thereprocase/peg/docs/gallery/arrays/P01-12/print.png

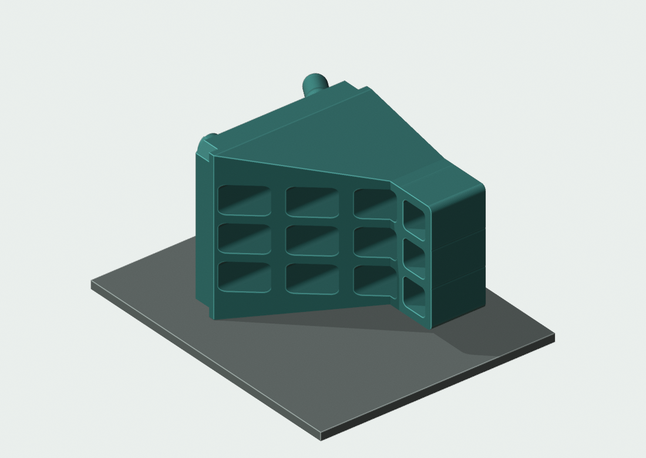
docs/gallery/arrays/P01-12/print.png
