thereprocase/peg/docs/gallery/arrays/P01-24/print.png

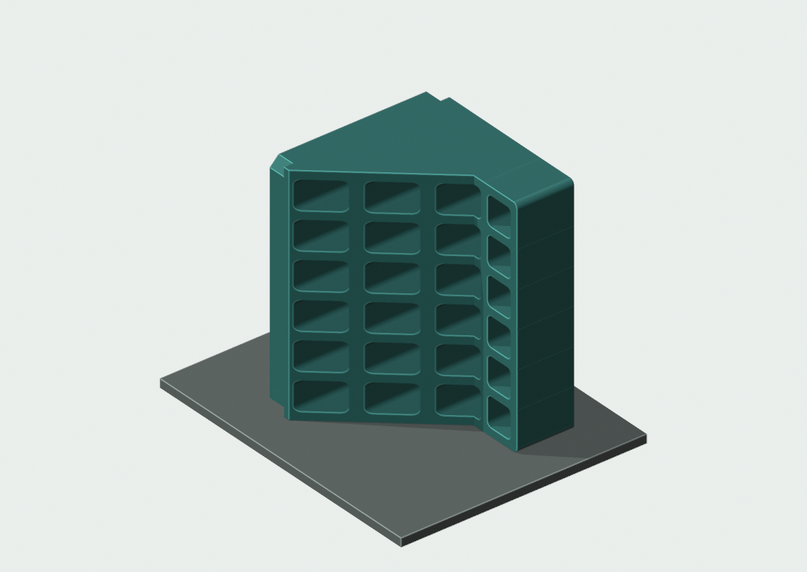
docs/gallery/arrays/P01-24/print.png
