thereprocase/peg/docs/gallery/arrays/P01-32/print-review.png

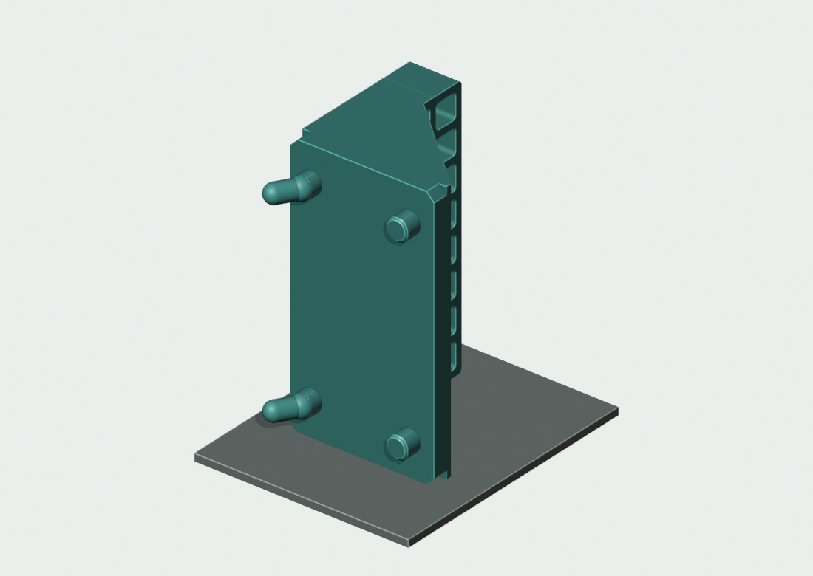
docs/gallery/arrays/P01-32/print-review.png
