thereprocase/peg/docs/gallery/arrays/P01-32/print.png

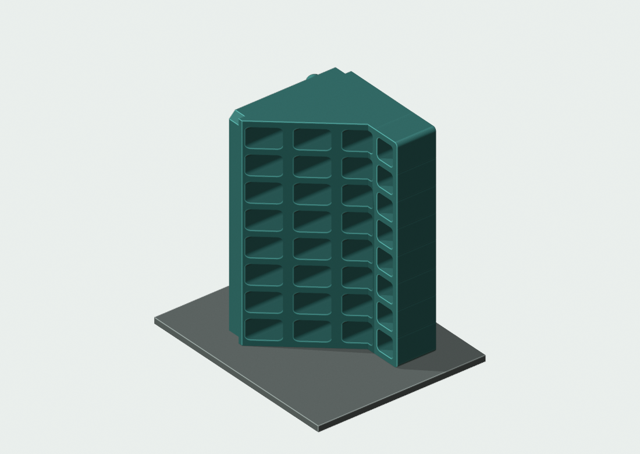
docs/gallery/arrays/P01-32/print.png
