thereprocase/peg/docs/gallery/arrays/P01-48/print-review.png

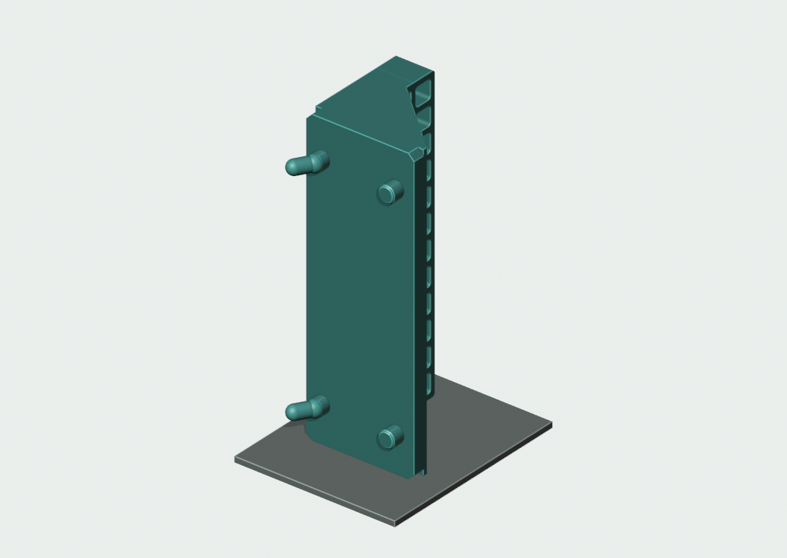
docs/gallery/arrays/P01-48/print-review.png
