thereprocase/peg/docs/gallery/arrays/P09-16/print.png

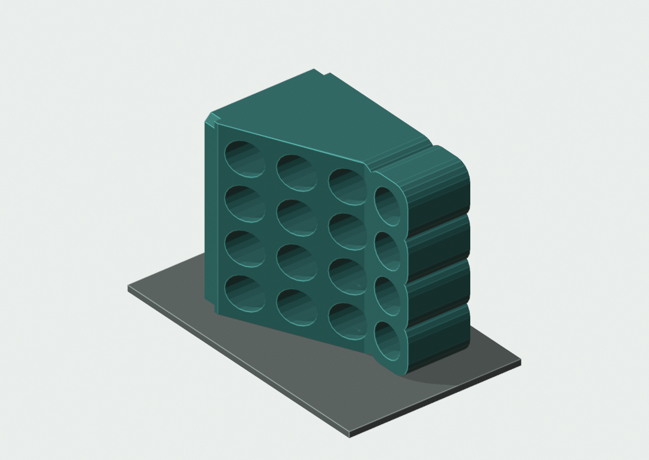
docs/gallery/arrays/P09-16/print.png
