thereprocase/peg/docs/gallery/arrays/P09-48/print-review.png

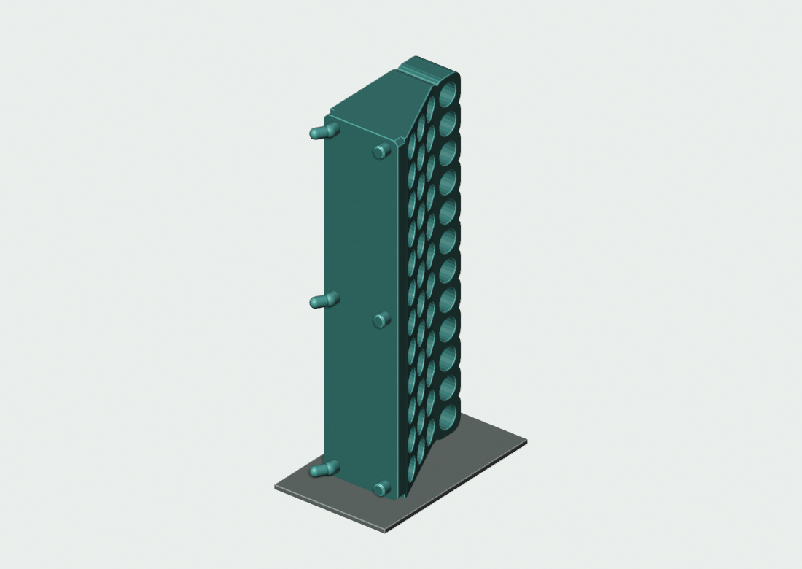
docs/gallery/arrays/P09-48/print-review.png
