thereprocase/peg/docs/gallery/arrays/P09-72/print-review.png

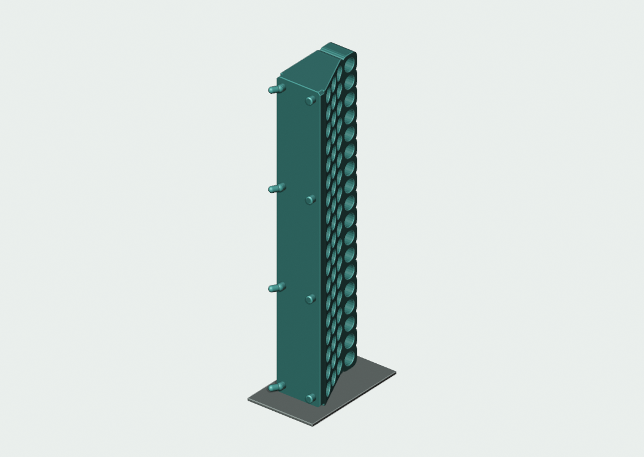
docs/gallery/arrays/P09-72/print-review.png
