thereprocase/peg/docs/gallery/bit-drivers/part-bd01-slope-e__v1__print-sloped-top.png

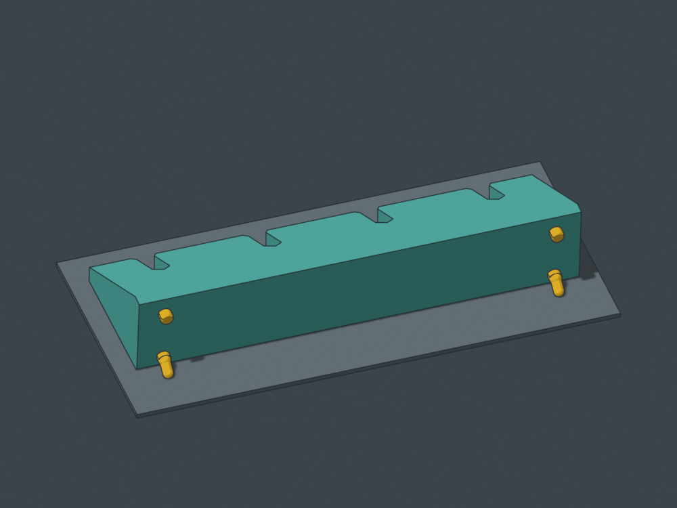
docs/gallery/bit-drivers/part-bd01-slope-e__v1__print-sloped-top.png
