thereprocase/peg/docs/gallery/current-pegs/part-cf01__v2__upright__fit-pf02c9-hoop5__installed.png

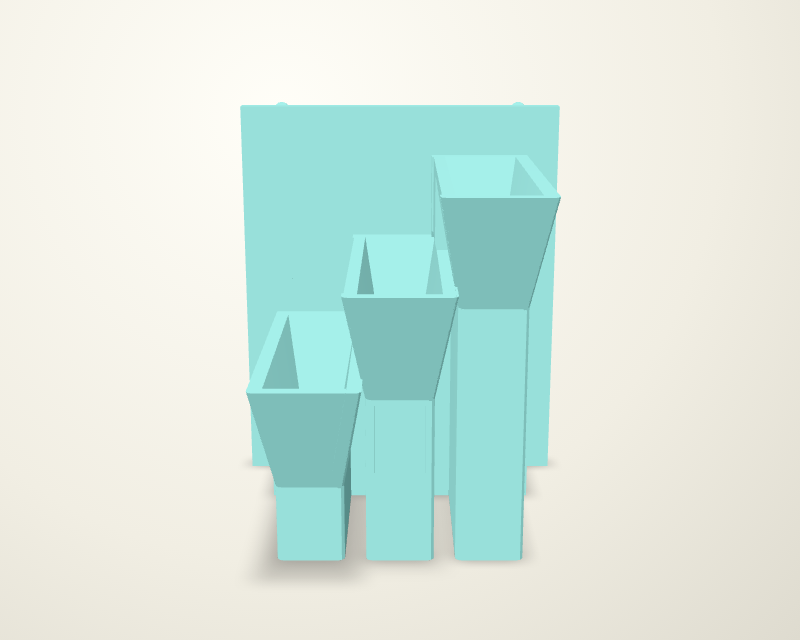
docs/gallery/current-pegs/part-cf01__v2__upright__fit-pf02c9-hoop5__installed.png
