thereprocase/peg/docs/gallery/current-pegs/part-hx02__v1__right-cheek__fit-pf02c9-hoop5__print.png

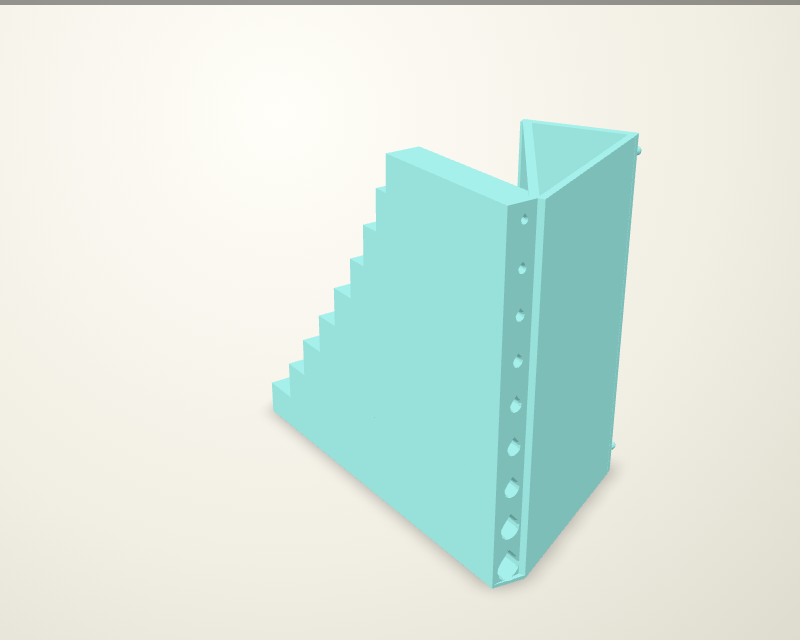
docs/gallery/current-pegs/part-hx02__v1__right-cheek__fit-pf02c9-hoop5__print.png
