thereprocase/peg/docs/gallery/current-pegs/part-hx04__v1__left-cheek__fit-pf02c9-hoop5__installed.png

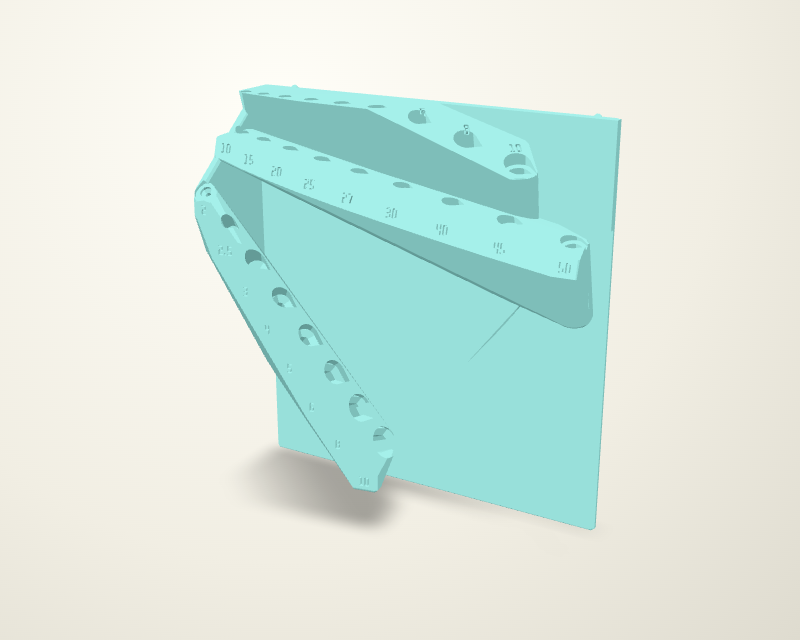
docs/gallery/current-pegs/part-hx04__v1__left-cheek__fit-pf02c9-hoop5__installed.png
