thereprocase/peg/docs/gallery/current-pegs/part-hx04__v1__left-cheek__fit-pf02c9-hoop5__print.png

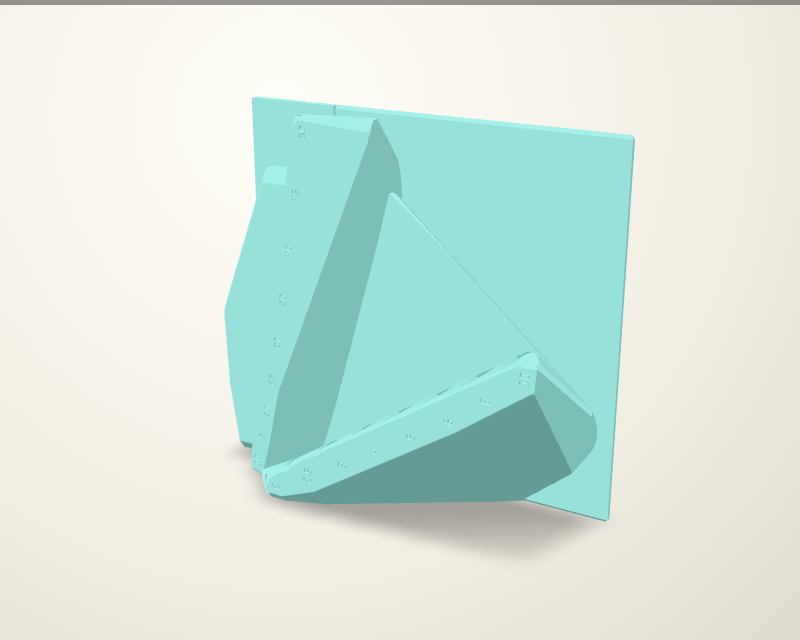
docs/gallery/current-pegs/part-hx04__v1__left-cheek__fit-pf02c9-hoop5__print.png
