thereprocase/peg/docs/gallery/current-pegs/part-p01__current-mounts-flat-top-v2__fit-pf02c9-hoop5__installed.png

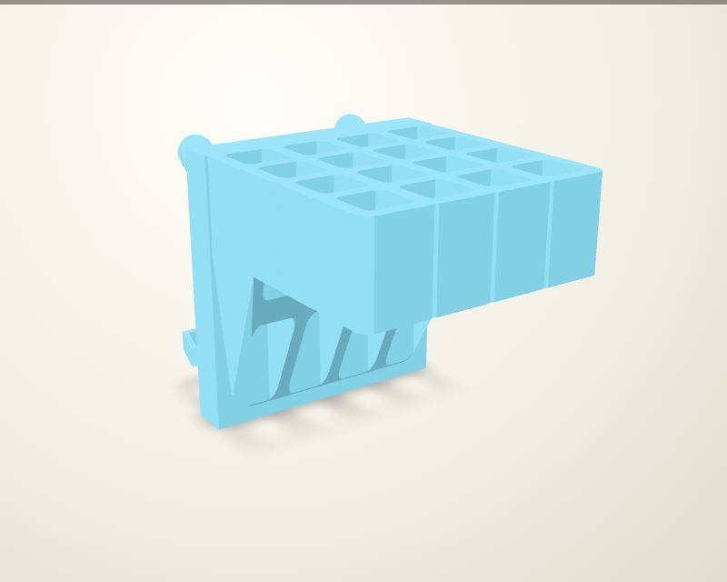
docs/gallery/current-pegs/part-p01__current-mounts-flat-top-v2__fit-pf02c9-hoop5__installed.png
