thereprocase/peg/docs/gallery/current-pegs/part-p07__current-mounts-flat-top-v2__fit-pf02c9-hoop5__print.png

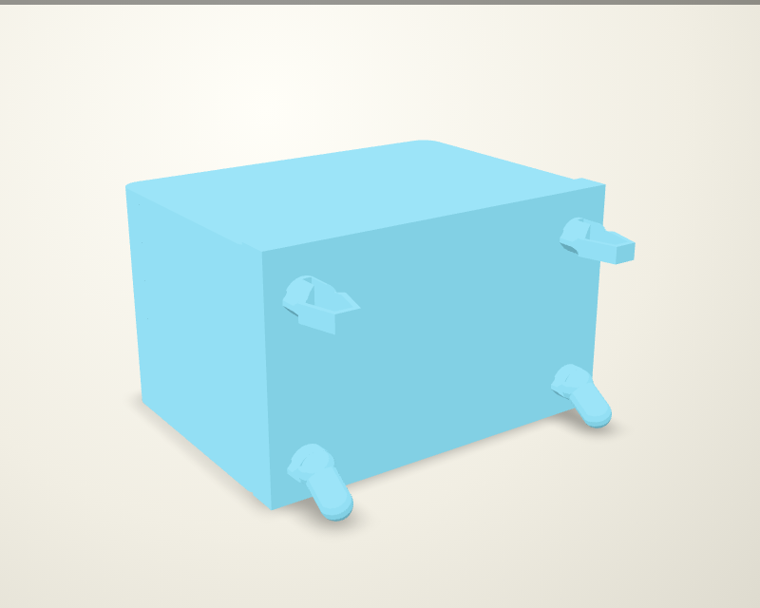
docs/gallery/current-pegs/part-p07__current-mounts-flat-top-v2__fit-pf02c9-hoop5__print.png
