thereprocase/peg/docs/gallery/current-pegs/part-rectangular-tool-funnel__v3__upright__fit-pf02c9-hoop5__print-preview.png

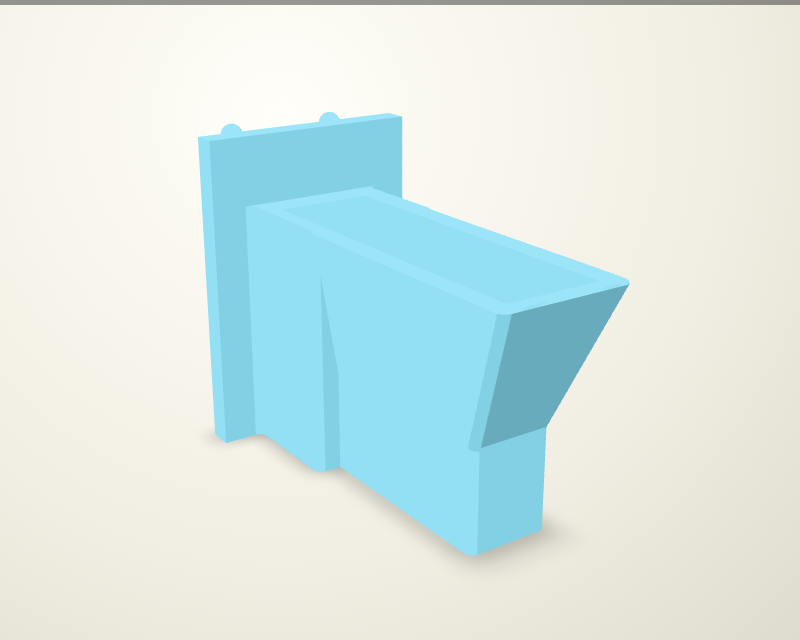
docs/gallery/current-pegs/part-rectangular-tool-funnel__v3__upright__fit-pf02c9-hoop5__print-preview.png
