thereprocase/peg/docs/gallery/current-pegs/part-reel-thick__current-mounts-v1__fit-pf02c9-hoop5__print.png

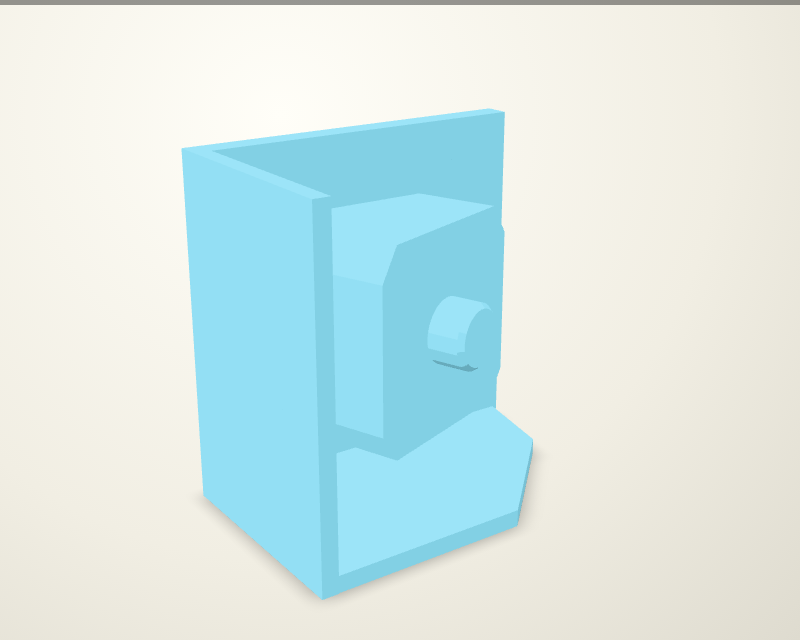
docs/gallery/current-pegs/part-reel-thick__current-mounts-v1__fit-pf02c9-hoop5__print.png
