thereprocase/peg/docs/gallery/current-pegs/part-solder-braid__v12__right-cheek__fit-pf02c9-hoop5__preview.png

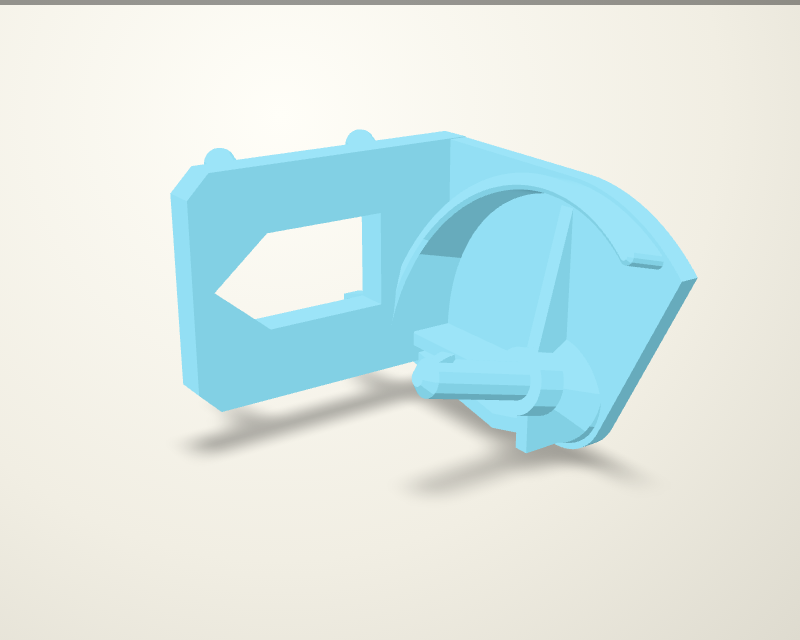
docs/gallery/current-pegs/part-solder-braid__v12__right-cheek__fit-pf02c9-hoop5__preview.png
