thereprocase/peg/docs/gallery/current-pegs/part-solder-drip-tray-liner__v12__vase-filled__preview.png

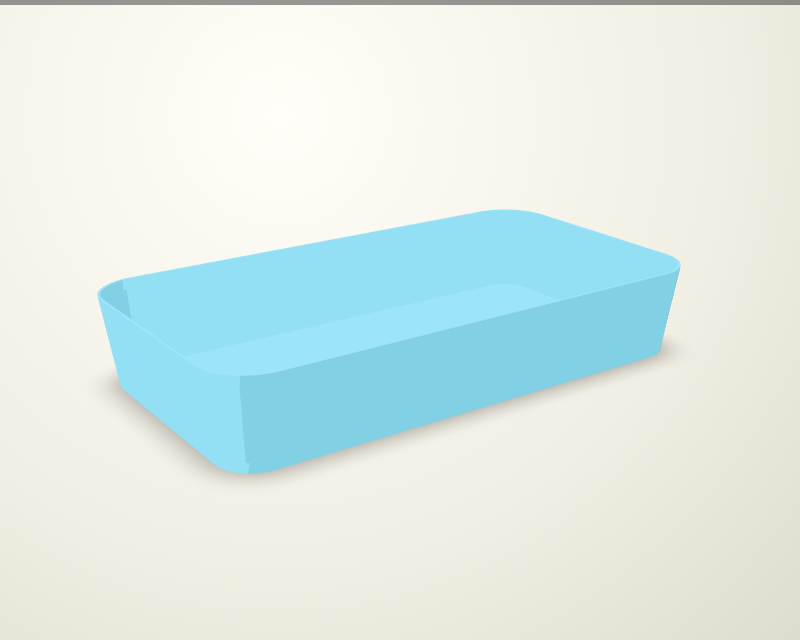
docs/gallery/current-pegs/part-solder-drip-tray-liner__v12__vase-filled__preview.png
