thereprocase/peg/docs/gallery/current-pegs/part-solder-drip-tray__v12__upright__fit-pf02c9-hoop5__preview.png

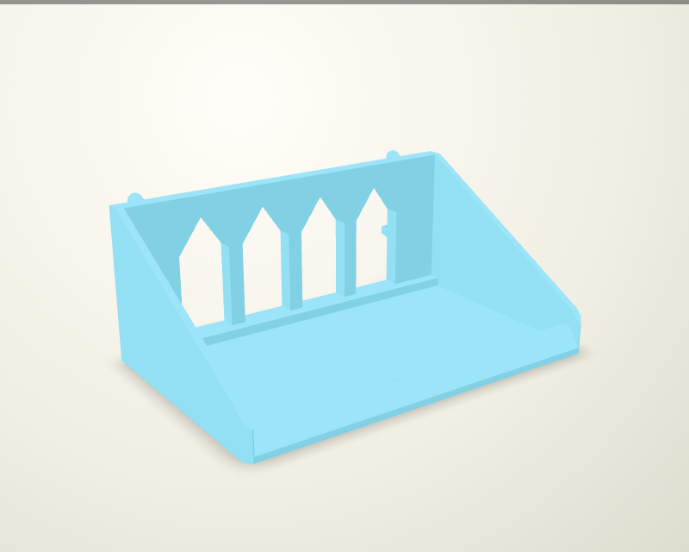
docs/gallery/current-pegs/part-solder-drip-tray__v12__upright__fit-pf02c9-hoop5__preview.png
