thereprocase/peg/docs/gallery/current-pegs/part-solder-spool-storage__v14__right-cheek__fit-pf02c9-hoop5__preview.png

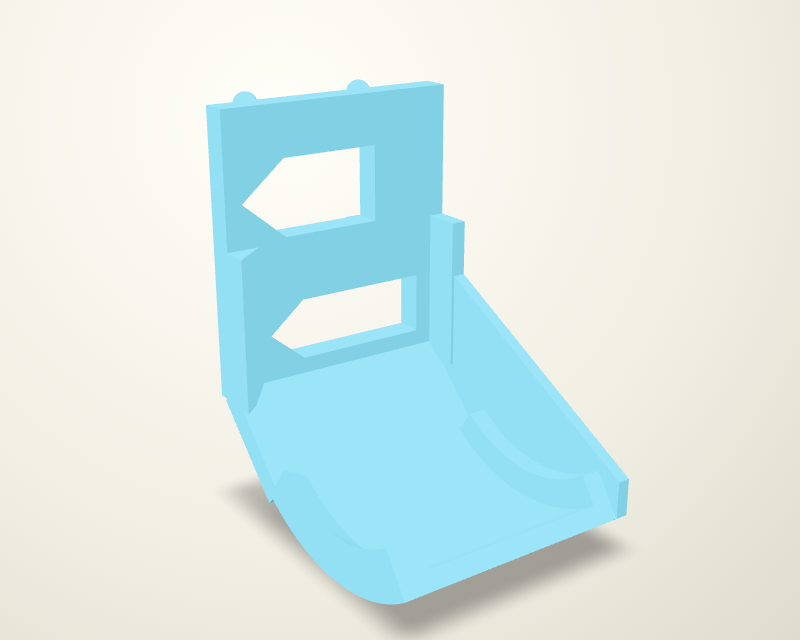
docs/gallery/current-pegs/part-solder-spool-storage__v14__right-cheek__fit-pf02c9-hoop5__preview.png
