thereprocase/peg/docs/gallery/current-pegs/part-tweezers-v10__current-mounts-v1__fit-pf02c9-hoop5__installed.png

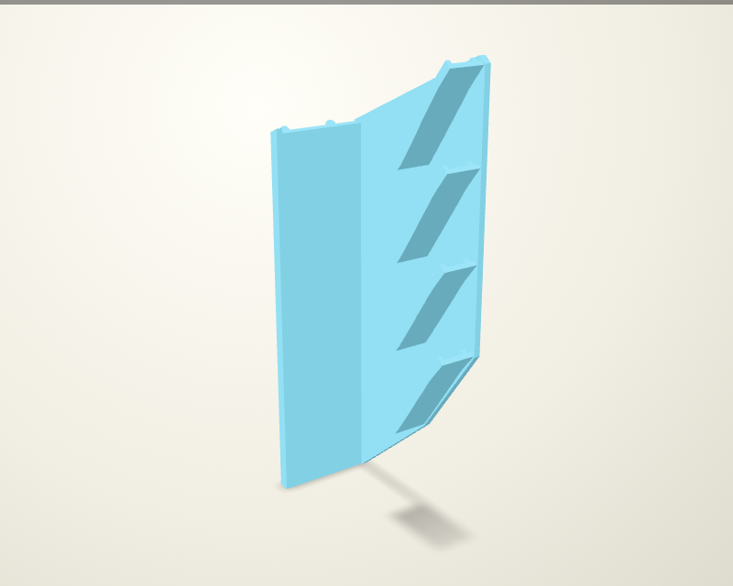
docs/gallery/current-pegs/part-tweezers-v10__current-mounts-v1__fit-pf02c9-hoop5__installed.png
