thereprocase/peg/docs/gallery/current-pegs/part-tweezers-v10__current-mounts-v1__fit-pf02c9-hoop5__print.png

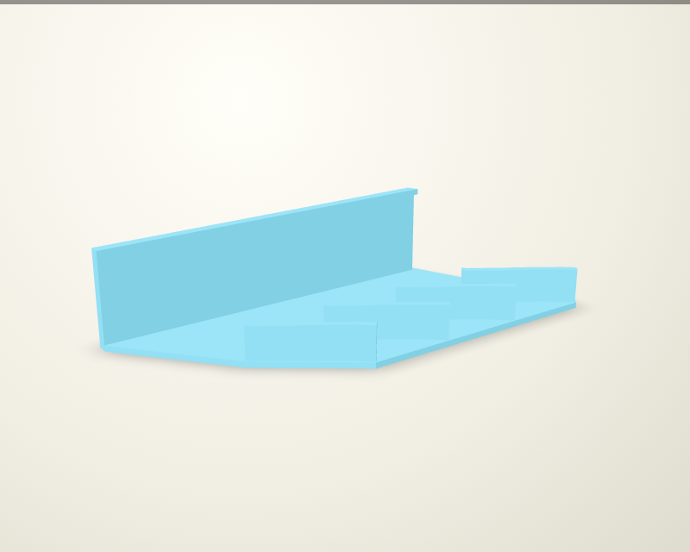
docs/gallery/current-pegs/part-tweezers-v10__current-mounts-v1__fit-pf02c9-hoop5__print.png
