thereprocase/peg/docs/gallery/current-pegs/part-tweezers__inward20-v5-A4p0-guideR6-p28__right-cheek__fit-pf02c9-hoop5__print-preview.png

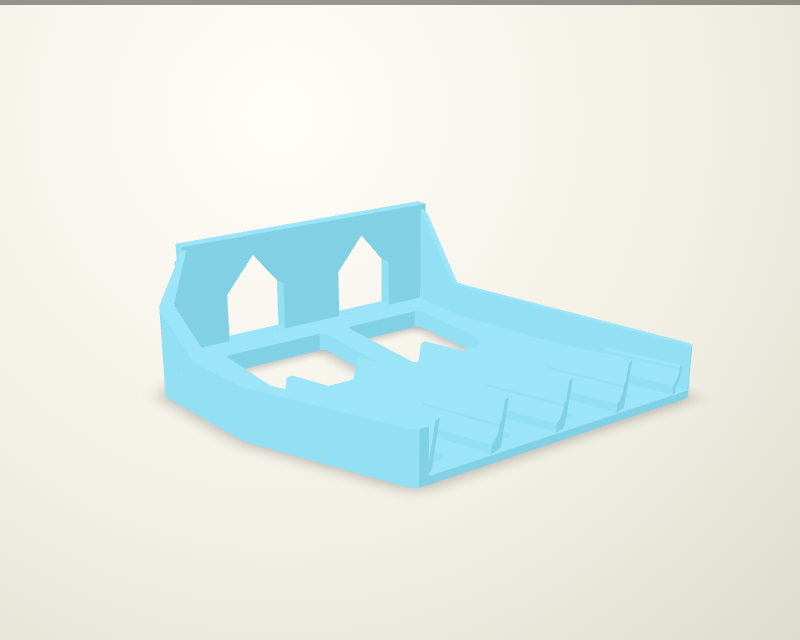
docs/gallery/current-pegs/part-tweezers__inward20-v5-A4p0-guideR6-p28__right-cheek__fit-pf02c9-hoop5__print-preview.png
