thereprocase/peg/docs/gallery/key-fan/final/HX04/print.jpg

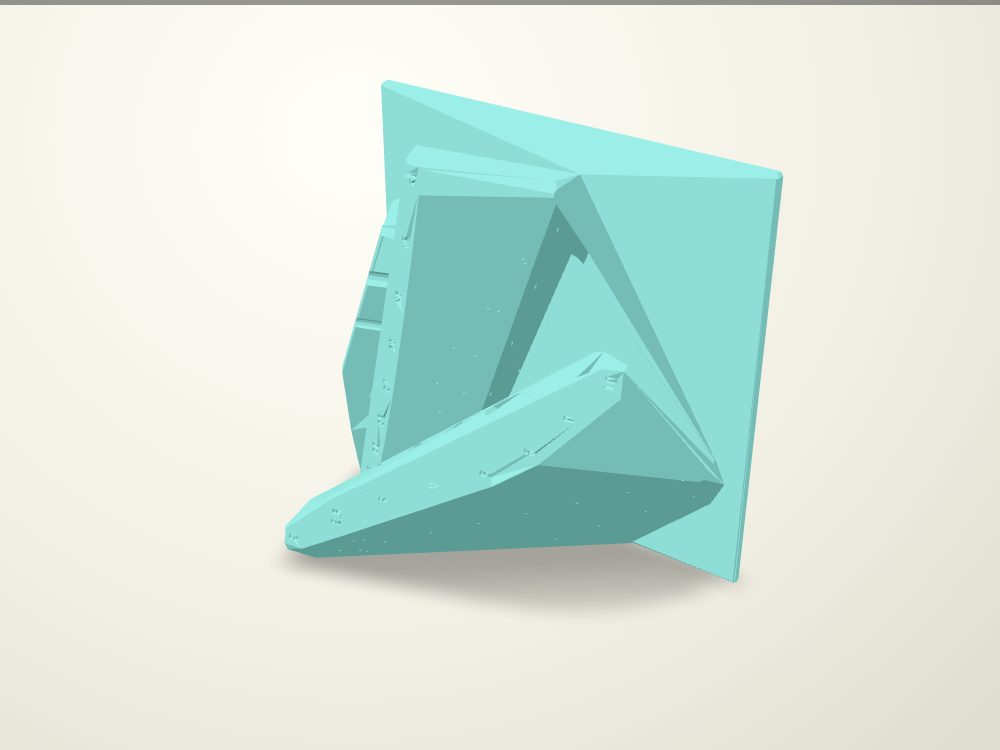
docs/gallery/key-fan/final/HX04/print.jpg
