thereprocase/peg/docs/gallery/key-fan/final/HX05A/print.jpg

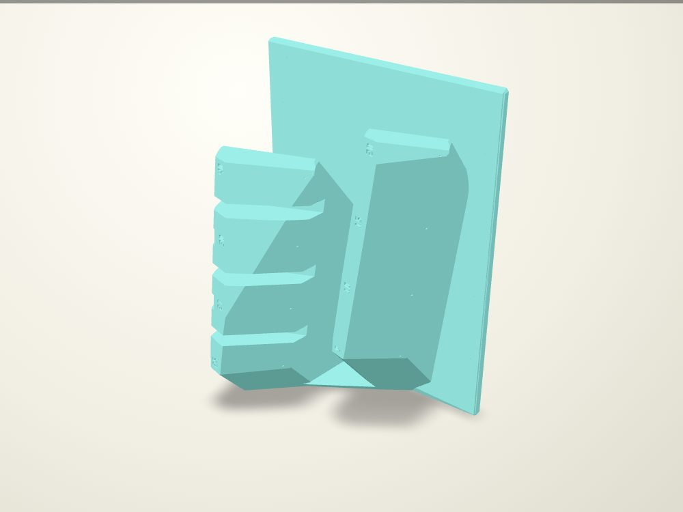
docs/gallery/key-fan/final/HX05A/print.jpg
