thereprocase/peg/docs/gallery/key-fan/final/HX05B/print.jpg

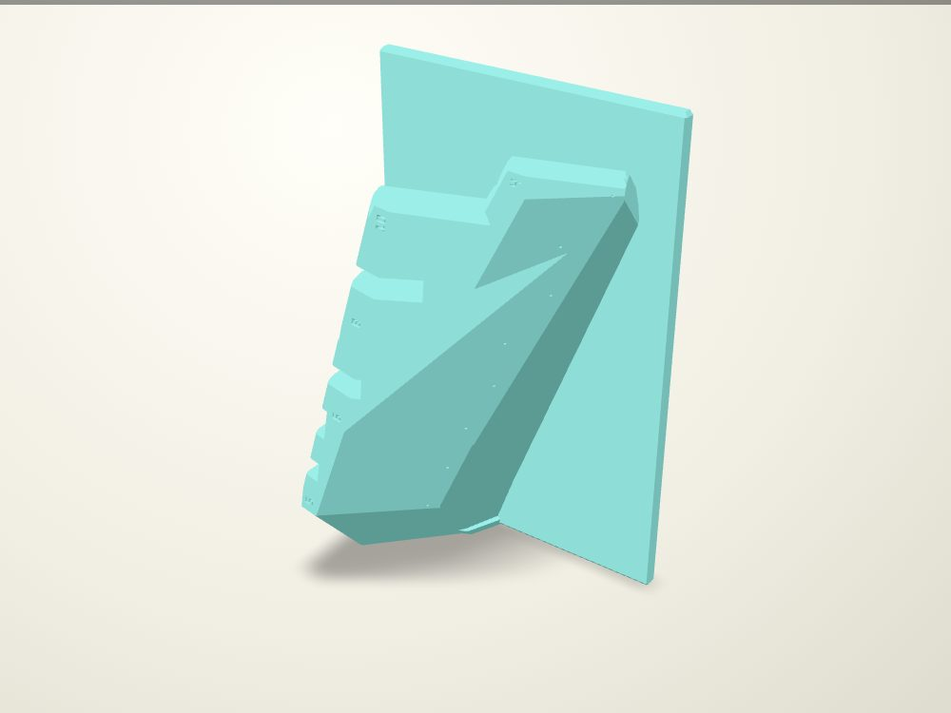
docs/gallery/key-fan/final/HX05B/print.jpg
