thereprocase/peg/docs/gallery/key-fan/stacked/green/HX05C-print-hero.jpg

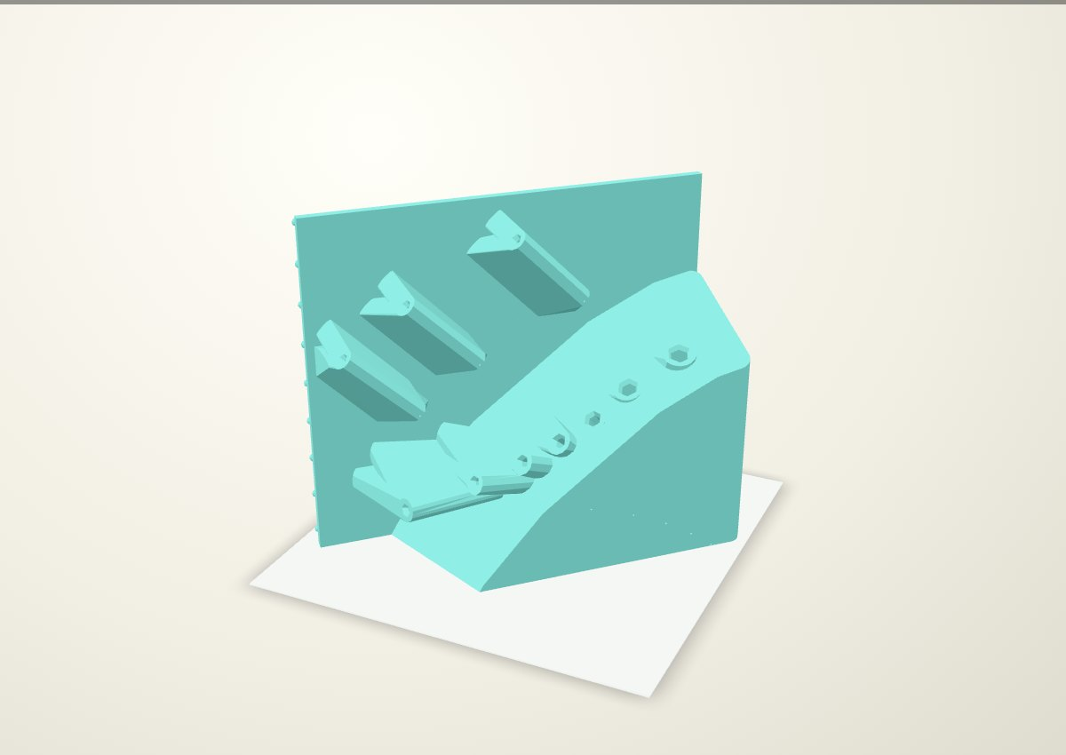
docs/gallery/key-fan/stacked/green/HX05C-print-hero.jpg
