thereprocase/peg/docs/gallery/key-fan/studies/media/install-full-host.jpg

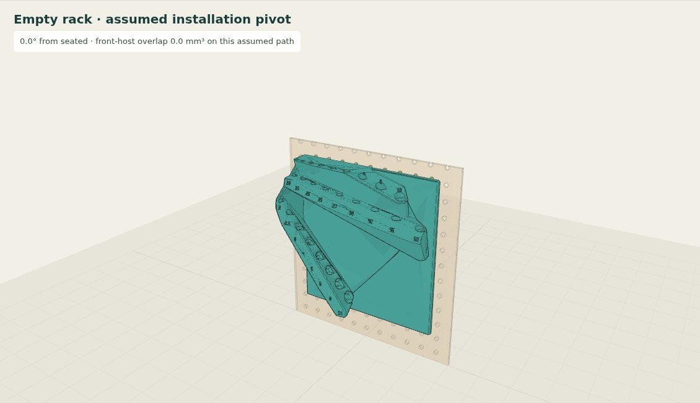
docs/gallery/key-fan/studies/media/install-full-host.jpg
