thereprocase/peg/docs/gallery/magnetic-bar/part-mb01-magnetic-shaft-bar-f__v1__print-flat-top.png

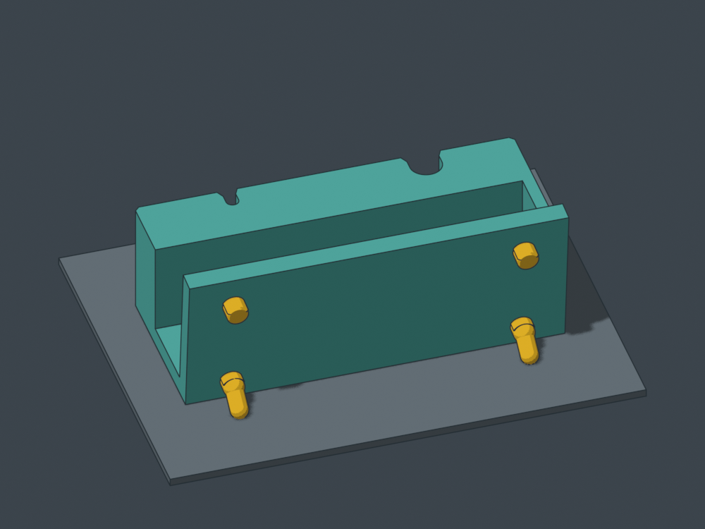
docs/gallery/magnetic-bar/part-mb01-magnetic-shaft-bar-f__v1__print-flat-top.png
