thereprocase/peg/docs/gallery/screwdrivers-b/SD01/part-sd01__v1__a-upright-print-faces.png

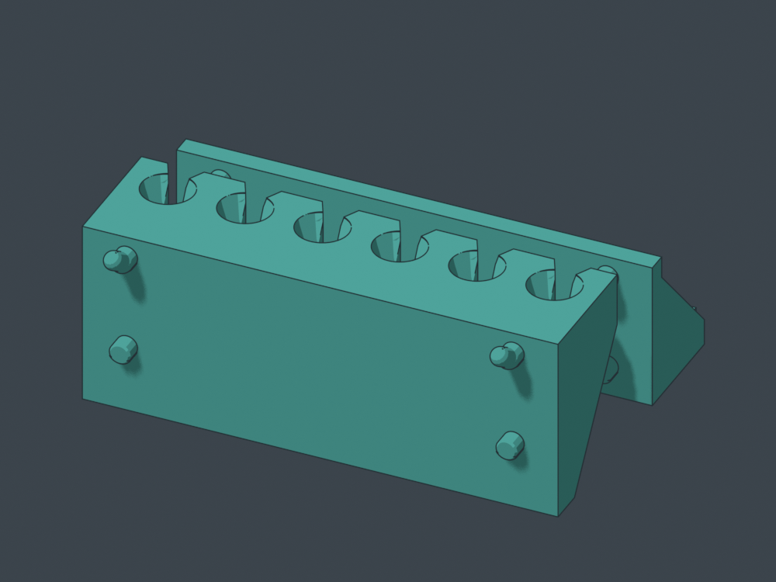
docs/gallery/screwdrivers-b/SD01/part-sd01__v1__a-upright-print-faces.png
