thereprocase/peg/docs/gallery/screwdrivers-b/SD01/part-sd01__v3__flat-b-print.png

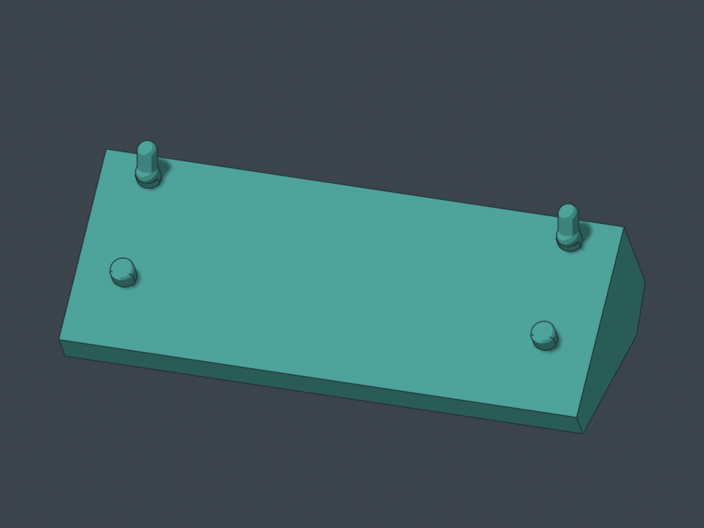
docs/gallery/screwdrivers-b/SD01/part-sd01__v3__flat-b-print.png
