thereprocase/peg/docs/gallery/screwdrivers-b/SD02/part-sd02__v1__a-upright-print-faces.png

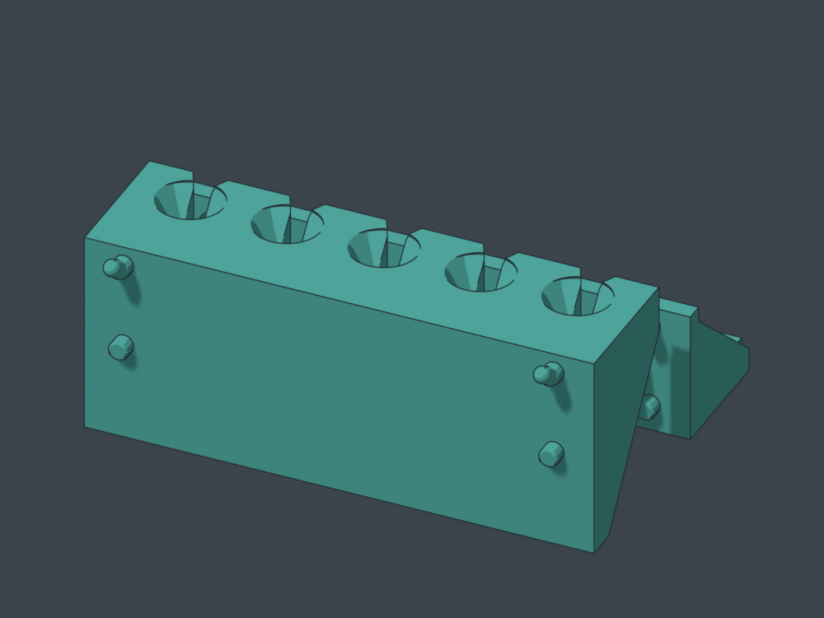
docs/gallery/screwdrivers-b/SD02/part-sd02__v1__a-upright-print-faces.png
