thereprocase/peg/docs/gallery/screwdrivers-b/SD03/part-sd03__v3__flat-b-print-front.png

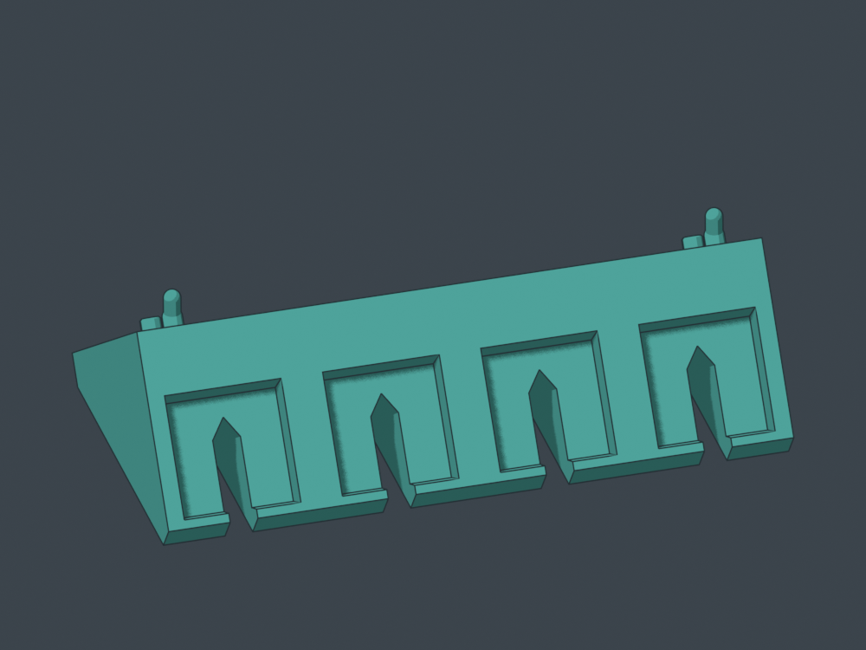
docs/gallery/screwdrivers-b/SD03/part-sd03__v3__flat-b-print-front.png
