thereprocase/peg/docs/gallery/screwdrivers-c/part-sd03-magnetic-c__v1__upright-print-and-plug.png

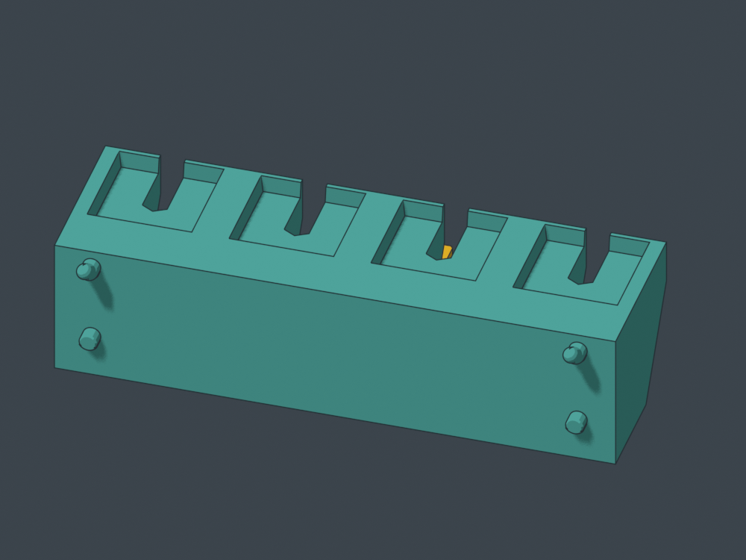
docs/gallery/screwdrivers-c/part-sd03-magnetic-c__v1__upright-print-and-plug.png
