thereprocase/peg/docs/gallery/screwdrivers-d/part-sd03-inverted-d__v1__print-flat-top-peg-review.png

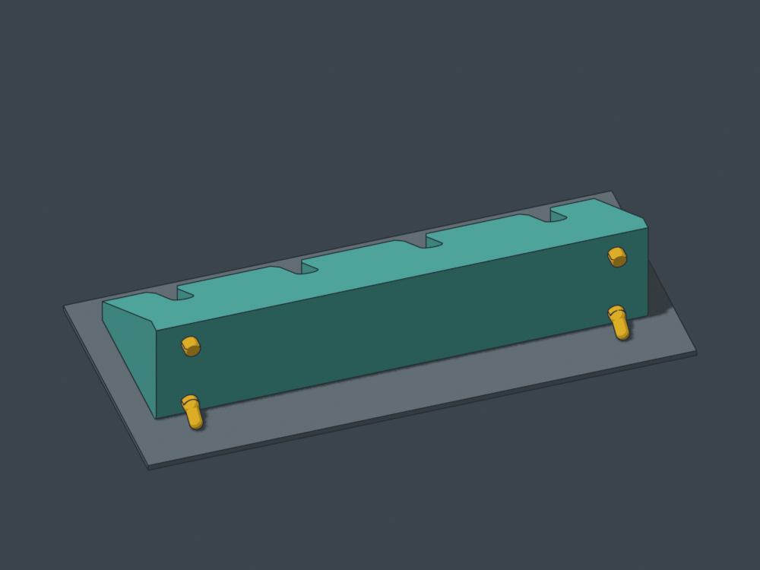
docs/gallery/screwdrivers-d/part-sd03-inverted-d__v1__print-flat-top-peg-review.png
