thereprocase/peg/docs/gallery/screwdrivers/SD01/part-sd01__v2__upright-print-faces.png

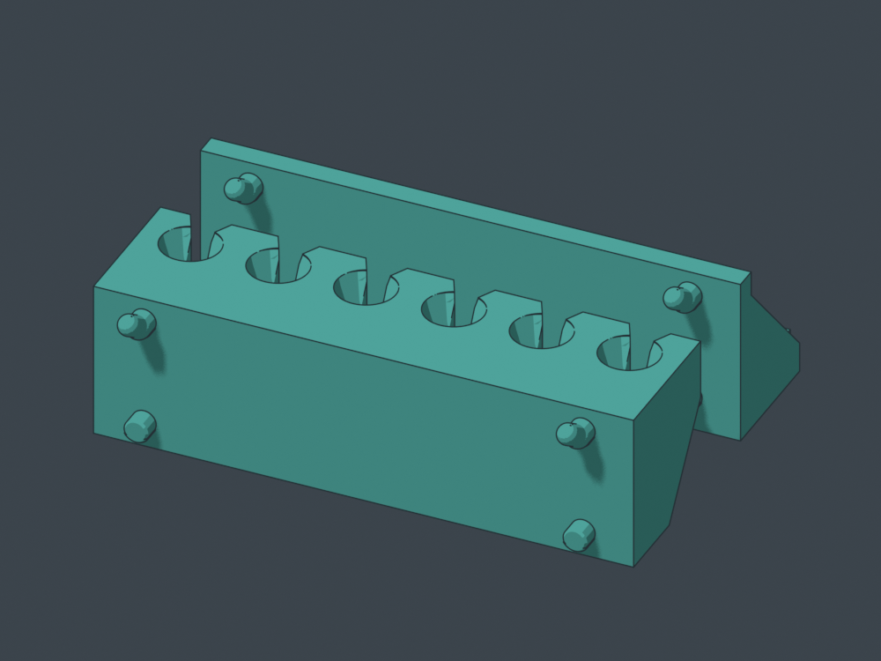
docs/gallery/screwdrivers/SD01/part-sd01__v2__upright-print-faces.png
