thereprocase/peg/docs/gallery/screwdrivers/SD04/part-sd04__v2__upright-print-faces.png

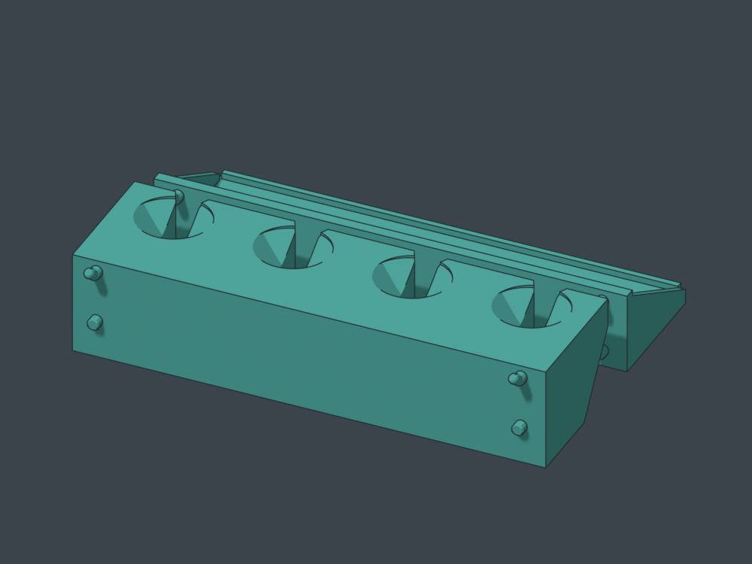
docs/gallery/screwdrivers/SD04/part-sd04__v2__upright-print-faces.png
