thereprocase/peg/docs/gallery/shaft-sampler/part-ms01-shaft-fit-sampler-20x10x3__v1__print-top-down.png

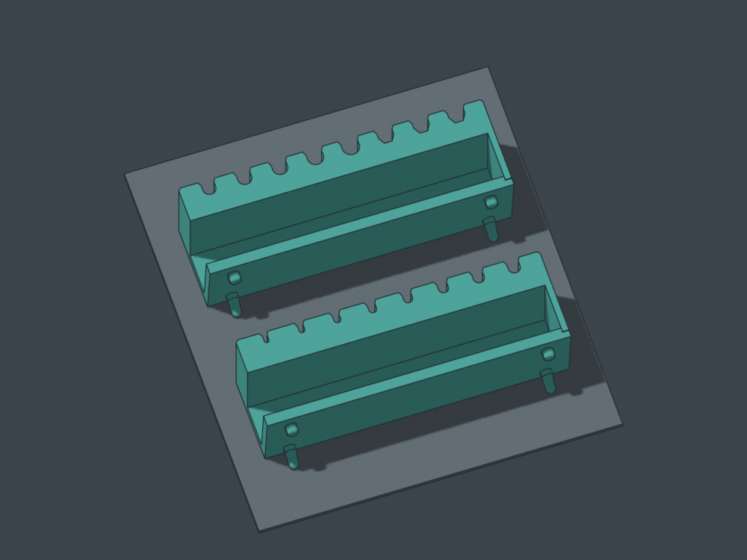
docs/gallery/shaft-sampler/part-ms01-shaft-fit-sampler-20x10x3__v1__print-top-down.png
