thereprocase/peg/docs/gallery/shaft-sampler/recoverable/combs/part-ms01-retaining-comb__v1__installed-retainer.png

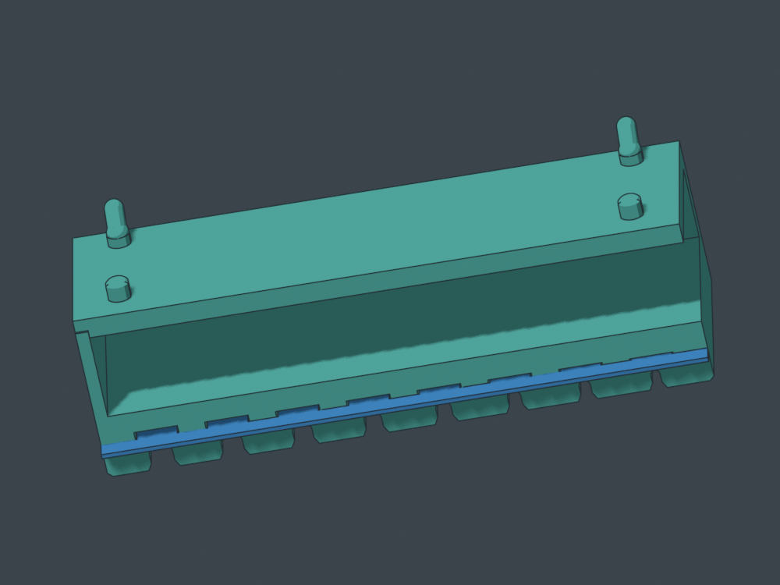
docs/gallery/shaft-sampler/recoverable/combs/part-ms01-retaining-comb__v1__installed-retainer.png
