thereprocase/peg/docs/gallery/shaft-sampler/recoverable/combs/part-ms01-retaining-comb__v1__two-combs-print-flat.png

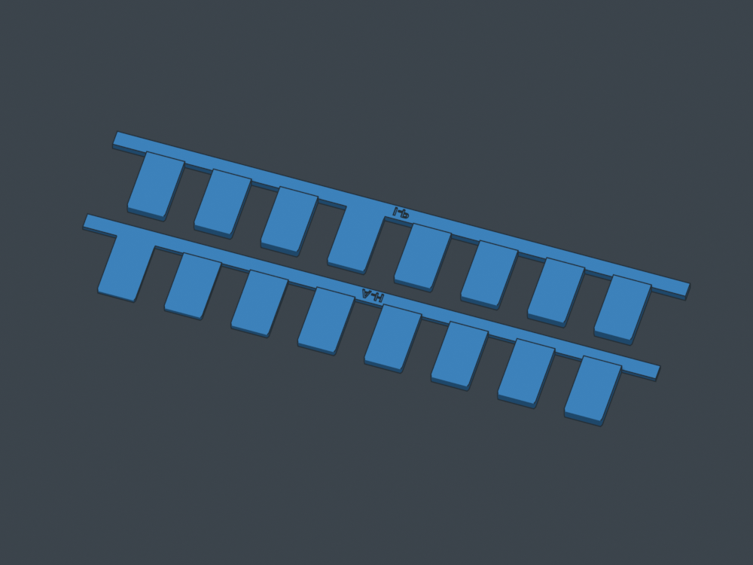
docs/gallery/shaft-sampler/recoverable/combs/part-ms01-retaining-comb__v1__two-combs-print-flat.png
