thereprocase/peg/docs/gallery/solder-modules/tweezers-toolpaths.png

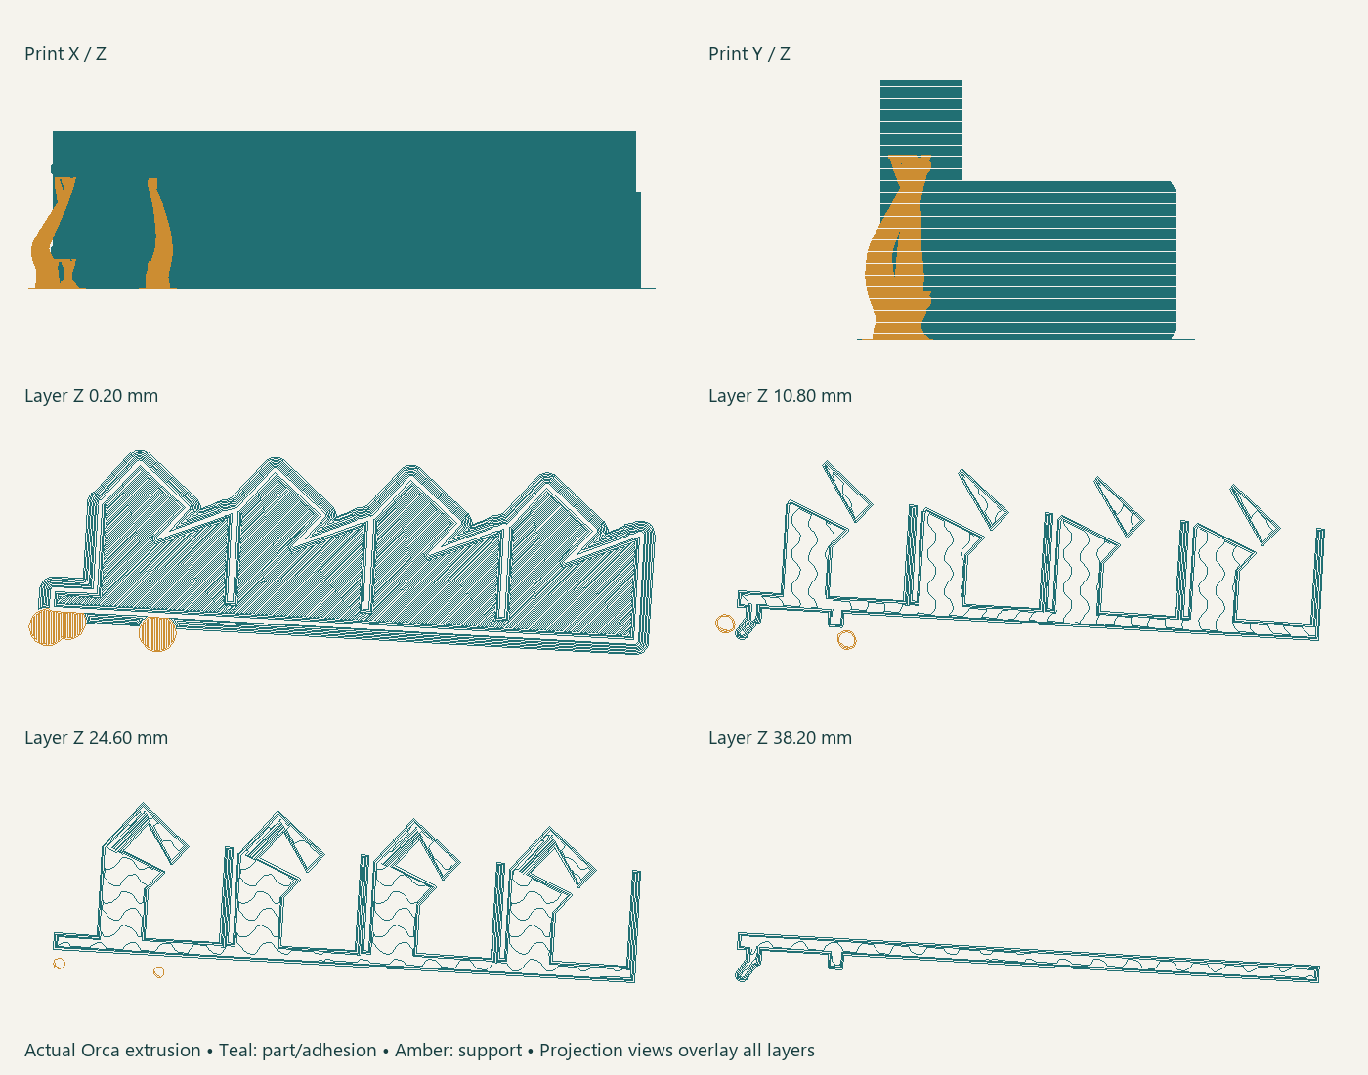
docs/gallery/solder-modules/tweezers-toolpaths.png
