thereprocase/peg/docs/gallery/solder-modules/tweezers.png

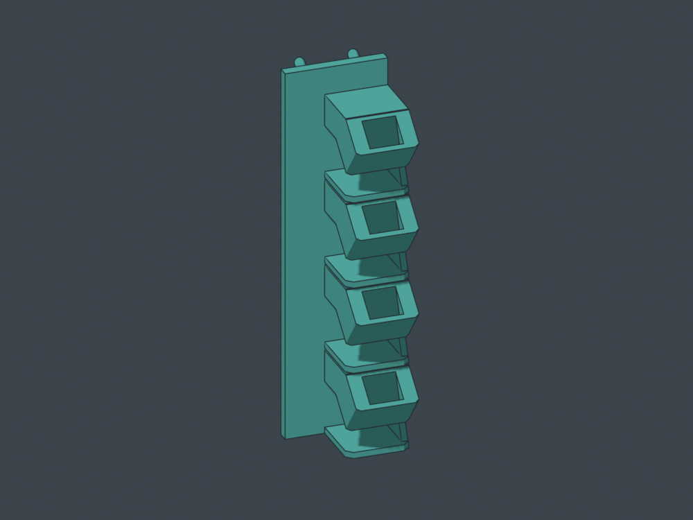
docs/gallery/solder-modules/tweezers.png
