thereprocase/peg/docs/gallery/tweezers/part-solder-modules-tweezers__v7__loaded.png

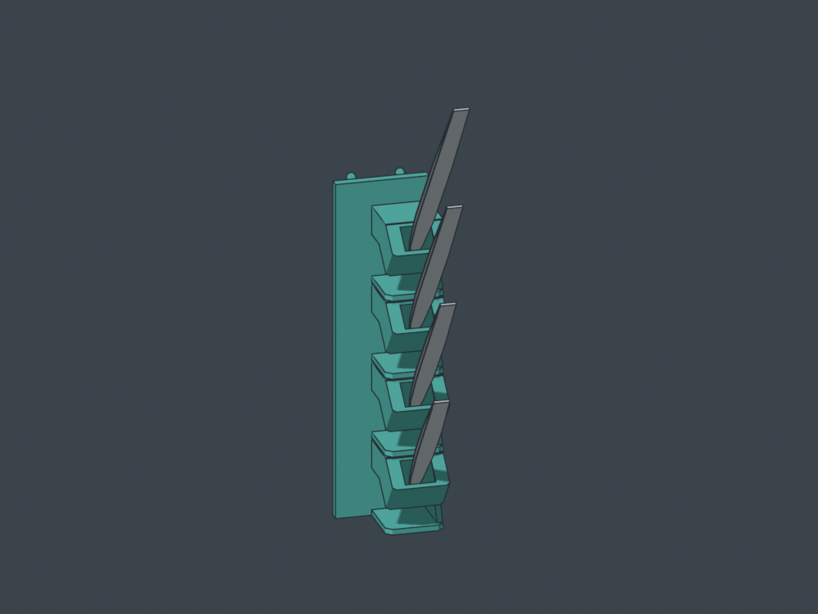
docs/gallery/tweezers/part-solder-modules-tweezers__v7__loaded.png
