thereprocase/peg/docs/gallery/tweezers/part-solder-modules-tweezers__v7__print.png

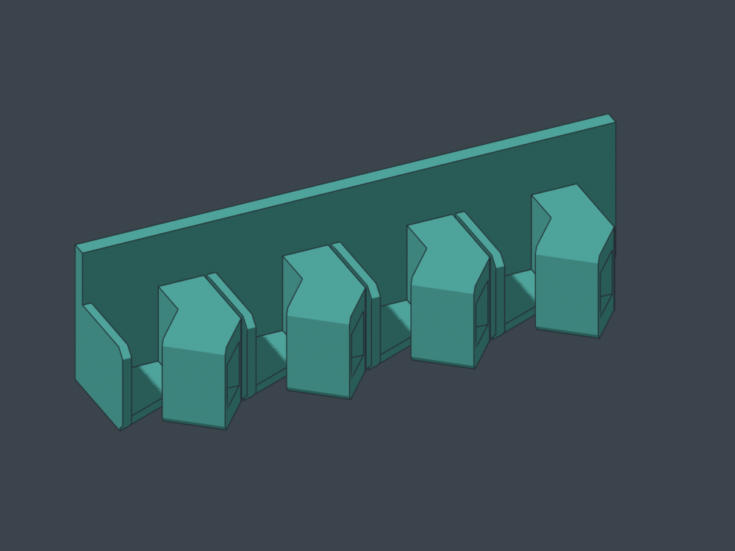
docs/gallery/tweezers/part-solder-modules-tweezers__v7__print.png
