thereprocase/peg/docs/gallery/tweezers/part-solder-modules-tweezers__v8__long-body-cradle__fit-e586ab4ff6__test-piece.png

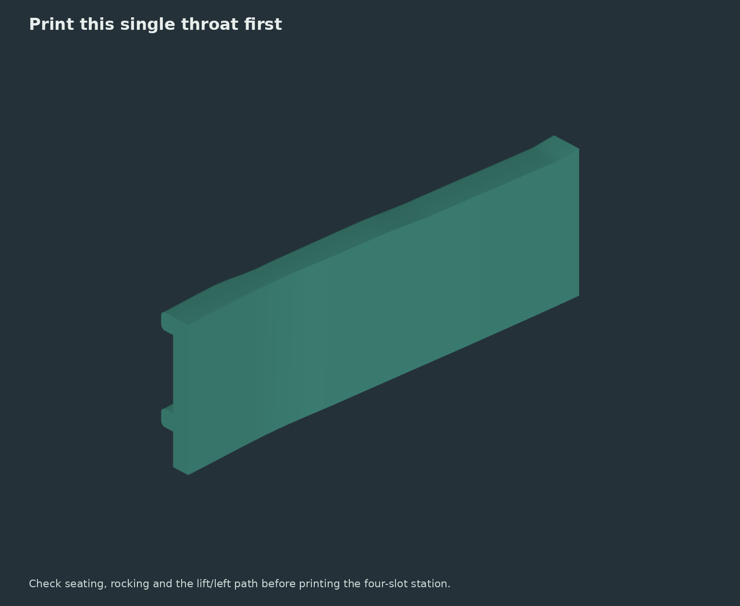
docs/gallery/tweezers/part-solder-modules-tweezers__v8__long-body-cradle__fit-e586ab4ff6__test-piece.png
