thereprocase/peg/docs/gallery/tweezers/part-solder-modules-tweezers__v9__cheek-cradle__fit-pf02c9-latch__loaded.png

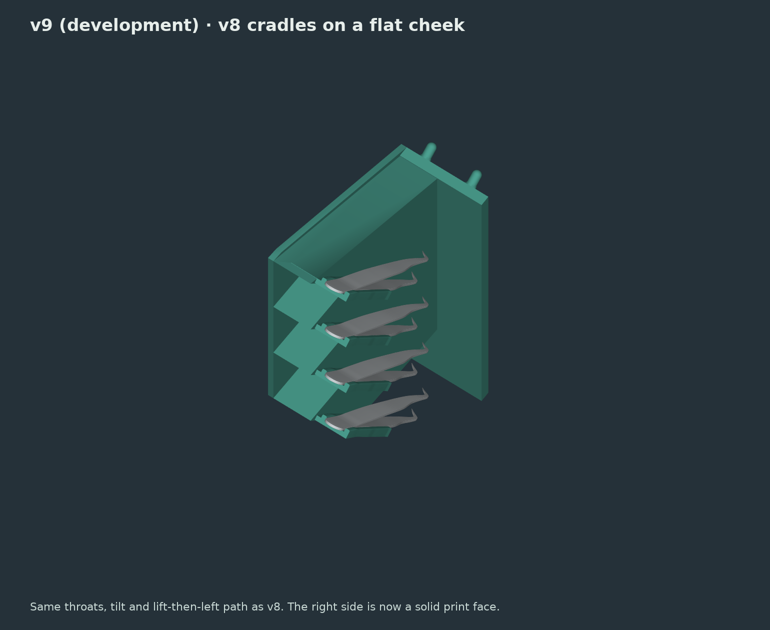
docs/gallery/tweezers/part-solder-modules-tweezers__v9__cheek-cradle__fit-pf02c9-latch__loaded.png
