thereprocase/peg/docs/gallery/tweezers/part-solder-modules-tweezers__v9__cheek-cradle__fit-pf02c9-latch__print.png

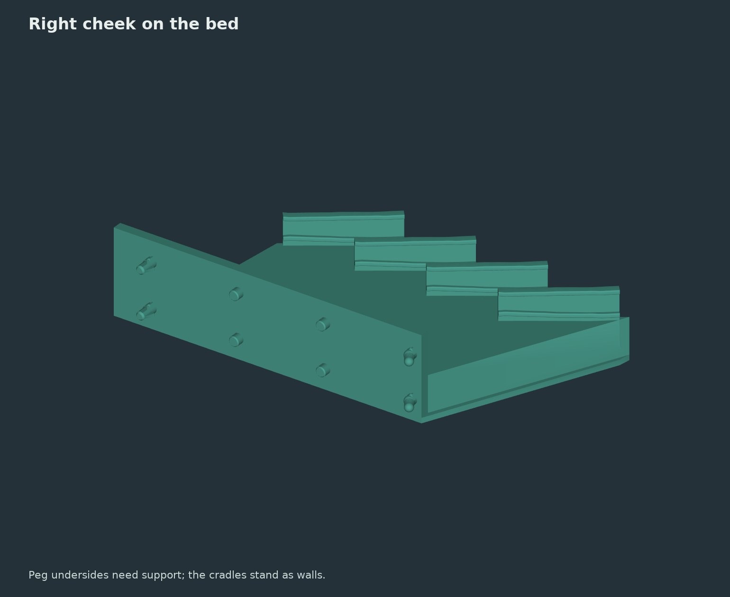
docs/gallery/tweezers/part-solder-modules-tweezers__v9__cheek-cradle__fit-pf02c9-latch__print.png
