thereprocase/peg/docs/gallery/tweezers/part-solder-modules-tweezers__v10__compact-right-cheek__fit-9328ccc5d4__loaded.png

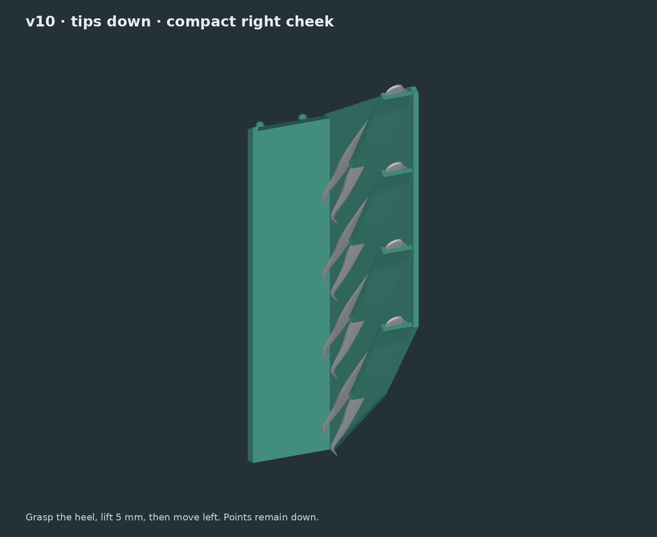
docs/gallery/tweezers/part-solder-modules-tweezers__v10__compact-right-cheek__fit-9328ccc5d4__loaded.png
